RicardoJBarrios/acuario-veril/03_pendientes/disenos-3d/bactoflex-mini/README.md

# Diseños de cestas BactoFlex Mini

Este proyecto conserva **dos versiones distintas** del diseño de cesta y
tapa. Son alternativas documentadas por separado; la nueva versión modular no
elimina ni reemplaza la otra.

- [Diseño modular 50 × 50 × 100 mm](modular-50x50x100/README.md): plan para
  dos cestas independientes, su modelo paramétrico y una vista CAD. Aún no
  impreso ni validado físicamente.
- [Versión 107 × 57 × 105 mm](version-107x57x105/README.md): modelo y archivos
  de fabricación de la otra versión, conservados en su propia carpeta.

La licencia compartida se conserva en [`LICENSE`](LICENSE). Cada carpeta
describe el estado y los límites de su propio modelo y derivados.
