RicardoJBarrios/acuario-veril/01_verilpedia/02_biologia/03_cnidarios-sesiles/README.md

# Cnidarios sésiles

Esta categoría reúne organismos sésiles o principalmente sésiles del filo Cnidaria que pueden formar parte de un acuario de arrecife. Incluye corales, gorgonias, anémonas, coralimorfarios, zoántidos y otros organismos coraliformes.

## Responsabilidad documental

Las fichas describen identidad, función, necesidades generales, crecimiento, agresividad, compatibilidad y límites de interpretación. Las decisiones concretas de selección y colocación se documentan en la [implementación de Veril](../../../02_configuracion/README.md) y en las dimensiones correspondientes.

## Fichas disponibles

- [Corales](01_corales/README.md): corales blandos, LPS, NPS y SPS
- [Análogos coraliformes](02_analogos-coraliformes/README.md): anémonas, coralimorfarios y zoántidos
- [*Aiptasia* y majano](aiptasia-y-majano.md): anémonas oportunistas y límites de identificación
- [Salud de corales](01_corales/06_salud/README.md) y [plagas asociadas](01_corales/05_plagas/README.md)

## Referencias cuantitativas para interpretar las fichas

Las fichas individuales deben incluir una tabla de parámetros medibles según la [plantilla de organismos](../plantilla-ficha-organismo.md). La siguiente tabla distingue referencias generales de acuariofilia y la configuración local; no son límites fisiológicos universales ni sustituyen un dato publicado para la especie.

| Magnitud | Referencia cuantitativa | Alcance |
| --- | --- | --- |
| Temperatura | Veril: preferida **25–26 °C**, objetivo normal **24,5–26,5 °C**; **24–24,5 °C** fresca; **23–24 °C** excursión fría, investigar si persiste; **<23 °C** fuera del objetivo; **<22 °C** revisión prioritaria. Banda cálida vigente: **26,5–27,5 °C** | Criterio local del sistema, no tolerancia declarada de cada especie; los límites publicados de cada especie pueden ser más restrictivos |
| Salinidad | Veril: objetivo **`S_P = 35`** | Consigna del sistema, no intervalo de tolerancia de cada organismo |
| pH | Referencia general de acuario de arrecife **8,0–8,4** | Orientación general; registrar escala y método si se conocen |
| PAR de corales blandos | **50–150 µmol fotones m⁻² s⁻¹** como intervalo inicial de grupo | Referencia de cuidado acuarístico; especies y morfos pueden diferir |
| PAR de LPS | **50–150 µmol fotones m⁻² s⁻¹** como intervalo inicial de grupo | No sustituye un rango de especie. Hay LPS con necesidades distintas |
| PAR de SPS | **200–300 µmol fotones m⁻² s⁻¹** como referencia inicial para géneros exigentes; *Anacropora* se documenta en **100–300** | No extrapolar el extremo alto a toda especie SPS |
| PAR de NPS | No aplica como fuente nutricional | Indicar que la luz no aporta nutrición fotosintética; el fotoperiodo del acuario no equivale a necesidad de PAR |
| Velocidad del flujo | **5–20 cm/s** puede servir como banda experimental de partida para estudiar corales pétreos; no es un objetivo universal de colocación | Estudios distintos obtienen respuestas específicas de especie, morfología y régimen. No convertir caudal de bomba o renovaciones/h en velocidad en la colonia |
| Volumen mínimo | No existe un mínimo universal en litros para un cnidario sésil | Priorizar área disponible, dimensiones adultas, movilidad, distancia de contacto y capacidad de alimentación/exportación |

El PAR se medirá bajo el agua en la posición y altura previstas para el organismo, con el **DanoPlus DP-414** de Veril. Registrar el valor en µmol fotones m⁻² s⁻¹, la posición, orientación del sensor, profundidad, fotoperiodo y perfil de la luminaria. Porcentaje de potencia, vatios, altura del coral y color visual no permiten deducir el PAR local.

Los intervalos de **5–20 cm/s** reúnen velocidades ensayadas en estudios de corales, no una prescripción común a todos los cnidarios. Por ejemplo, *Balanophyllia europaea* capturó más presas a **5 cm/s** en un ensayo, mientras que *Sinularia flexibilis* mostró su mayor crecimiento medio a **11 cm/s** bajo las condiciones de otro ensayo. No se promediarán como si fueran medidas equivalentes ni se trasladarán directamente a otra especie. Se medirán en la ubicación de la colonia con un método de velocidad local; si no se dispone de medidor, la velocidad queda pendiente aunque se registre el comportamiento del tejido como observación auxiliar.

Fuentes cuantitativas:

- [Tidal Gardens: Acropora](https://tidalgardens.com/articles/coral-care-articles/acropora-coral-care.html), alrededor de 300 PAR en sus sistemas de mantenimiento y advertencia de aclimatación
- [Tidal Gardens: Montipora](https://tidalgardens.com/articles/coral-care-articles/montipora-coral-care.html), 125–150 PAR como inicio y 200–300 PAR en sus sistemas
- [Tidal Gardens: Anacropora](https://tidalgardens.com/articles/coral-care-articles/anacropora-coral-care.html), 100–300 PAR
- [Tidal Gardens: Goniopora](https://tidalgardens.com/articles/coral-care-articles/goniopora-coral-care.html), recomendación 75–125 PAR y experiencia entre 50 y más de 200 PAR
- [Schutter et al., 2007: flujo y crecimiento de *Sinularia flexibilis*](https://doi.org/10.1016/j.jembe.2007.06.007), medición experimental; mayor crecimiento medio a 11 cm/s bajo sus condiciones
- [Cocito et al., 2012: flujo y captura de presas de *Balanophyllia europaea*](https://doi.org/10.1017/S002531541100146X), velocidades ensayadas de 2,5, 5, 7,5 y 15 cm/s; mayor captura a 5 cm/s

Cuando una ficha no tenga un intervalo de especie, deberá decirlo explícitamente y usar los valores generales solo como punto de partida de medición, no como garantía de compatibilidad. La ficha también identificará necesidades que no puedan reducirse a un valor único, por ejemplo la turbulencia, dirección del flujo, expansión de tentáculos o alimentación de NPS.
