RicardoJBarrios/acuario-veril/01_verilpedia/04_hardware/urna/espuma.md

# Espuma de apoyo

## Producto

La interfaz entre el tablero y la base de la urna será una pieza continua de goma EVA BIBODU.

- Formato del rollo: **150 × 32 cm**
- Pieza para la urna: **75 × 32 cm**
- Grosor: **5 mm**
- Densidad declarada: **80 kg/m³**
- Dureza declarada: **25 kPa**
- Material declarado: **100 % EVA foam**
- Color: **Negro**

La pieza de 75 × 32 cm cubre una superficie aproximada de **0,24 m²** y deja un sobrante de aproximadamente 75 × 32 cm.

## Función

La EVA forma una interfaz continua entre el tablero y la base de vidrio, reparte el contacto y absorbe pequeñas irregularidades superficiales. La pieza se colocará completa, sin solapes ni juntas, sobre un tablero rígido, plano, limpio y nivelado.

## Colocación

La pieza se extenderá bajo toda la base, sin pliegues, cortes, arrugas ni bordes levantados. Se mantendrá seca y sin adhesivo salvo indicación del fabricante de la urna.

## Datos comerciales

El anuncio del producto declara impermeabilidad y moldeabilidad con calor. No se dispone de una ficha técnica primaria que detalle la absorción de agua, la deformación permanente, la capacidad de carga prolongada o la compatibilidad química con silicona, vidrio, vinilado y agua salada.

La espuma quedará bajo la urna y no estará en contacto directo con el agua del acuario.

## Estado

- Material: **EVA BIBODU de 5 mm**
- Medida de la pieza: **75 × 32 cm**
- Pieza continua: Disponible a partir del rollo documentado
- Aceptación del fabricante de la urna: Pendiente
- Nivelación del tablero: Pendiente de comprobación

## Referencias

- [BIBODU, rollo de goma EVA de 150 × 32 cm, 5 mm y 80 kg/m³](https://oficina.wikicolegios.com/comprar/bibodu-pack-de-2-rollos-de-goma-eva-5mm)
- [Artículo técnico sobre comportamiento mecánico de EVA de célula cerrada de 80 kg/m³](https://pmc.ncbi.nlm.nih.gov/articles/PMC10780418/)
- [EVA marina de célula cerrada: propiedades declaradas por fabricante](https://www.ycdeck.com/faq)
- [Ficha técnica de espuma EVA de célula cerrada con ensayos de absorción y compresión](https://foamatelier.nl/basis/data/mediablocks/TechnischeFicheEVAFoam.pdf)
