RicardoJBarrios/acuario-veril/01_verilpedia/04_hardware/dd-h2ocean-compact-ato/graf-barril-agroalimentario-15l.md

# Barril agroalimentario GRAF de 15 l

## Identificación

- **Fabricante o marca:** GRAF
- **Tipo:** depósito exterior rígido
- **Capacidad nominal:** 15 l
- **Material:** polietileno apto para uso alimentario
- **Color:** blanco translúcido
- **Formato:** redondo, con asa de transporte y grifo incluido
- **Medidas comerciales:** 35 cm de diámetro × 30 cm de altura
- **Fabricación declarada:** Alemania

## Características declaradas

El depósito está destinado a conservar líquidos y permite comprobar visualmente el nivel gracias a su material translúcido. La ficha comercial lo describe como hermético, de paredes gruesas y apto para conservar agua, zumo o vino, entre otros líquidos.

| Parámetro | Valor declarado |
| --- | --- |
| Uso | Contenedor de agua potable o no potable |
| Capacidad | 15 l |
| Material principal | Polietileno |
| Tipo de depósito | Rígido |
| Protección UV | Sí |
| Resistencia a heladas | No; sensible a las heladas |
| Garantía | 3 años |
| Peso neto | 1 kg |
| Enterrable | No |

## Uso en Veril

Este depósito se reservará exclusivamente para agua RO/DI de reposición.

- No se almacenará agua salada
- No se añadirán suplementos, fertilizantes, medicamentos ni productos de mantenimiento
- Se mantendrá cerrado y protegido de contaminación, polvo y salpicaduras
- El grifo no sustituye la protección antisifón del tubo de reposición del ATO
- La bomba del ATO se instalará de forma que no pueda aspirar sedimento del fondo
- La capacidad útil real y la autonomía se registrarán después de la instalación

Las dimensiones del depósito deben comprobarse junto con el espacio de instalación, el recorrido del tubo y el acceso para llenado y limpieza. La capacidad nominal de 15 l no equivale necesariamente al volumen que conviene utilizar en cada ciclo de reposición.

## Estado

**Confirmado:** depósito seleccionado para alimentar el D-D H2Ocean Compact ATO de Veril.

**Pendiente de ejecución:** confirmar la referencia comercial exacta, medir el espacio disponible, fijar el recorrido del tubo, comprobar la estanqueidad del grifo y registrar la autonomía real.

## Fuente

Descripción comercial de Leroy Merlin facilitada para la documentación de Veril. La ficha comercial identifica la marca como **GRAF** y declara las características recogidas en este documento.
