RicardoJBarrios/acuario-veril/01_verilpedia/03_parametros/temperatura.md

# Temperatura

## Qué es y qué mide

La temperatura describe el estado térmico del agua en un momento y una ubicación determinados. Condiciona la velocidad de muchas reacciones químicas, el metabolismo de los organismos, la actividad microbiana y la solubilidad de los gases.

La respuesta biológica no depende únicamente de la temperatura instantánea. También importan la duración de la exposición, la magnitud de la desviación respecto al régimen habitual, la velocidad con la que se alcanza y el historial térmico del organismo o la colonia.

## Qué aporta y por qué importa

La temperatura afecta a prácticamente todos los procesos del acuario:

- Modifica el metabolismo y el consumo de oxígeno
- Influye en la solubilidad de los gases
- Altera la velocidad de crecimiento, respiración y descomposición
- Participa en la química del sistema carbonato
- Modifica, junto con el pH y la salinidad, el equilibrio entre NH₄⁺ y NH₃ y la fracción de amoníaco no ionizado
- Modifica la densidad del agua y condiciona la interpretación de instrumentos dependientes de temperatura, como determinadas mediciones de gravedad específica, conductividad o refracción
- Condiciona el intercambio de calor entre el agua, los equipos y el ambiente

Las velocidades metabólicas y microbianas suelen depender de la temperatura dentro de determinados intervalos, pero la relación no es indefinidamente creciente: cada comunidad presenta rangos, óptimos y límites propios.

## Niveles orientativos

Como referencia operativa doméstica puede utilizarse aproximadamente **24–26 °C** para muchas comunidades tropicales de arrecife. Este intervalo no constituye un rango fisiológico universal ni permite establecer por sí solo un umbral de estrés térmico.

La estabilidad y la velocidad de cambio son importantes, pero no sustituyen la compatibilidad del valor absoluto con los organismos mantenidos. Una temperatura estable fuera de su intervalo tolerable sigue constituyendo una condición inadecuada.

No existe un umbral universal de blanqueamiento expresable como una única temperatura. El estrés depende en gran medida del régimen térmico habitual de procedencia, de la especie, la población, la colonia, los simbiontes y la duración e intensidad de la exposición.

## Exposición y estrés térmico

Una excursión breve y moderada puede producir una respuesta distinta de una exposición sostenida a la misma temperatura. Del mismo modo, los umbrales de estrés térmico no son idénticos entre especies, poblaciones, colonias o asociaciones simbióticas.

La aclimatación fisiológica de un individuo o una colonia no debe confundirse con la adaptación evolutiva de una población. La aclimatación puede modificar la respuesta dentro de ciertos límites, pero no convierte cualquier temperatura en compatible ni elimina el riesgo de estrés acumulado.

## Balance y carga térmica

La temperatura del agua resulta del balance entre ganancias y pérdidas de calor. La temperatura ambiente no determina por sí sola la temperatura del acuario: equipos sumergidos, iluminación, radiación, evaporación, ventilación, conducción y geometría del sistema pueden desplazarla respecto al ambiente.

La **carga térmica** representa el conjunto de aportes de calor que el sistema debe disipar, incluidos equipos sumergidos, iluminación, ambiente y radiación. Su importancia depende también de la capacidad de disipación por conducción, convección, evaporación y ventilación.

La iluminación puede incrementar la temperatura por transferencia de energía desde la luminaria y el entorno; este efecto debe distinguirse de la propia actividad fotosintética.

El enfriamiento evaporativo puede reducir eficazmente la temperatura, pero aumenta la pérdida de agua y hace más dependiente al sistema de una reposición correcta. La evaporación elimina principalmente agua, no una cantidad equivalente de sales, por lo que vincula directamente regulación térmica y estabilidad de salinidad.

## Temperatura y margen de oxígeno

El aumento de temperatura puede reducir simultáneamente la solubilidad del oxígeno y aumentar la demanda metabólica de los organismos y microorganismos. Por ello, el riesgo térmico puede reducir también el margen disponible frente a hipoxia, especialmente durante la oscuridad, ante una elevada carga respiratoria o tras un fallo de circulación.

El efecto térmico sobre el oxígeno debe interpretarse junto con salinidad y presión atmosférica cuando se compara una concentración medida con la saturación esperada. La relación con el oxígeno no permite establecer por sí sola un umbral térmico universal.

## Fuentes y comportamiento

La temperatura puede variar:

- Entre el día y la noche
- Según la estación
- Por la iluminación, las bombas y otros equipos
- Por ventilación, evaporación o temperatura ambiente
- Por el uso de calefacción o refrigeración
- Por cambios en la circulación o en la mezcla del agua

Una variación pequeña y reproducible dentro de condiciones compatibles puede formar parte del régimen normal del sistema. El objetivo no debe ser eliminar toda variación, sino evitar exposiciones incompatibles, oscilaciones excesivas y cambios rápidos no controlados.

### Gradientes térmicos

En un sistema bien mezclado se espera una temperatura relativamente homogénea, pero pueden aparecer diferencias locales junto a calentadores, salidas calientes, superficies iluminadas o cámaras con renovación reducida. Un gradiente persistente debe interpretarse como información sobre la distribución térmica y la hidráulica, no únicamente como un problema del sensor.

## Qué pasa si está bajo

Una temperatura baja puede reducir la velocidad metabólica y ralentizar procesos biológicos. Un descenso rápido puede causar estrés y modificar simultáneamente la solubilidad de los gases, los equilibrios químicos y la interpretación de instrumentos dependientes de temperatura; no modifica por sí solo la cantidad de sales presentes.

Un cambio térmico puede modificar el pH y la especiación del sistema carbonato aunque no exista una adición de ácido, base o CO₂. Por ello, las comparaciones químicas deben conservar la temperatura de medición o aplicar la corrección apropiada.

## Qué pasa si está alto

Una temperatura alta puede acelerar el metabolismo y aumentar el consumo de oxígeno. Si coincide con pH elevado y nitrógeno amoniacal presente, debe vigilarse el equilibrio entre NH₄⁺ y NH₃ y la fracción de amoníaco no ionizado.

El sobrecalentamiento sostenido puede reducir la solubilidad del oxígeno, elevar la demanda respiratoria y producir estrés térmico acumulado. La importancia depende del valor, la duración, la velocidad de cambio y la comunidad afectada.

## Cómo se mide

- Termómetro digital con sonda sumergible
- Sonda electrónica integrada en un controlador, si se calibra y contrasta periódicamente
- Termómetro de vidrio con líquido adecuado, preferentemente sin mercurio, como comprobación independiente
- Termómetro infrarrojo, solo como referencia de superficies; no sustituye una medición del agua en profundidad

Un termómetro infrarrojo mide la radiación emitida por la superficie observada y no la temperatura del agua en profundidad. El vidrio, los reflejos y la emisividad pueden sesgar la lectura.

## Limitaciones de la medición

La lectura depende de la calibración, la resolución, el tiempo de respuesta, la posición del sensor y la mezcla del sistema. Debe evitarse colocar la sonda pegada al calentador, a una salida caliente, en una cámara con renovación insuficiente o en una zona que pueda quedar parcialmente expuesta al aire.

Un sensor puede registrar una zona local y no representar todo el volumen si existen gradientes térmicos o fuentes de calor cercanas. La medición y el control deben distinguirse: un controlador puede actuar correctamente sobre una lectura sesgada por la ubicación del sensor.

## Mecanismos de regulación

La temperatura se regula mediante calefacción, ventilación, enfriamiento o reducción de fuentes de calor. Las correcciones deben realizarse de forma controlada, evitando introducir una segunda perturbación térmica innecesariamente rápida. En una emergencia, la prioridad es recuperar condiciones compatibles mientras se controla la velocidad y la respuesta de los organismos.

Cuando las consecuencias de un fallo sean relevantes, la medición, el control y el corte de seguridad no deberían depender necesariamente de un único punto de fallo. La seguridad térmica debe considerar tanto el sobrecalentamiento como la pérdida de calefacción o un enfriamiento excesivo.

El control térmico suele utilizar una histéresis o banda de actuación para evitar ciclos rápidos de encendido y apagado. Una banda demasiado estrecha puede aumentar la frecuencia de conmutación sin proporcionar una mejora biológica relevante.

La capacidad de regulación depende del volumen, el ambiente, la evaporación, la iluminación, la carga térmica y la circulación. Un fallo de circulación puede alterar simultáneamente la mezcla térmica y el margen de oxígeno.

## Interpretación y respuesta

Medir con un termómetro fiable, comprobarlo periódicamente y registrar máximas y mínimas. Una serie térmica se describe mejor mediante temperatura media, máxima, mínima, amplitud diaria y velocidad de cambio que mediante una única lectura.

```text
ΔT_diaria = T_máxima − T_mínima
tasa de cambio = ΔT / Δt
```

No existe una tasa universalmente segura para todos los organismos, pero debe conservarse al interpretar incidentes, aclimataciones o intervenciones.

Una desviación debe interpretarse junto con máximas, mínimas, amplitud, velocidad del cambio, oxígeno, salinidad, pH y comportamiento de los organismos.

## Cómo evaluar la temperatura en funcionamiento

- **Medición:** Sensor contrastado, ubicación representativa, resolución suficiente y registro continuo o de máximas y mínimas
- **Régimen:** Media, máxima, mínima, amplitud diaria, tasa de cambio y patrón estacional cuando exista
- **Seguridad:** Control de sobretemperatura, detección de fallo de calefacción, respuesta ante pérdida de circulación y margen frente a máximas ambientales previsibles
- **Biología:** Comportamiento, respiración, respuesta de corales y relación con oxígeno y fotoperiodo

## Otros parámetros relacionados

- **pH y amonio:** La temperatura, el pH y la salinidad modifican el equilibrio entre NH₄⁺ y NH₃ y la fracción de amoníaco no ionizado
- **Oxígeno:** El agua caliente suele contener menos oxígeno en saturación y los organismos pueden aumentar su demanda metabólica
- **Salinidad:** La temperatura afecta a la densidad, la conductividad y la lectura de gravedad específica, pero no modifica por sí sola la cantidad de sales presentes
- **Sistema carbonato:** La temperatura modifica las constantes de equilibrio y los productos de solubilidad de las fases minerales, alterando la especiación y el estado de saturación incluso sin que cambien inicialmente TA o DIC
- **Metabolismo:** Una subida térmica puede aumentar consumo, producción de residuos y demanda de oxígeno dentro de los límites fisiológicos de la comunidad
- **Hidráulica:** La circulación distribuye el calor y condiciona la existencia de gradientes térmicos locales
- **Iluminación:** La luminaria puede aportar carga térmica independientemente de la actividad fotosintética

## Qué no es la temperatura

La temperatura:

- No es una cifra independiente del tiempo
- No se define únicamente por una lectura instantánea
- No demuestra una oxigenación adecuada
- No compensa una mala calidad química
- No permite inferir el metabolismo exacto mediante una regla universal
- No convierte una oscilación natural en necesariamente segura para cualquier organismo
- No demuestra ausencia de estrés porque los animales sigan abiertos o activos

## Qué no demuestra una lectura aislada

Una temperatura aparentemente normal no compensa una salinidad incorrecta, falta de oxígeno, pH inestable o acumulación de compuestos nitrogenados. Tampoco demuestra que no exista estrés térmico acumulado, un gradiente local o un margen insuficiente frente a una perturbación previsible.

## Errores comunes

- Perseguir una consigna como 25,0 °C mediante conmutaciones constantes
- Utilizar un único sensor sin contrastarlo
- Colocar la sonda junto al calentador o una salida caliente
- Ignorar máximas y mínimas diurnas y nocturnas
- Enfriar bruscamente una hipertermia sin controlar la respuesta
- Interpretar la temperatura ambiente como temperatura del agua
- Olvidar que los ventiladores aumentan la evaporación y la dependencia de la reposición
- Calibrar todos los sensores contra otro sensor no verificado
- Ignorar que un fallo de bomba puede alterar simultáneamente la mezcla térmica y el oxígeno

## Terminología

| Expresión | Qué representa |
| --- | --- |
| Temperatura del agua | Estado térmico medido en una muestra o ubicación concreta |
| Carga térmica | Aportes de calor que el sistema debe disipar |
| Inercia térmica | Resistencia del sistema a cambiar de temperatura por su masa térmica y su intercambio de calor |
| Amplitud diaria | Diferencia entre la temperatura máxima y mínima de un ciclo diario |
| Tasa de cambio | Variación de temperatura por unidad de tiempo |
| Estrés térmico | Respuesta biológica a una temperatura, desviación, duración o velocidad de cambio incompatibles o exigentes |
| Aclimatación | Ajuste fisiológico dentro de los límites de un organismo o colonia expuestos a nuevas condiciones |
| Adaptación | Cambio heredable a escala poblacional o evolutiva; no equivale a aclimatación individual |
| Histéresis | Banda de diferencia entre los puntos de activación y desactivación de un controlador |
| Infrarrojo | Medición de radiación superficial que no equivale directamente a la temperatura del agua en profundidad |

## Fuentes

- [USGS: Temperature and water](https://www.usgs.gov/water-science-school/science/temperature-and-water), efectos de la temperatura sobre solubilidad, reacciones y organismos acuáticos
- [NOAA: Temperature and oxygen tolerances of marine species](https://coastalscience.noaa.gov/news/temperature-and-oxygen-tolerances-of-marine-species-predict-their-distributions/), relación entre temperatura, oxígeno y tolerancia de organismos marinos
- [Berkelmans y van Oppen: The susceptibility and resilience of corals to thermal stress: adaptation, acclimatization or both?](https://doi.org/10.1111/j.1365-294X.2010.04575.x), susceptibilidad, resiliencia, aclimatación y asociaciones simbióticas
- [Safaie et al.: A global analysis of coral bleaching over the past two decades](https://doi.org/10.1073/pnas.1808831115), relación entre intensidad, frecuencia e historia del estrés térmico y blanqueamiento
- [ReefCalcs: Parámetros ideales de arrecife](https://reefcalcs.com/guides/ideal-reef-parameters/), referencia práctica de rango y estabilidad
- [ReefCalcs: Calculadora de refrigeración](https://reefcalcs.com/calculators/chiller-btu/), relación práctica entre temperatura, carga térmica y ambiente
