RicardoJBarrios/acuario-veril/04_operaciones/2026/09/2026-09-28-vaciado-remanente-barril-y-nivel-c3.md

# 2026-09-28 — Vaciado del remanente del barril y nivel de C3

## Estado

Operación documentada a partir de una observación comunicada por el propietario.
La hora se estima a partir de «hace un minuto» respecto al mensaje recibido a
las 09:13 WEST; no se comunicó una hora de reloj exacta.

## Ejecución comunicada

El propietario vació en el sistema el remanente de agua que quedaba en el barril
tras la operación del 26 de septiembre. Confirma que entraron **1,75 L** en el
sistema y que el barril quedó vacío.

Por el contexto de las operaciones recientes, se interpreta que la cota
comunicada después de la transferencia corresponde al nivel de agua de C3,
medido desde su borde superior. Si se refería a otra cámara o referencia, este
registro debe corregirse.

## Resultado observado

Después de vaciar el remanente, el nivel de C3 quedó a **14 cm (140 mm) del
borde superior**, según la medición comunicada por el propietario. No se indicó
el instrumento ni se confirmó que se usara exactamente el mismo punto del borde
que en la lectura anterior.

Como comparación contextual, el 27 de septiembre se había comunicado una cota
de **16 cm (160 mm)**. La lectura actual está 20 mm más cerca del borde; la
diferencia describe únicamente las dos cotas comunicadas.

## Telemetría asociada de Home Assistant

La documentación consultada no identifica una entidad de Home Assistant que
mida el nivel de C3. No se adjunta una lectura digital como corroboración de la
cota: los **140 mm** son una medición física comunicada por el propietario. En
esta operación no se obtuvo una consulta en vivo de Home Assistant.

## Interpretación y límites

- El propietario confirma un volumen transferido de **1,75 L** y que el barril quedó vacío; la cota final comunicada para C3 es de 140 mm desde el borde superior.
- La diferencia de 20 mm respecto a los 160 mm comunicados el día anterior solo es comparable si se mantuvieron la cámara, el borde y el punto de referencia; esos detalles no se confirmaron expresamente.

## Fuentes internas

- [Reposición manual y lectura de salinidad del 26 de septiembre](2026-09-26-reposicion-manual-y-lectura-de-salinidad.md)
- [Prueba del DanoPlus, PAR ambiental y nivel de C3 del 27 de septiembre](2026-09-27-prueba-danoplus-nivel-c3-y-par.md)
