RicardoJBarrios/acuario-veril/01_verilpedia/05_productos/09_fritzzyme-9/fritzzyme-9.md

# FritzZyme 9 Saltwater

## Identificación

- Producto: **FritzZyme 9 Saltwater Nitrifying Bacteria**
- Fabricante: **Fritz Aquatics**
- Envase adquirido: **946 ml**
- Referencia oficial del formato de 946 ml: **80205**; la referencia **80203** corresponde al formato de 237 ml
- Cobertura indicada en la tabla oficial para el envase de 946 ml: hasta **160 galones estadounidenses / 606 L**; por cálculo, esa cifra es aproximadamente compatible con la pauta de sistema establecido, no con la dosis inicial de sistema nuevo

La capacidad de 40 galones debe interpretarse junto con la pauta aplicable. Fritz publica una dosis distinta para sistemas nuevos y sistemas establecidos.

## Función declarada por el fabricante

FritzZyme 9 contiene cepas vivas de bacterias nitrificantes específicas para agua salobre y salada. El fabricante declara que ayudan a sembrar rápidamente el biofiltro y a transformar amonio y nitrito.

Esta es una afirmación del fabricante. La documentación pública consultada no permite identificar aquí las cepas concretas del envase adquirido ni su viabilidad por lote.

## Uso y condiciones publicadas

- Sistema nuevo: la etiqueta del envase disponible indica **118 ml por 19 L** (4 fl oz por 5 galones estadounidenses); la página oficial redondea la cantidad a **119 ml**
- Sistema establecido: **30 ml por 19 L** (1 oz por 5 galones estadounidenses)
- La etiqueta indica que la dosis puede repetirse diariamente si es necesario y que para una carga elevada de animales puede aumentarse hasta diez veces; esto no forma parte de la receta adoptada para Veril
- La web oficial también contempla un aumento de hasta diez veces para sistemas con carga biológica elevada
- Temperatura ideal: **25–30 °C**
- Salinidad: **15–40 ppt** (densidad específica 1.011–1.030)
- pH: **7,3–8,0**
- Alcalinidad mínima: **4,5 dKH** o 80,5 ppm KH
- Fosfato: Por encima de 0 ppm
- La etiqueta del envase indica detener el uso de esterilizadores UV antes de añadir el producto y hasta cuatro días después de cada aplicación
- La web oficial indica mantener apagados el skimmer y los esterilizadores UV durante al menos cinco días después de cada aplicación; el plan de Veril conserva este plazo más largo
- Mantener flujo o aireación adecuados

Fritz indica que en un sistema nuevo debe existir una fuente de amonio, como Fishless Fuel, para iniciar el ciclado sin peces.

## Conservación y límites

El fabricante indica que el producto no necesita refrigeración para conservarse estable a largo plazo. No debe congelarse ni sobrecalentarse y debe almacenarse en un lugar fresco y oscuro. Debe utilizarse antes de la fecha de caducidad.

Los cambios de color u olor pueden producirse entre envases. Un olor fuerte a azufre no demuestra por sí solo que el producto haya perdido su actividad. La comprobación funcional requiere medir la transformación de amonio y nitrito bajo una carga conocida.

## Aplicación prevista en Veril

FritzZyme 9 se utilizará como inoculante bacteriano principal del ciclado sin peces, junto con AF Bio Sand, Fishless Fuel y el agua de mar filtrada con UV de Elite Reef Kanarias. La dosis de Veril se calcula en el [plan de ciclado](../../../03_pendientes/ciclado/plan.md), usando la base nominal adoptada de **75 L para el sistema completo**.

La etiqueta fotografiada del envase disponible indica **118 ml por 19 L** para un sistema nuevo. Aplicada a los **75 L** nominales de Veril, equivale a **465,8 ml**, que se redondean a **466 ml**. La web oficial usa el valor redondeado de 119 ml por 19 L, que daría 469,7 ml. Para el plan de Veril prevalece la etiqueta del envase concreto. El formato adquirido contiene **946 ml**, suficiente para esta dosis.

El vendedor recomendó utilizar la mitad de la dosis. Esa recomendación no aparece identificada como pauta específica para FritzZyme 9 en la documentación oficial consultada. Para la receta de ciclado de Veril se adopta la dosis completa de sistema nuevo indicada por la etiqueta, aproximadamente **466 ml para 75 L**. La recomendación de media dosis se conserva como antecedente comercial no adoptado, no como decisión pendiente ni como pauta del fabricante. La fotografía disponible no muestra lote ni caducidad; ambos se comprobarán antes de dosificar.

La [fotografía de la etiqueta del envase de Veril](etiqueta-envase-veril-2026-09-24.jpg), tomada el 24 de septiembre de 2026, conserva la pauta y las instrucciones visibles del producto adquirido. El fabricante indica agitarlo y añadirlo directamente al acuario, retirar el cloro previamente y mantener circulación o aireación. La etiqueta menciona apagar UV antes y durante los cuatro días posteriores; la web oficial amplía la precaución a skimmer y UV durante al menos cinco días, criterio que sigue el plan.

## Fuente

- [Fritz Aquatics: FritzZyme 9 Saltwater](https://fritzaquatics.com/product/fritzzyme-9-saltwater/)
