RicardoJBarrios/acuario-veril/04_operaciones/2026/09/2026-09-17-observaciones-flujo-temperatura-y-sustrato.md

# 2026-09-17 — Observaciones de flujo, temperatura y sustrato

## Naturaleza del registro

Este registro reúne observaciones comunicadas por el propietario durante la
preparación de Veril. No incorpora fuentes externas, datos de fabricante,
interpretaciones de vídeos ni conclusiones sobre la sostenibilidad del régimen.
Cuando no se conoce la fecha exacta de una observación, se conserva como tal y
no se infiere.

## Estado físico observado

- El ciclado todavía no había comenzado.
- En el momento de estas observaciones no había arena: sólo estaba colocada la
  roca.
- El nivel de agua de referencia se situaba aproximadamente **37 mm** por
  debajo del borde superior del acuario.
- La aragonita utilizada se observó como un material pesado que se hunde con
  rapidez al incorporarlo.

## Bomba de movimiento

El propietario comunicó la siguiente colocación y configuración actual de la
bomba de olas:

- Aproximadamente **12 cm** desde el borde del acuario; esta medida se debe
  interpretar junto con el nivel de agua de **37 mm** indicado arriba.
- Aproximadamente **53 mm** desde la parte trasera, descontando de esa medida
  el grosor del cristal trasero.
- Orientada hacia el frente.
- `Constant mode`.
- `Flow percent: 40 %`.
- `Cycle: 0,4 s`, indicado como el mínimo disponible.
- `Master` configurado, porque el controlador no permite dejarlo sin ajustar.

También se comunicó que existe un vídeo local en Descargas donde se aprecia el
efecto conjunto de la bomba de salida y la Tourbon sobre la superficie del
agua. Este registro no interpreta ese vídeo ni lo usa como fuente externa.

## Prueba dinámica de circulación

Con la Mantis configurada entonces al 40 %, se realizó una prueba dinámica con
las partículas minúsculas de aragonita que permanecieron en suspensión en la
superficie. El resultado observado fue:

- Las partículas más pequeñas que permanecieron suspendidas en la superficie
  recorrieron circularmente el acuario.
- El recorrido rodeaba la roca.
- El comportamiento observado coincidió con el comportamiento esperado para
  esa prueba.

La prueba acredita un circuito superficial continuo alrededor de la roca bajo
esa configuración y durante esa observación. No acredita por sí sola la
renovación de todos los huecos, el corredor trasero o las zonas inferiores, ni
la ausencia de depósitos en otras condiciones o tras añadir arena.

## Telemetría asociada

No se consultó telemetría de Home Assistant para esta prueba. La evidencia
registrada es la observación directa comunicada por el propietario.

**Resultado:** Operación documentada sin telemetría pertinente o disponible.

## Temperatura del agua

El propietario indicó, tras revisar la evolución registrada por el medidor de
temperatura de Veril, que el agua se había mantenido entre **26 y 30 °C**
durante el tiempo observado hasta ese momento. En esta conversación no se
establecieron aquí el periodo exacto, la entidad del sensor ni la resolución de
la serie, por lo que no se añaden.

También indicó que el despacho dispone de aire acondicionado y que el periodo
coincidía con una ola de calor considerada inusual en Santa Cruz de Tenerife.
Este registro conserva esa comunicación como contexto aportado por el
propietario; no incorpora comprobaciones meteorológicas externas.

## Límites de la observación

Estas observaciones no determinan todavía si el rango térmico es sostenible,
si la bomba renueva todas las zonas del acuario ni si la distribución de
partículas se mantiene al añadir arena. Esas cuestiones quedan abiertas para
pruebas posteriores del sistema real.
