RicardoJBarrios/acuario-veril/01_verilpedia/08_practicas/04_diagnostico-y-bioseguridad/arbol-de-diagnostico.md

# Árbol de diagnóstico

```mermaid
flowchart TD
  A[Observación nueva] --> B{¿Afecta a un animal?}
  B -- No --> C{¿Película, moco o filamentos?}
  B -- Sí --> D{¿Hay pérdida de tejido o respiración alterada?}
  C -- Película parda --> E[Comparar diatomeas, ciano y dinos]
  C -- Moco o burbujas --> E
  C -- Filamentos --> F[Comparar algas y organismos sésiles]
  D -- No --> G[Revisar adaptación, muda, detrito y plagas]
  D -- Sí --> H[Registrar velocidad y separar causa posible]
  E --> I{¿La identificación cambia el tratamiento?}
  I -- Sí --> J[Microscopio o fuente competente]
  I -- No --> K[Retirada física y observación proporcional]
  F --> K
  G --> L[No eliminar organismos beneficiosos por apariencia]
  H --> M[Hospital o aislamiento según riesgo]
```

Ante una película marrón conviene comprobar si se desprende como polvo, si forma una matriz viscosa, si produce burbujas, si se concentra en arena y si disminuye durante la oscuridad. Estos datos solo separan posibilidades: *Ostreopsis*, *Amphidinium*, *Prorocentrum* y otros grupos pueden ser bentónicos y requieren una identificación más precisa si se plantea una intervención específica.

Nunca se debe apagar por completo la circulación, llevar nitrato o fosfato deliberadamente a cero, ni cambiar varias variables a la vez para forzar una lectura visual.
