RicardoJBarrios/acuario-veril/01_verilpedia/05_productos/06_dd-aquarium-solution-aqpr001/dd-aquarium-solution-aqpr001.md

# D-D The Aquarium Solution AQPR001

## Identificación

| Campo | Dato |
| --- | --- |
| Marca | D-D The Aquarium Solution |
| Producto | Refractómetro AQPR001 |
| Estado en Veril | Adquirido |

## Especificaciones declaradas

| Campo | Dato |
| --- | --- |
| Escala principal | Salinidad de agua marina, 0–40 ppt |
| Escala adicional | Gravedad específica de agua marina |
| Compensación | ATC entre 10 y 30 °C de temperatura del instrumento |
| Calibración declarada | 20 °C |
| Cuerpo | Cobre interno para favorecer la estabilización térmica |

## Función documentada

Instrumento óptico destinado a estimar la salinidad o la gravedad específica del agua marina mediante refracción. D-D indica que la escala está preparada para agua de mar real y no para salmuera de cloruro sódico, una diferencia relevante cuando se busca una lectura cercana a 35 ppt.

La compensación automática de temperatura no mide ni corrige directamente la temperatura del agua: compensa la temperatura del instrumento dentro del intervalo indicado. La muestra debe homogeneizarse y la calibración debe hacerse con el instrumento estabilizado a 20 °C.

## Uso en Veril

Se utilizará para comprobar la salinidad del agua de mar recibida y de las preparaciones posteriores. La calibración y el método de medición deben registrarse antes de aceptar una lectura.

## Límites

- Una lectura no demuestra que el instrumento esté correctamente calibrado
- El refractómetro no sustituye la comprobación de la temperatura y de la homogeneidad de la muestra
- La compensación automática de temperatura no elimina la necesidad de calibrar el instrumento a 20 °C
- No se debe convertir automáticamente una lectura de gravedad específica en salinidad sin conocer la escala utilizada
- La suciedad, las gotas retenidas, las burbujas y una muestra no representativa pueden alterar el resultado

## Fuentes

- Manual y escala del instrumento adquirido
- [D-D: True Seawater Refractometer AQPR001](https://www.theaquariumsolution.com/products/true-seawater-refractometer)
- [D-D: compensación de temperatura del refractómetro](https://www.theaquariumsolution.com/refractometer-temperature-compensation)
- [Aplicación química de Veril](../../../02_configuracion/01_dimensiones/05_quimica.md)
