RicardoJBarrios/acuario-veril/01_verilpedia/05_productos/07_eheim-4005843/eheim-4005843.md

# Tubo Eheim 4005843

## Identificación

| Campo | Dato |
| --- | --- |
| Marca | Eheim |
| Referencia | 4005843 |
| Medida disponible | 3 m, 16/22 mm |
| Estado en Veril | Adquirido |

## Especificaciones declaradas

| Campo | Dato |
| --- | --- |
| Color | Antracita |
| Diámetro nominal | 16/22 mm |
| Longitud | 3 m |
| Referencia | 4005843 |
| Uso de catálogo | Manguera Eheim para conexiones de filtración |

## Función documentada

Tubo flexible Eheim para conducción de agua en instalaciones de acuario. El catálogo lo identifica como manguera antracita de 16/22 mm y 3 m. La medida nominal no garantiza por sí sola compatibilidad con cualquier pasamuros, bomba o racor.

Eheim describe sus mangueras como flexibles y resistentes al estrangulamiento, pero la ruta instalada debe respetar radios, conexiones y sujeciones reales.

## Uso en Veril

Se reserva como material auxiliar para llenados, trasvases y conexiones temporales entre recipientes o cámaras. No forma parte del recorrido permanente de la bomba de retorno.

## Límites

- El recorrido debe comprobarse para evitar estrangulamientos, fugas y esfuerzos sobre los equipos
- No se debe sustituir el tubo de retorno sin una decisión específica y una comprobación de compatibilidad
- El tubo debe cortarse recto y las conexiones deben quedar completamente insertadas y aseguradas
- Para facilitar el montaje de un tubo rígido por frío puede templarse con agua caliente, evitando quemaduras y deformaciones

## Fuentes

- [Copia local del catálogo técnico Eheim](eheim-catalogo-tecnico-en-0923.pdf)
- [Ficha del hardware de la Sicce Micra Plus 600](../../04_hardware/sicce-micra-plus-600/sicce-micra-plus-600.md)
- [Eheim: catálogo de mangueras y referencia 4005843](https://eheim.com/media/3e/b6/2a/1737110772/EHEIM_Haendlerkatalog_EN_0923.pdf)
- [Aplicación hidráulica de Veril](../../../02_configuracion/01_dimensiones/03_hidraulica.md)
