RicardoJBarrios/acuario-veril/02_configuracion/README.md

# Veril: configuración integrada

> Esta ficha integra las decisiones concretas de Veril que se documentan por separado en las fichas del directorio. No sustituye las dimensiones, las fichas de hardware, las fichas de organismos ni los planes operativos.

## Alcance

Veril se configura como un acuario marino de arrecife con un display interior de **594 × 308 mm** y una altura exterior de **400 mm**, con una arquitectura AIO lateral de pequeño volumen, una configuración biológica mixta y una arquitectura de procesamiento basada en el método Berlín.

Además de los aproximadamente **7,5 kg de roca instalados**, el propietario comunica un remanente de roca no utilizado de **aproximadamente 2,5 kg**. La fecha concreta de ese pesaje no consta; el dato se registra en la [operación de pesaje del hardscape](../04_operaciones/2026/09/2026-09-23-pesaje-y-desplazamiento-del-hardscape.md).

El estado material inicial comprende la urna y agua de mar filtrada con UV suministrada para el llenado. El volumen realmente introducido no se midió: el 5 de septiembre se utilizaron recipientes con capacidades nominales de 30, 30 y 20 L, pero el propietario indica que seguramente se trasvasó menos que su capacidad conjunta. El 6 de septiembre se estimó una reposición de unos 7 L. No debe sumarse esta estimación a la capacidad de los recipientes para afirmar un volumen acumulado de agua. Se registraron **7,25 kg de roca** en el inventario inicial y se adquirieron piezas adicionales para las islas y la composición; tras el pesaje del conjunto se adopta **unos 7,5 kg** como masa total orientativa de la roca instalada. El desglose y el alcance del redondeo constan en la [operación del 23 de septiembre](../04_operaciones/2026/09/2026-09-23-pesaje-y-desplazamiento-del-hardscape.md). Además, permanecen fuera del sistema dos bidones de 15 L, uno lleno y otro con una pequeña cantidad; no forman parte del volumen operativo. También están disponibles **7,5 kg de [AF Bio Sand](../01_verilpedia/05_productos/01_af-bio-sand/af-bio-sand.md) de granulometría de referencia 1–2 mm**, un [refractómetro D-D AQPR001](../01_verilpedia/05_productos/06_dd-aquarium-solution-aqpr001/dd-aquarium-solution-aqpr001.md), [FritzZyme 9](../01_verilpedia/05_productos/09_fritzzyme-9/fritzzyme-9.md) en envase de **946 ml** con caducidad indicada de **07/06/2027**, dos [cianoacrilatos Cofan en gel de alta viscosidad](../01_verilpedia/05_productos/04_cofan-cianocrilato-gel/cofan-cianocrilato-gel.md) de **50 g** cada uno, [tubo Eheim](../01_verilpedia/05_productos/07_eheim-4005843/eheim-4005843.md) de **3 m y 16/22 mm**, [epoxi D-D Aquascape Construction Epoxy](../01_verilpedia/05_productos/05_dd-aquascape-construction-epoxy/dd-aquascape-construction-epoxy.md) y [AF Stone Fix](../01_verilpedia/05_productos/03_af-stone-fix/af-stone-fix.md) de **1.500 g**.

También están disponibles para la caracterización y el ciclado el [Salifert Ammonia NH3 Profi Test](../01_verilpedia/05_productos/12_salifert-ammonia-nh3/salifert-ammonia-nh3.md), presentación de 50 tests y caducidad **10/2027**, el [Salifert NO2 Profi Test](../01_verilpedia/05_productos/13_salifert-no2/salifert-no2.md), presentación de 50 tests y caducidad **06/2029**, y un [Tetra Test 7 en 1](../01_verilpedia/05_productos/14_tetra-test-7-en-1/tetra-test-7-en-1.md), presentación de 50 tiras, para pH, KH, GH, NO2, NO3, Cl2 y CO2. Los Salifert de amonio y nitrito serán los métodos principales para seguir el ciclado; las tiras Tetra se utilizarán únicamente como referencia inicial y caracterización orientativa.

La Mantis Tourbon 60 está instalada y su colocación y ajuste actuales se documentan en [Hidráulica](01_dimensiones/03_hidraulica.md). La AI Prime 16HD Reef permanece pendiente de disponibilidad. El propietario comunica que el equipo RO6CB ha llegado el 24 de septiembre de 2026; la etiqueta de la caja está fotografiada, pero el contenido aún no se ha inventariado y el equipo no se ha instalado ni aceptado. La recepción e instalación de los componentes DI, la carga de resina y la aceptación del sistema RO/DI completo siguen pendientes. Véase el [registro de recepción](../04_operaciones/2026/09/2026-09-24-recepcion-equipo-ro6cb/README.md).

La configuración integrada combina:

- Una envolvente física AIO con display y compartimento técnico lateral
- Un aquascape organizado mediante masas rocosas, islas, playa, canal y espacio negativo
- Una circulación con retorno integrado y bomba de movimiento independiente
- Una luminaria LED de amplio espectro con zonificación posterior mediante PPFD
- Una comunidad prevista de peces, corales, coraliformes e invertebrados compatibles
- Una química que se comprobará mediante parámetros, relaciones y tendencias
- Un procesamiento basado en superficies colonizadas, exportación orgánica mediante skimmer y retirada física de materia, bajo las condiciones proporcionadas por la circulación

La explicación general de cada línea pertenece al [modelo de dimensiones](../01_verilpedia/01_dimensiones/README.md) y a sus fichas correspondientes. Este documento solo reúne cómo se conectan en la configuración de Veril.

## Matriz de implementación

| Dimensión | Decisión concreta en Veril | Documento propietario | Comprobación principal |
| --- | --- | --- | --- |
| Infraestructura | AIO lateral de pequeño volumen, con display, compartimento técnico, retorno y margen de seguridad | [Infraestructura](01_dimensiones/01_infraestructura.md), [dimensión de infraestructura](../01_verilpedia/01_dimensiones/01_infraestructura.md) y documentación de la urna | Integridad, niveles, parada, reinicio, acceso y mantenimiento |
| Espacial | Masa principal posterior derecha, masa secundaria, islas, playa, canal y espacio negativo funcional | [Espacial](01_dimensiones/02_espacial.md) y [dimensión espacial](../01_verilpedia/01_dimensiones/02_espacial.md) | Estabilidad, accesibilidad, rutas libres y reserva de crecimiento |
| Hidráulica | [Mantis Tourbon 60](../01_verilpedia/04_hardware/mantis-tourbon-60/mantis-tourbon-60.md) instalada como bomba de movimiento, con ajuste actual documentado, y [Sicce Micra Plus 600](../01_verilpedia/04_hardware/sicce-micra-plus-600/sicce-micra-plus-600.md) para retorno, integradas sobre las rutas de renovación del aquascape | [Hidráulica](01_dimensiones/03_hidraulica.md) y [técnica de la urna](../01_verilpedia/04_hardware/urna/tecnica.md) | Renovación, distribución, transporte, reinicio y acumulaciones |
| Iluminación | [AI Prime 16HD Reef](../01_verilpedia/04_hardware/ai-prime-16hd-reef/ai-prime-16hd-reef.md), pendiente de disponibilidad, prevista suspendida y con *shade*, cuyo mapa se medirá con [DanoPlus DP-414](../01_verilpedia/04_hardware/danoplus-dp-414/danoplus-dp-414.md) | [Iluminación](01_dimensiones/04_iluminacion.md) | Cobertura, gradientes, sombras, mapa de PPFD y compatibilidad con las zonas |
| Biológica | Configuración mixta con incorporación progresiva y evaluación de compatibilidad y crecimiento | [Biología](01_dimensiones/06_biologia.md) y fichas específicas de organismos | Respuesta observable, capacidad compartida, contención y mantenimiento |
| Química | Seguimiento de composición y estabilidad mediante parámetros, relaciones y tendencias; 25–26 °C preferida y 24,5–26,5 °C como objetivo operativo normal | [Química](01_dimensiones/05_quimica.md) y [fichas de parámetros](../01_verilpedia/03_parametros/README.md) | Método de medición, tendencias, relaciones, estabilidad y respuesta térmica |
| Procesamiento | Método Berlín como referencia: superficies colonizadas, skimmer y retirada física, bajo las condiciones hidráulicas del sistema | [Procesamiento](01_dimensiones/07_procesamiento.md), [dimensión de procesamiento](../01_verilpedia/01_dimensiones/07_procesamiento.md) y [ficha del skimmer Sicce Shark 300](../01_verilpedia/04_hardware/sicce-shark-skimmer-300/sicce-shark-skimmer-300.md) | Capacidad demostrada, exportación, acumulaciones y continuidad del mantenimiento |

## Dependencias de diseño

Las decisiones no se ejecutan como una secuencia independiente. Cada una establece condiciones para las demás:

1. La infraestructura limita el volumen, el acceso, los niveles y la seguridad
2. La roca y el sustrato distribuyen estructura, espacio negativo, playas, canales y superficies
3. La hidráulica debe comprobar que esas formas permiten renovación y transporte suficientes
4. La iluminación debe medirse sobre la geometría real y no solo sobre la posición de la luminaria
5. La biología se incorporará según las zonas, el espacio, el crecimiento, el flujo, la luz y la capacidad demostrada
6. La química se interpretará junto con las entradas, los consumos, el procesamiento y el mantenimiento
7. El procesamiento debe demostrar que puede transformar y retirar la materia introducida bajo las condiciones resultantes

Este orden sirve para identificar dependencias, no para imponer un procedimiento único. Una modificación en una dimensión puede exigir revisar las demás.

## Criterios de aceptación integrados

La configuración no se considerará cerrada por la mera instalación de los componentes. Deberá comprobarse conjuntamente:

- La estabilidad física de la urna, la roca, el sustrato y los elementos técnicos
- La recepción del volumen de retrosifonado y el reinicio seguro del retorno
- La renovación del agua alrededor, debajo y detrás de la estructura
- La ausencia de acumulaciones persistentes que no puedan localizarse o retirarse
- La cobertura lumínica y el mapa de PPFD de las zonas funcionales
- La compatibilidad entre las primeras incorporaciones y las condiciones reales del sistema
- La estabilidad química durante el ciclado, la maduración y las incorporaciones
- La capacidad de procesamiento y exportación frente a las entradas reales
- El acceso suficiente para observar, medir, limpiar, ajustar y retirar elementos
- La conservación de margen operativo frente a evaporación, crecimiento, suciedad y perturbaciones previsibles

Estos criterios se demostrarán mediante observaciones, mediciones y pruebas en los documentos propietarios. El ciclado y la maduración mantienen sus protocolos separados y utilizarán estos criterios cuando corresponda. Mientras no se hayan realizado, se consideran pendientes.

## Estado de implementación

La configuración reúne decisiones de diseño y pendientes de validación. En particular, deben quedar registrados antes de dar por cerrada la implementación:

- El montaje final y la estabilidad de las masas de roca
- La profundidad y distribución real del sustrato
- La respuesta hidráulica con la composición instalada
- La prueba de parada, retrosifonado y reinicio
- El mapa reproducible de PPFD
- La selección y posición de los primeros organismos
- Las tendencias químicas de referencia
- La respuesta del procesamiento durante el ciclado documentado en `03_pendientes/ciclado/`

Una decisión prevista no debe redactarse como una propiedad demostrada. El estado de cada comprobación se actualizará en su documento propietario o en el plan operativo que corresponda.

## Régimen térmico adoptado

La lógica vigente del controlador del Rowenta y sus guardarraíles se documentan
en [Control térmico de Veril](control-termico.md). Las mediciones y actuaciones
fechadas se conservan en el [registro de puesta en servicio y mediciones del
27 de septiembre](../04_operaciones/2026/09/2026-09-27-puesta-en-servicio-control-termico.md).

El agua de Veril tiene como zona preferida **25–26 °C**, con 25 °C como centro orientativo y no como consigna puntual. El régimen operativo normal/óptimo es **24,5–26,5 °C**. Entre **24,0 y 24,5 °C** se considera una banda fresca todavía razonablemente normal; **23,0–24,0 °C** es una excursión fría que no implica peligro agudo por sí sola, pero cuya persistencia debe investigarse. Por debajo de **23,0 °C** el agua queda fuera del objetivo operativo y por debajo de **22,0 °C** se establece una prioridad local de revisión. Estos son criterios de gestión de Veril, no umbrales fisiológicos universales; **22 °C no es un umbral publicado de daño**. Los intervalos altos conservan la clasificación vigente y se interpretan junto con duración y tendencia.

| Estado | Temperatura del agua | Interpretación operativa |
| --- | --- | --- |
| Prioridad fría | **<22,0 °C** | Escalón local de revisión prioritaria; no es un umbral científico de lesión. Verificar enseguida la lectura y el termómetro independiente, y valorar duración, tendencia y fauna. No hay calefacción automática instalada. |
| Por debajo del objetivo | **22,0–23,0 °C** | Fuera del objetivo operativo. Confirmar telemetría y medición; si persiste, investigar y corregir gradualmente cuando exista una solución de calefacción validada. No equivale por sí solo a daño demostrado. |
| Excursión fría | **23,0–24,0 °C** | Excursión tolerable según la evidencia disponible, pero no se adopta como régimen normal; investigar si persiste. La caída de rendimiento fisiológico de peces observada en experimentos no equivale a lesión aguda en el acuario. |
| Fresca | **24,0–24,5 °C** | Banda baja razonablemente normal, aunque inferior al óptimo; observar estabilidad y tendencia, sin exigir corrección inmediata por una lectura aislada. |
| Óptima baja | **24,5–25,0 °C** | Zona óptima; no requiere refrigeración. |
| Preferida | **25,0–26,0 °C** | Zona que se procura mantener la mayor parte del tiempo. 25 °C es referencia central, no una consigna exacta. |
| Óptima alta | **26,0–26,5 °C** | Dentro del rango óptimo; no refrigerar solo por cruzar 26 °C. |
| Cálida | **26,5–27,0 °C** | Aceptable; interpretar duración y tendencia. |
| Cálida estival | **27,0–27,5 °C** | Aceptable temporalmente; no equivale por sí sola a alarma. |
| Alta / transición | **27,5–28,0 °C** | Fin del rango aceptable; procurar que deje de subir, interpretando duración y tendencia. |
| Protección | **28,0–28,5 °C** | Buscar que la temperatura deje de subir y disminuya. |
| Alerta | **28,5–29,0 °C** | Aviso al propietario y comprobación de lectura, duración, tendencia y refrigeración. |
| Crítica | **29,0–30,0 °C** | Situación no aceptable como operación normal; priorizar recuperar margen térmico. |
| Emergencia | **≥30,0 °C** | Episodio excepcional que requiere respuesta prioritaria. |

La envolvente y sus bandas se adoptan como decisión específica para Veril. No afirman que el límite de una banda sea un umbral universal de lesión o blanqueamiento. La temperatura, duración y tendencia se interpretan por separado. El clima de Santa Cruz de Tenerife contribuye a la carga ambiental, pero no determina por sí solo la temperatura del agua: las normales de AEMET de la estación C449C reflejan máximas medias diarias de 28,7 °C en julio, 29,0 °C en agosto y 28,1 °C en septiembre. [AEMET: valores climatológicos normales de Santa Cruz de Tenerife](https://www.aemet.es/es/serviciosclimaticos/datosclimatologicos/valoresclimatologicos?k=coo&l=C449C)

El plan térmico tiene actualmente automatización de refrigeración, pero no una alarma ni control automático para temperaturas bajas. Los límites de **23 y 22 °C** son escalones operativos locales: el primero marca estar por debajo del objetivo; el segundo, prioridad de revisión. Ninguno afirma un umbral universal de lesión. Ante valores inferiores a 23 °C se comprobará primero la frescura de `off-sns-05` y se contrastará con una medición independiente; a menos de 22 °C la verificación será prioritaria. Antes de adquirir o configurar un calentador se revisarán los mínimos de la fauna elegida y el mínimo estacional real del agua.

Como referencia general —no como requisito de todas las especies—, Tropical Marine Centre indica 23–26 °C para corales y señala que existen diferencias entre especies. La investigación experimental también documenta respuestas de estrés por frío en corales, pero los resultados dependen de especie, aclimatación, magnitud y duración; no permiten trasladar un umbral experimental directamente a Veril ([guía de cuidado de corales de TMC](https://www.tropicalmarinecentre.com/en/downloads/files/care_sheets/Corals/Corals.pdf), [Helgoe et al., 2024](https://doi.org/10.1111/brv.13042)).

Antes de comprar o conectar un calentador se definirán sus requisitos de temperatura con la fauna seleccionada; se contrastará el termostato integrado con un termómetro independiente y se preverá una protección independiente frente a sobrecalentamiento. La lógica deberá coordinar calefacción con el Rowenta mediante una zona muerta que evite órdenes opuestas. Potencia, ubicación, histéresis, alarmas y respuesta ante pérdida de telemetría siguen pendientes y no se implementan mientras no haya calentador.

Las normales ambientales no demuestran por sí mismas la temperatura del acuario. La relación concreta entre ambos sistemas requiere contrastar los históricos de Home Assistant, las órdenes del climatizador y las lecturas del agua.

La telemetría de temperatura del agua procede de `off-sns-05`, con la sonda sumergida en la cámara Skimmer. Es una lectura del agua del sistema, no una comprobación metrológica independiente; la ubicación y las observaciones fechadas constan en los [registros del 20 y 23 de septiembre](../04_operaciones/2026/09/2026-09-20-medicion-manual-salinidad-y-quimica.md) y en la [revisión del 24 de septiembre](../04_operaciones/2026/09/2026-09-24-revision-observacion-control-termico.md).

El objetivo biológico no determina por sí solo los umbrales ni la lógica de Home Assistant. El 27 de septiembre de 2026 se instaló y habilitó como piloto un único controlador térmico con la envolvente adoptada, sensores ambientales, previsión horaria y protección ante pérdida de telemetría. En la consulta de las 17:11 WEST, Home Assistant mostró 28,8 °C en `off-sns-05`, antigüedad de comunicación de 0 min y estado `protection`; el propietario confirmó físicamente el Rowenta encendido en frío, a 24 °C y con ventilador alto. La sesión quedó sincronizada y transferida al control automático. Al salir de `protection`, el piloto baja la consigna a 25 °C si el agua permanece por debajo de 27,5 °C durante 15 min, y apaga al permanecer en 26,5 °C o menos durante 15 min. Estos umbrales son lógica de control, no cambios a la envolvente biológica ni evidencia de eficacia térmica. La configuración y sus límites se describen en el [registro de puesta en servicio del 27 de septiembre](../04_operaciones/2026/09/2026-09-27-puesta-en-servicio-control-termico.md); la [revisión del 24 de septiembre](../04_operaciones/2026/09/2026-09-24-revision-observacion-control-termico.md) conserva el estado histórico de aquella fecha.

Este régimen es vinculante como criterio de compatibilidad para las decisiones posteriores de Veril:

- La población futura se seleccionará para que su mantenimiento habitual sea compatible con la zona preferida 25–26 °C y el objetivo operativo normal 24,5–26,5 °C; una especie con mínimo publicado superior podrá estrechar el extremo frío. Las excursiones 23–24 °C no se consideran régimen normal y por debajo de 23 °C se está fuera del objetivo. No se añadirá fauna mientras el agua esté en alerta.
- Las recetas, la preparación de agua y los cambios de agua deberán evitar saltos térmicos innecesarios y ser compatibles con esta envolvente. No se modifica con ello ninguna receta ni dosis ya adoptada; su validación térmica se hará en su documento operativo antes de ejecutarla.
- La iluminación, bombas, ventilación y refrigeración ambiental se evaluarán por su contribución al balance térmico, no por una lectura aislada.
- Cualquier ficha o plan posterior que proponga un requisito incompatible deberá revisarse expresamente; este régimen no presupone que una especie, una receta o un equipo ya cumplan el criterio sin evidencia propia.

La dimensión química conserva la interpretación de la temperatura como variable de estado y contexto de medición. La infraestructura documenta la capacidad física de calentamiento y disipación, la hidráulica su distribución y homogeneización, y la dimensión biológica su compatibilidad con la comunidad prevista.

## Documentos relacionados

- [Índice de dimensiones](../01_verilpedia/01_dimensiones/README.md)
- [Plan de ciclado](../03_pendientes/ciclado/plan.md)
- [Plan de maduración](../03_pendientes/maduracion/plan.md)
- [Parámetros del agua](../01_verilpedia/03_parametros/README.md)
