RicardoJBarrios/acuario-veril/04_operaciones/README.md

# Operaciones de Veril

Este directorio es el diario verificable del acuario. Cada entrada registra algo que ocurrió, con su fecha, alcance, resultado, incidencias, evidencia disponible y pendientes derivados.

## Diferencia respecto a las actuaciones pendientes

| Documento | Pregunta que responde | Puede acreditar una ejecución |
| --- | --- | --- |
| [Pendientes](../03_pendientes/README.md) | Qué se pretende hacer y bajo qué condiciones | No |
| Operación | Qué se hizo, cuándo y con qué resultado | Sí, dentro de los límites de su evidencia |
| [Configuración](../02_configuracion/README.md) | Cuál es el estado vigente del acuario | Solo mediante el enlace a la operación que la estableció o comprobó |
| [Verilpedia](../01_verilpedia/README.md) | Qué conocimiento general se utiliza | No |

## Cronología

### Septiembre de 2026

- [4 de septiembre: Inventario, plantilla y pruebas de composición del hardscape](2026/09/2026-09-04-inventario-y-pruebas-hardscape.md)
- [5 de septiembre: Montaje, fijación del hardscape y primer llenado](2026/09/2026-09-05-montaje-y-primer-llenado/README.md)
- [6 de septiembre: Ajuste de nivel, restablecimiento del retorno y colocación del sensor](2026/09/2026-09-06-ajuste-nivel-retorno-y-sensor.md)
- [13 de septiembre: Comprobación de salinidad con refractómetro](2026/09/2026-09-13-comprobacion-salinidad-refractometro.md)
- [13 de septiembre: Reposición manual y observación del nivel](2026/09/2026-09-13-reposicion-manual-y-observacion-nivel.md)
- [13 de septiembre: Observación de cambio de color del hardscape](2026/09/2026-09-13-observacion-cambio-color-hardscape/README.md)
- [17 de septiembre: Observaciones de flujo, temperatura y sustrato](2026/09/2026-09-17-observaciones-flujo-temperatura-y-sustrato.md)
- [17 de septiembre: Automatización de la refrigeración preventiva del despacho](2026/09/2026-09-17-automatizacion-refrigeracion-preventiva.md)
- [18 de septiembre: Ajuste de la Mantis Tourbon 60 al 50 %](2026/09/2026-09-18-ajuste-mantis-tourbon-50.md)
- [20 de septiembre: Medición manual de salinidad y química inicial](2026/09/2026-09-20-medicion-manual-salinidad-y-quimica.md)
- [22 de septiembre: Ajuste de la refrigeración preventiva para mantener el agua bajo 27 °C](2026/09/2026-09-22-ajuste-refrigeracion-preventiva-bajo-27.md)
- [23 de septiembre: Ajuste del control térmico del agua](2026/09/2026-09-23-ajuste-control-termico-agua.md)
- [23 de septiembre: Pesaje y medición del desplazamiento del hardscape](2026/09/2026-09-23-pesaje-y-desplazamiento-del-hardscape.md)
- [24 de septiembre: Revisión y preparación del control térmico](2026/09/2026-09-24-revision-observacion-control-termico.md)
- [24 de septiembre: Recepción comunicada del equipo RO6CB](2026/09/2026-09-24-recepcion-equipo-ro6cb/README.md)
- [26 de septiembre: Reposición manual y lectura de salinidad](2026/09/2026-09-26-reposicion-manual-y-lectura-de-salinidad.md)
- [27 de septiembre: Prueba del DanoPlus, PAR ambiental y nivel de C3](2026/09/2026-09-27-prueba-danoplus-nivel-c3-y-par.md)
- [27 de septiembre: Puesta en servicio del control térmico inicial y mediciones disponibles](2026/09/2026-09-27-puesta-en-servicio-control-termico.md)
- [28 de septiembre: Vaciado del remanente del barril y nivel de C3](2026/09/2026-09-28-vaciado-remanente-barril-y-nivel-c3.md)
- [29 de septiembre: Ajuste de la protección del enchufe del retorno](2026/09/2026-09-29-ajuste-proteccion-enchufe-retorno.md)
- [29 de septiembre: Revisión del extremo frío y actualización del panel térmico](2026/09/2026-09-29-revision-frio-y-gauge-termico.md)

> [!NOTE]
> La cronología empieza en las actuaciones para las que el repositorio conserva una fecha y evidencia suficientes. La ausencia de una entrada anterior no demuestra que no hubiera otras actuaciones.
