RicardoJBarrios/acuario-veril/03_pendientes/README.md

# Actuaciones pendientes de Veril

Este directorio contiene decisiones y actuaciones todavía no ejecutadas. Un documento pendiente define objetivos, condiciones de entrada, pasos, criterios de aceptación y respuesta ante desviaciones, pero no demuestra que la actuación haya ocurrido.

## Actuaciones pendientes

- [Ciclado](ciclado/README.md): Fase previa, receta, prueba nitrificante y criterios de cierre
- [Maduración](maduracion/README.md): Evolución biológica posterior al ciclado e incorporaciones graduales
- [Observación biológica de corales](maduracion/plan-indicadores-visuales-corales.md): propuesta pendiente para usar cambios visibles como avisos de medición, no como diagnósticos
- [Operación recurrente](operacion-recurrente/README.md): Procedimientos previstos de mantenimiento, observación y respuesta
- [Plan transversal de medición y tests](operacion-recurrente/medicion-y-tests.md): criterios de medida y alternativas aplicables a todas las fases
- [Diseños 3D](disenos-3d/README.md): modelos y archivos de fabricación cuya validación física sigue pendiente

Las ejecuciones reales, incluidas las que aplican estos documentos, se registran en [Operaciones](../04_operaciones/README.md).
