RicardoJBarrios/acuario-veril/05_multimedia/README.md

# Multimedia de Veril

Este directorio conserva recursos visuales complementarios. Un archivo visual
solo acredita lo que permite observar y no sustituye las mediciones ni los
registros de operación.

## Recursos

- [Composición del acuario, archivo fechado en su nombre como 6 de septiembre de 2026](2026-09-06-composicion-acuario.png)

El origen y el método de creación de esta imagen no están documentados. Debe
tratarse como referencia visual, no como prueba independiente de dimensiones,
estabilidad o estado físico de Veril. Las fotografías del hardscape instalado y
su descripción están en la [operación de montaje](../04_operaciones/2026/09/2026-09-05-montaje-y-primer-llenado/README.md).
