RicardoJBarrios/acuario-veril/06_Logo/README.md

# Identidad gráfica de Veril

## Definición

El logotipo de Veril es la identificación gráfica del proyecto. Está compuesto por un isotipo, el nombre **VERIL** y el descriptor **NANO REEF**.

## Significado del nombre

En el léxico canario, *veril* designa un desnivel rocoso y pronunciado del fondo marino, de la costa o de un risco. En el contexto marino, el término alude especialmente al borde o caída donde cambia de forma marcada la profundidad y la estructura del fondo. Esta acepción está recogida por la [Academia Canaria de la Lengua](https://www.academiacanarialengua.org/diccionario/entrada/veril/).

El nombre se utiliza para evocar un límite de transición entre relieves, profundidades y condiciones ambientales. No pretende afirmar que el acuario reproduzca literalmente un veril natural; funciona como una referencia conceptual a la relación entre estructura, agua, profundidad y vida marina que articula el proyecto.

## Descripción del logotipo

El isotipo reúne tres trazos horizontales paralelos, de longitud y posición escalonadas, que se curvan y descienden antes de prolongarse hacia la derecha. Su forma evoca capas, relieve submarino y circulación de agua sin representar una especie, un coral ni un componente concreto del acuario.

El nombre **VERIL** se presenta en mayúsculas con una composición geométrica y abierta. **NANO REEF** funciona como descriptor del proyecto y sitúa el logotipo en el contexto de un acuario de arrecife de pequeño volumen; no constituye una denominación taxonómica ni define por sí solo la configuración o la arquitectura del sistema.

## Esquema de color

La paleta cromática principal está formada por tres colores que se aplican como una transición progresiva en el isotipo y, cuando corresponde, en el descriptor:

| Color | Valor HEX | Uso principal |
| --- | --- | --- |
| Azul Veril | `#2f82f9` | Inicio de la transición cromática y elementos de referencia acuática |
| Violeta Veril | `#6952d8` | Zona intermedia de la transición y conexión visual entre los extremos |
| Coral Veril | `#e1565b` | Extremo cálido de la transición y acento cromático |

Las versiones monocromas utilizan negro (`#000000`) sobre fondos claros o blanco (`#ffffff`) sobre fondos oscuros. Estos valores describen la paleta de referencia; el resultado visual puede variar según el perfil de color, el soporte y el método de reproducción.

## Recursos vigentes

- [Logotipo principal editable](logotipo.svg)
- [Diseño PNG](diseño.png)
- [Exportaciones PNG](png/): variantes derivadas de las páginas de `logotipo.svg`, a 192 ppp y sin la geometría de construcción.
- [Logotipo utilizado en portada](png/imagotipo-vertical-con-descriptor-negativo-color.png)

### Variantes PNG

Las variantes se nombran por construcción, orientación, polaridad y tratamiento cromático. **Positivo** significa motivo oscuro sobre fondo claro o transparente; **negativo**, motivo claro sobre fondo oscuro. **Monocromo** se limita a negro o blanco y **color** aplica la paleta de Veril.

| Construcción | Variantes disponibles |
| --- | --- |
| Isotipo | [Positivo monocromo](png/isotipo-positivo-monocromo.png), [positivo color](png/isotipo-positivo-color.png), [negativo monocromo](png/isotipo-negativo-monocromo.png) y [negativo color](png/isotipo-negativo-color.png) |
| Logotipo | [Positivo monocromo](png/logotipo-positivo-monocromo.png) y [negativo monocromo](png/logotipo-negativo-monocromo.png) |
| Logotipo con descriptor | [Positivo monocromo](png/logotipo-con-descriptor-positivo-monocromo.png), [positivo color](png/logotipo-con-descriptor-positivo-color.png), [negativo monocromo](png/logotipo-con-descriptor-negativo-monocromo.png) y [negativo color](png/logotipo-con-descriptor-negativo-color.png) |
| Imagotipo vertical | [Positivo monocromo](png/imagotipo-vertical-positivo-monocromo.png), [positivo color](png/imagotipo-vertical-positivo-color.png), [negativo monocromo](png/imagotipo-vertical-negativo-monocromo.png) y [negativo color](png/imagotipo-vertical-negativo-color.png) |
| Imagotipo vertical con descriptor | [Positivo monocromo](png/imagotipo-vertical-con-descriptor-positivo-monocromo.png), [positivo color](png/imagotipo-vertical-con-descriptor-positivo-color.png), [negativo monocromo](png/imagotipo-vertical-con-descriptor-negativo-monocromo.png) y [negativo color](png/imagotipo-vertical-con-descriptor-negativo-color.png) |
| Imagotipo horizontal con descriptor | [Positivo monocromo](png/imagotipo-horizontal-con-descriptor-positivo-monocromo.png), [positivo color](png/imagotipo-horizontal-con-descriptor-positivo-color.png), [negativo monocromo](png/imagotipo-horizontal-con-descriptor-negativo-monocromo.png) y [negativo color](png/imagotipo-horizontal-con-descriptor-negativo-color.png) |

## Alcance

Esta ficha documenta la identidad gráfica de Veril. No define la configuración del acuario, sus dimensiones, su arquitectura técnica ni sus decisiones biológicas.
