RicardoJBarrios/acuario-veril/01_verilpedia/README.md

# Verilpedia

> [!WARNING]
> Verilpedia documenta lo que una persona sin formación experta ha recopilado e interpretado para orientarse en el proyecto. Debe leerse como material de trabajo personal, no como autoridad técnica.

Este directorio es una compilación personal de datos e ideas que he investigado en distintas fuentes porque pueden ser útiles para Veril. No es una enciclopedia formal, una revisión experta, una fuente normativa ni una fuente de verdad. Su contenido puede contener errores, simplificaciones, interpretaciones incompletas o afirmaciones pendientes de contraste.

Las referencias incluidas en las fichas permiten rastrear parte de la investigación, pero no convierten a Verilpedia en la fuente original ni validan por sí solas sus conclusiones. Antes de tomar una decisión se debe volver a la fuente primaria o competente correspondiente, comprobar la evidencia disponible y contrastarla con la configuración y las mediciones reales de Veril.

Verilpedia no registra operaciones ejecutadas ni convierte las decisiones de este acuario en reglas generales.

Las aplicaciones concretas se documentan en la [configuración](../02_configuracion/README.md), las actuaciones pendientes en [Pendientes](../03_pendientes/README.md) y los hechos ejecutados en [Operaciones](../04_operaciones/README.md).

El orden numérico de las categorías propone un recorrido desde el modelo del sistema hasta sus elementos, parámetros y procesos. No implica que todas las fichas deban leerse de forma lineal.

## Índice

- [Dimensiones arquitectónicas](01_dimensiones/README.md): procesamiento, biología, infraestructura, espacio, hidráulica, iluminación y química del sistema
- [Biología](02_biologia/README.md): microorganismos, microfauna, algas, cnidarios, peces e invertebrados
- [Parámetros](03_parametros/README.md): parámetros del agua marina
- [Hardware](04_hardware/README.md): urna, equipos, sensores e integraciones
- [Productos](05_productos/README.md): productos documentados
- [Procesos](06_procesos/README.md): ciclado, maduración y operación
- [Historia](07_historia/README.md): origen y evolución de métodos y conceptos relevantes
- [Prácticas](08_practicas/README.md): mantenimiento, estación auxiliar, cuarentena y supervisión
