RicardoJBarrios/acuario-veril/03_pendientes/disenos-3d/README.md

# Diseños 3D pendientes de validación

Este apartado conserva modelos y archivos de fabricación preparados para
Veril. La disponibilidad de un diseño no significa que esté instalado ni que
su función se haya validado en el acuario.

## Diseños

- [Diseños de cestas BactoFlex Mini](bactoflex-mini/README.md): dos versiones
  paramétricas organizadas en carpetas separadas, con sus planes y derivados
  identificados por versión; la modular aún requiere fabricación y pruebas
  físicas.
