RicardoJBarrios/acuario-veril/01_verilpedia/05_productos/README.md

# Productos documentados

Estas fichas son una recopilación personal de información sobre productos utilizados o considerados en el arranque y el mantenimiento del sistema. No son documentación oficial completa, no constituyen una selección de compra ni sustituyen la etiqueta o las instrucciones vigentes del fabricante.

## Índice

- [01 — Aquaforest AF Bio Sand](01_af-bio-sand/af-bio-sand.md)
- [02 — Aquaforest Reef Salt](02_aquaforest-reef-salt/aquaforest-reef-salt.md)
- [03 — AF Stone Fix](03_af-stone-fix/af-stone-fix.md)
- [04 — Cianoacrilato Cofan en gel de alta viscosidad](04_cofan-cianocrilato-gel/cofan-cianocrilato-gel.md)
- [05 — D-D Aquascape Construction Epoxy Coralline Algae](05_dd-aquascape-construction-epoxy/dd-aquascape-construction-epoxy.md)
- [06 — D-D The Aquarium Solution AQPR001](06_dd-aquarium-solution-aqpr001/dd-aquarium-solution-aqpr001.md)
- [07 — Eheim 4005843](07_eheim-4005843/eheim-4005843.md)
- [08 — Fritz Fishless Fuel](08_fritz-fishless-fuel/fritz-fishless-fuel.md)
- [09 — FritzZyme 9 Saltwater](09_fritzzyme-9/fritzzyme-9.md)
- [10 — FritzZyme TurboStart 900 Saltwater](10_fritzzyme-turbostart-900/fritzzyme-turbostart-900.md)
- [11 — D-D Marco Coralline Rock](11_dd-marco-coralline-rock/dd-marco-coralline-rock.md)
- [12 — Salifert Ammonia NH3 Profi Test](12_salifert-ammonia-nh3/salifert-ammonia-nh3.md)
- [13 — Salifert NO2 Profi Test](13_salifert-no2/salifert-no2.md)
- [14 — Tetra Test 7 en 1](14_tetra-test-7-en-1/tetra-test-7-en-1.md)
- [15 — Salifert Nitrate Profi Test](15_salifert-nitrate/salifert-nitrate.md)
- [16 — Salifert Phosphate Profi Test](16_salifert-phosphate/salifert-phosphate.md)
- [17 — Salifert KH/Alk Profi Test](17_salifert-kh-alk/salifert-kh-alk.md)
- [18 — Salifert pH Profi Test](18_salifert-ph/salifert-ph.md)
- [19 — Salifert Calcium Profi Test](19_salifert-calcium/salifert-calcium.md)
- [20 — Salifert Magnesium Profi Test](20_salifert-magnesium/salifert-magnesium.md)
- [21 — Hanna HI774 Marine Phosphate ULR Checker](21_hanna-hi774/hanna-hi774.md)
- [22 — TRITON ICP-OES](22_triton-icp-oes/triton-icp-oes.md)

## Criterio común

Un producto de arranque no demuestra por sí mismo que un sistema pueda procesar una carga determinada. La capacidad debe verificarse con mediciones y una carga conocida, siguiendo una sola receta coherente.

Las dosis, formatos y condiciones de conservación pueden cambiar. La etiqueta del envase adquirido y la documentación vigente del fabricante prevalecen sobre cualquier resumen.

## Documentación técnica local

Los manuales y fichas técnicas descargados se conservan dentro del directorio de cada producto, junto a su ficha correspondiente.

## Fuentes metodológicas locales

- [Método de Dr. Tim Hovanec](../06_procesos/08_metodo-dr-tim.md)
- [Sistema de arranque de Aquaforest](../06_procesos/07_metodo-aquaforest.md)
- [Método de Fritz Aquatics](../06_procesos/09_metodo-fritz.md)
