RicardoJBarrios/acuario-veril/03_pendientes/maduracion/README.md

# Maduración de Veril

## Propósito

Esta carpeta documenta la fase posterior al ciclado, durante la que se observa el desarrollo de la comunidad biológica, la sucesión, la estabilidad del sistema y la respuesta a incorporaciones graduales.

La explicación general del proceso está en la [ficha de maduración](../../01_verilpedia/06_procesos/03_maduracion.md) y el protocolo específico de Veril está en el [plan de maduración](plan.md).

La maduración no tiene una duración fija ni constituye una segunda prueba de ciclado. Se avanza mediante condiciones observables, ventanas de seguimiento y decisiones registradas.

Los módulos específicos de incorporación y observación se documentan dentro de esta fase: [plan de incorporación de microfauna](plan-microfauna.md) y [plan de observación biológica de corales](plan-indicadores-visuales-corales.md).
