RicardoJBarrios/acuario-veril/01_verilpedia/02_biologia/README.md

# Biología del acuario marino

Estas fichas reúnen, como compilación personal de investigación, organismos y procesos biológicos que pueden ser relevantes para el funcionamiento y la maduración de un acuario marino. No son una fuente formal ni sustituyen la consulta de fuentes competentes. Las decisiones de incorporación específicas se documentan en la [implementación de Veril](../../02_configuracion/README.md) o en el plan operativo correspondiente.

## Índice general

- [Microorganismos y microfauna marina](01_microorganismos/README.md)
- [Algas](02_algas/README.md)
- [Cnidarios sésiles](03_cnidarios-sesiles/README.md)
- [Peces](04_peces/README.md)
- [Invertebrados](05_invertebrados/README.md)
- [Diagnóstico y bioseguridad](../08_practicas/04_diagnostico-y-bioseguridad/README.md): identificación prudente, plagas, síntomas y entradas de corales
- Las fichas de corales, peces, macroalgas e invertebrados se organizan dentro de sus categorías biológicas. Su aplicación concreta a Veril se enlaza desde la [biología del proyecto](../../02_configuracion/03_biologia/README.md), los [criterios de corales](../../02_configuracion/03_biologia/01_criterios/01_corales.md), los [criterios de fauna](../../02_configuracion/03_biologia/01_criterios/02_fauna.md) y los planes correspondientes

Estas categorías organizan las fichas por grupos biológicos y responsabilidad documental. Que una ficha se haya estudiado para Veril no la convierte en una categoría distinta: la identidad, biología, necesidades y riesgos del organismo permanecen aquí; su selección, estado, orden y aceptación pertenecen a los documentos del proyecto y a los planes. No se convierten «equipo de limpieza» u «organismos beneficiosos» en categorías biológicas.

Las fichas individuales de mantenimiento de cnidarios, peces, invertebrados y
algas usan obligatoriamente la matriz común de [parámetros de mantenimiento
medibles](plantilla-ficha-organismo.md). Sus tablas distinguen valores
publicados para la especie, referencias generales de grupo, criterios de
compatibilidad de Veril y datos aún no cuantificados. Una laguna de evidencia
no es un valor objetivo implícito.
