RicardoJBarrios/acuario-veril/01_verilpedia/06_procesos/README.md

# Procesos del acuario marino

Estas fichas son una compilación personal de investigación sobre procesos de establecimiento, evolución y funcionamiento de un acuario marino. No constituyen protocolos validados ni sustituyen a los planes específicos de Veril o a las fuentes competentes.

## Índice

- [Ciclado biológico](01_ciclado.md)
- [Variante de ciclado sin peces](02_ciclado-sin-peces.md)
- [Método de Aquaforest](07_metodo-aquaforest.md)
- [Método oficial de ciclado sin peces de Dr. Tim Hovanec](08_metodo-dr-tim.md)
- [Método de Fritz Aquatics para ciclado marino sin peces](09_metodo-fritz.md)
- [Maduración](03_maduracion.md)
- [Ugly phase](04_ugly-phase.md)
- [Operación y mantenimiento](05_operacion.md)
- [Cambios de agua](06_cambios-agua.md)
- [Análisis ICP de agua marina](10_analisis-icp.md)
