RicardoJBarrios/acuario-veril/01_verilpedia/08_practicas/README.md

# Prácticas de acuario

Esta sección reúne, como compilación personal de investigación, prácticas generales relacionadas con el mantenimiento y la supervisión de un acuario marino. No constituye una guía experta ni una validación de seguridad. Describe objetivos, límites y criterios reutilizables; las decisiones del acuario pertenecen a la [configuración](../../02_configuracion/README.md), los procedimientos pendientes a [Pendientes](../../03_pendientes/README.md) y cada ejecución a [Operaciones](../../04_operaciones/README.md).

## Contenido

- [Estación auxiliar](01_estacion-auxiliar.md): Separación física para preparación de agua, observación, cuarentena y hospital
- [Cuarentena y hospital](02_cuarentena-y-hospital.md): Bioseguridad, observación, tratamiento y criterios de alta
- [Supervisión y automatización](03_supervision-y-automatizacion.md): Monitorización, alarmas, modos y límites de la automatización
- [Diagnóstico y bioseguridad](04_diagnostico-y-bioseguridad/README.md): identificación, plagas, salud de organismos y entradas de corales

El mantenimiento general se desarrolla en la [ficha de operación](../06_procesos/05_operacion.md) y los [cambios de agua](../06_procesos/06_cambios-agua.md).
