RicardoJBarrios/acuario-veril/03_pendientes/ciclado/README.md

# Ciclado de Veril

## Propósito

Este directorio reúne la evidencia metodológica, las decisiones de arranque y el plan específico de ciclado de Veril. La explicación general está en la [ficha de ciclado](../../01_verilpedia/06_procesos/01_ciclado.md) y la fase posterior tiene su propia documentación en [maduración](../maduracion/README.md).

## Estructura

### Fuentes

- [Métodos generales de ciclado en Verilpedia](../../01_verilpedia/06_procesos/README.md)

Estas fuentes describen métodos, resultados y límites de transferencia. No fijan por sí solas la configuración de Veril.

La variante general de ciclado sin peces está documentada en [la ficha de procesos correspondiente](../../01_verilpedia/06_procesos/02_ciclado-sin-peces.md).

### Decisiones

- [Receta combinada Fritz–Aquaforest](decisiones/seleccion-inoculante-y-receta.md)

Este documento fija la receta elegida, sus condiciones, exclusiones y pendientes.

### Plan

- [Plan de ciclado](plan.md): prueba funcional del biofiltro
- [Runbook de ciclado sin peces](runbook.md): ejecución paso a paso, controles y registro
- [Proyección microbiológica del ciclado](proyeccion-microbiologica.md): grupos esperados, incertidumbres y sucesión inicial

La ruta vigente mantiene la roca sin arena durante una fase previa de limpieza y observación. Después se incorpora el AF Bio Sand como sustrato y superficie inicial, se añade FritzZyme 9 y se utiliza Fritz Fishless Fuel como fuente controlada de nitrógeno amoniacal. El ciclado se realizará con agua de mar filtrada con UV de Elite Reef Kanarias. Aquaforest Reef Salt se utilizará después para preparar el agua de los cambios, pero no constituye una inoculación.

## Relación entre las fases

`montaje técnico → ciclado sin peces → maduración → incorporación gradual → operación estable`

El ciclado demuestra una capacidad nitrificante frente a una carga conocida. La maduración posterior observa la estabilidad del sistema, la colonización, la sucesión biológica y la respuesta a incorporaciones pequeñas.

Ninguna lectura aislada, fecha o apariencia visual sustituye la separación entre ambas fases.
