RicardoJBarrios/acuario-veril/01_verilpedia/03_parametros/README.md

# Parámetros del acuario marino

Estas fichas son una compilación personal de investigación sobre los parámetros del agua. Pretenden servir como orientación de trabajo, no como referencia formal o autoridad metrológica. No contienen el protocolo de ciclado ni decisiones específicas de Veril.

## Índice

- [Temperatura](temperatura.md)
- [Salinidad](salinidad.md)
- [pH](ph.md)
- [Sistema carbonato](sistema-carbonato.md)
- [Alcalinidad](alcalinidad.md)
- [Calcio](calcio.md)
- [Magnesio](magnesio.md)
- [Amonio](amonio.md)
- [Nitrito](nitrito.md)
- [Nitrato](nitrato.md)
- [Fosfato](fosfato.md)
- [Oxígeno disuelto](oxigeno.md)

## Estructura común

Cada ficha explica qué es y qué mide el parámetro, qué aporta, qué puede indicar un valor bajo o alto, cómo se mide, qué limitaciones tiene la medición, qué mecanismos pueden modificarlo, qué niveles sirven como referencia, qué variables están relacionadas y qué no demuestra una lectura aislada.

## Cómo leer las fichas

Los niveles normales son rangos orientativos, no objetivos universales. La interpretación debe considerar el tipo de sistema, la fauna, la temperatura, la salinidad, la carga biológica, la alimentación, la exportación y la tendencia temporal.

Una cifra aislada debe confirmarse antes de corregirla. Un cambio brusco puede ser más relevante que una desviación moderada y estable, y dos parámetros pueden parecer correctos por separado mientras su combinación sea problemática.

Las relaciones entre parámetros no son, en general, porcentajes universales. Algunas son químicas y directas, como la fracción NH3 dentro del amonio total o el equilibrio entre calcio, alcalinidad, pH y magnesio. Otras son relaciones ecológicas, como nitrato y fosfato: sirven para interpretar el sistema, pero no justifican perseguir una proporción fija sin conocer sus entradas, consumos y exportación.

La clasificación de estas fichas es funcional y no exclusiva: temperatura, salinidad y oxígeno son condiciones físicas o metrológicas que también condicionan la interpretación química; nitrato participa a la vez en el ciclo del nitrógeno y en la gestión de nutrientes; y el sistema carbonato relaciona pH, alcalinidad, CO₂, calcio, magnesio y estado de saturación.
