RicardoJBarrios/acuario-veril/02_configuracion/02_hardscape/README.md

# Hardscape instalado de Veril

Esta carpeta documenta el hardscape instalado en la urna de Veril, sus vistas de referencia y el inventario fotográfico de las rocas. La ejecución fechada, sus resultados y las comprobaciones pendientes se conservan en [Operaciones](../../04_operaciones/2026/09/2026-09-05-montaje-y-primer-llenado/README.md).

- [Rocas: inventario descriptivo](rocas/README.md)
- [Plantilla de referencia del display y leyenda de marcas](plantilla/README.md)
- [Operación del 5 de septiembre de 2026: montaje, fijación y primer llenado](../../04_operaciones/2026/09/2026-09-05-montaje-y-primer-llenado/README.md)

La carpeta `rocas/` contiene el inventario visual y descriptivo de las diez piezas identificadas.

## Estado operativo actual

La composición fue montada dentro de la urna el **5 de septiembre de 2026**. Durante esa misma operación, las uniones de las rocas se fijaron con **AF Stone Fix**. Por tanto, el hardscape no está únicamente presentado o apilado: se encuentra instalado y fijado, aunque su aceptación mecánica e hidráulica definitiva sigue dependiendo de las comprobaciones indicadas en la operación.

Las fotografías de la operación registran el montaje antes de aplicar el adhesivo y antes de incorporar la cama de arena. Sirven para identificar la geometría y las piezas, pero no deben interpretarse como una prueba de la fijación actual. La cama de arena y la validación completa del conjunto siguen pendientes.

La fijación con AF Stone Fix no sustituye la comprobación de los apoyos, los márgenes respecto a los cristales, el acceso para mantenimiento ni la circulación con el sistema funcionando. El detalle de lo ejecutado y de los resultados observados está en el [registro de la operación](../../04_operaciones/2026/09/2026-09-05-montaje-y-primer-llenado/README.md).

La mejora es óptica y no generativa: no recupera información que no estuviera en la fotografía ni permite determinar por sí sola el volumen interno, la resistencia o la porosidad conectada de la roca. Para esas cuestiones se necesitarán una inspección física, una prueba de estabilidad y, si resulta necesario, una medición de desplazamiento de agua.

### Vistas conceptuales

Vista frontal conceptual del hardscape

Vista superior conceptual del hardscape

## Inventario fotográfico de rocas

Se han identificado **10 piezas**, cada una con cuatro vistas de inventario. Los nombres `roca-01` a `roca-10` son identificadores de inventario y no representan todavía una función en el hardscape. Las fotografías y la descripción completa están en [rocas](rocas/README.md).

Las fotografías del montaje real aportadas durante la operación y este inventario fotográfico se utilizan como referencia visual en la ficha [espacial de Veril](../01_dimensiones/02_espacial.md). Las imágenes no sustituyen las mediciones, la comprobación de apoyos ni la prueba hidráulica.

La [ficha espacial](../01_dimensiones/02_espacial.md) describe la configuración vigente; el diario de Operaciones conserva lo que se ejecutó y sus comprobaciones pendientes.
