RicardoJBarrios/acuario-veril/02_configuracion/03_biologia/README.md

# Biología específica de Veril

Este directorio reúne la aplicación de las fichas biológicas de Veril: criterios de selección, escenarios, compatibilidades, estados de candidatos y decisiones todavía no ejecutadas. La descripción general de cada organismo pertenece a [Verilpedia](../../01_verilpedia/02_biologia/README.md).

## Orden de lectura

La aplicación biológica de Veril se lee en este orden:

1. [Criterios](01_criterios/README.md): condiciones de selección, bienestar, compatibilidad y carga asumible
2. [Candidatos](02_candidatos/README.md): organismos concretos agrupados por tipo y ordenados por estado
3. [Escenarios](03_escenarios/README.md): combinaciones visuales y secuencias posibles de introducción

## Documentos

- [Criterios de selección de corales](01_criterios/01_corales.md)
- [Criterios de selección de fauna](01_criterios/02_fauna.md)
- [Escenario unificado de Veril](03_escenarios/01_escenario-unificado-veril.md)
- [Aplicaciones y estados de candidatos](02_candidatos/README.md)

Estos documentos no acreditan incorporaciones. Las ejecuciones reales se registran en [Operaciones](../../04_operaciones/README.md) y las incorporaciones graduales se planifican en [Maduración](../../03_pendientes/maduracion/README.md).
