RicardoJBarrios/acuario-veril/01_verilpedia/02_biologia/04_peces/README.md

# Peces

Esta categoría reúne las fichas generales y específicas de peces marinos relevantes para acuarios de arrecife.

## Responsabilidad documental

Las fichas describen comportamiento, tamaño adulto, alimentación, territorio, compatibilidad, necesidades de espacio y carga biológica. La población concreta, el orden de incorporación y la aceptación en Veril se documentan fuera de esta categoría.

## Fichas disponibles

- [Gobios y blénidos](01_gobios-blenios/README.md): *Acanthemblemaria*, *Amblyeleotris*, *Coryphopterus*, *Discordipinna*, *Ecsenius*, *Elacatinus*, *Gobiodon*, gobios canarios, *Koumansetta*, *Parablennius*, *Priolepis*, *Stonogobiops*, *Trimma* y *Tripterygion*
- [Peces de columna y cuevas](02_columna-cueva/README.md): *Assessor*, basslets, cardenales, *Nemateleotris*, *Plectranthias*, *Pseudochromis* y *Serranus*
- [Peces especialistas](03_especialistas/README.md): chupasangres canarios, *Rudarius* y *Synchiropus*
- [Lábridos pequeños](04_labridos-pequenos/README.md): *Pseudocheilinops* y *Wetmorella*
- [Payasos y damiselas](05_payasos-damiselas/README.md): *Amphiprion*, *Chromis viridis* y damiselas territoriales
- [Salud de peces](06_salud/README.md): signos, parásitos, enfermedades y problemas de manejo
