RicardoJBarrios/acuario-veril/01_verilpedia/02_biologia/01_microorganismos/README.md

# Microorganismos y microfauna marina

Este bloque reúne fichas generales sobre las comunidades microscópicas y los organismos de pequeño tamaño que participan en la vida de un acuario marino. No describe una comunidad ideal única ni sustituye las decisiones de Veril, los planes de ciclado y maduración o las fichas de parámetros, productos y organismos de mayor tamaño.

## Qué incluye

La categoría se utiliza en sentido documental amplio. Incluye microorganismos estrictos —bacterias, arqueas, microalgas, cianobacterias, protozoos y virus asociados— y también microfauna marina porque ambos niveles forman redes relacionadas de biofilm, consumo, transferencia de materia y alimentación.

La microfauna no es microorganismo en sentido taxonómico estricto. Se incluye aquí por su escala y por su relación funcional con las comunidades microbianas, no para mezclar sus necesidades ni asumir que todos responden de la misma manera.

## Organización

### Bacterias y arqueas

Las fichas de [bacterias y arqueas](01_bacterias/README.md) describen nitrificación, desnitrificación, comammox y transformación heterótrofa. La unidad de análisis es la función microbiana y su demostración, no la identidad comercial de un producto.

### Microfauna

Las fichas de [microfauna](02_microfauna/README.md) describen copépodos y otros microinvertebrados como consumidores, presas, ocupantes de superficies y parte de la red trófica. La incorporación concreta se decide en el plan de maduración del sistema correspondiente.

### Microalgas, cianobacterias y protozoos

- [Microalgas y cianobacterias](03_microalgas-y-cianobacterias/README.md): diatomeas, dinoflagelados y cianobacterias como componentes de biofilms, productores o proliferaciones potencialmente problemáticas
- [Diatomeas](03_microalgas-y-cianobacterias/diatomeas.md), [cianobacterias](03_microalgas-y-cianobacterias/cianobacterias.md) y [dinoflagelados](03_microalgas-y-cianobacterias/dinoflagelados.md): fichas de identificación y control prudente
- [Protozoos y ciliados](04_protozoos-y-ciliados/README.md): consumidores de bacterias y partículas, integrantes de la red microbiana y grupos que requieren identificación prudente
- [Otros microorganismos relacionados](05_otros-microorganismos-marinos/README.md): bacteriófagos, reductores de sulfato y organismos potencialmente patógenos, con sus límites documentales

## Qué pertenece a otros documentos

- El [ciclado](../../06_procesos/01_ciclado.md) comprueba principalmente la capacidad nitrificante; no exige demostrar toda la diversidad microbiana
- La [maduración](../../06_procesos/03_maduracion.md) documenta la sucesión de biofilms, microalgas, microfauna y otros grupos bajo las condiciones reales del sistema
- Los planes de ciclado y maduración de cada sistema documentan inoculantes, cargas, incorporaciones y puertas de decisión concretas
- La dimensión de [procesamiento](../../01_dimensiones/07_procesamiento.md) explica qué transformaciones y retiradas puede realizar el sistema
- La dimensión [química](../../01_dimensiones/05_quimica.md) interpreta las condiciones resultantes sin convertir una lectura en identificación taxonómica

## Cómo interpretar estas fichas

La presencia visible, una lectura de nutrientes, una película o el agua clara no identifican por sí solas una comunidad ni demuestran que una función concreta esté ocurriendo. La interpretación debe combinar identidad o grupo funcional, hábitat, entradas, oxígeno, luz, química, circulación, depredación, mantenimiento y tendencia temporal.

Los productos comerciales pueden introducir o estimular determinados procesos, pero una etiqueta no demuestra qué organismos viables se han establecido ni qué proporción alcanzan en el sistema.
