RicardoJBarrios/acuario-veril/01_verilpedia/02_biologia/02_algas/README.md

# Algas

Esta categoría reúne algas visibles y otros productores macroscópicos relevantes para un acuario marino. Las microalgas y las cianobacterias se documentan en [microorganismos](../01_microorganismos/README.md), porque su escala y su relación con los biofilms requieren otro tratamiento.

## Fichas disponibles

- [Algas coralinas](01_algas-coralinas.md): algas rojas calcificadas, cobertura de superficies y relación con la maduración
- [Macroalgas](02_macroalgas/README.md): *Botryocladia*, *Caulerpa*, *Chaetomorpha*, *Codium*, *Gracilaria*, *Halimeda*, *Halymenia*, *Padina* y *Ulva*, además de algas coralinas incrustantes
- [Algas oportunistas y proliferaciones visibles](algas-oportunistas.md): GHA, *Bryopsis*, *Derbesia*, *Valonia*, crisofíceas y películas pardas

La cobertura actual incluye fichas de algas coralinas y de macroalgas con interés ornamental, ecológico o de exportación. Se podrán añadir nuevas fichas cuando exista una fuente o una necesidad documental concreta.

La inclusión de una especie o grupo en esta categoría no implica que deba incorporarse a Veril. Las decisiones concretas pertenecen a la [implementación de Veril](../../../02_configuracion/README.md), a las fichas de dimensiones y a los planes operativos correspondientes.
