RicardoJBarrios/acuario-veril/01_verilpedia/02_biologia/05_invertebrados/README.md

# Invertebrados marinos

Esta categoría reúne invertebrados marinos que no se documentan en las fichas de cnidarios sésiles ni en las de microorganismos y microfauna.

Puede incluir crustáceos, moluscos, equinodermos, poliquetos, esponjas, tunicados, briozoos y otros invertebrados bentónicos o móviles.

## Responsabilidad documental

Las fichas describen identidad, función, alimentación, tamaño, comportamiento, compatibilidad, crecimiento y riesgos de mantenimiento. «Equipo de limpieza» no es una categoría biológica: cuando sea relevante, se tratará como una función que pueden desempeñar organismos de varios grupos.

## Fichas disponibles

- [Gambas y camarones](01_gambas-camarones/README.md): *Alpheus*, *Brachycarpus*, *Cinetorhynchus*, *Gnathophyllum*, *Lysmata*, *Stenopus* y *Thor*
- [Caracoles pastadores](02_caracoles-pastadores/README.md): *Astraea*, *Bittium*, *Cerithium*, *Columbella*, *Dolabella*, *Nerita*, quitones, *Smaragdia*, *Stomatella*, *Tectus*, *Tricolia*, *Trochus* y *Turbo*
- [Caracoles de arena y restos](03_caracoles-arena-restos/README.md): *Babylonia*, *Engina*, *Euprotomus*, *Nassarius* y *Strombus*
- [Cangrejos ermitaños y cangrejos afines](04_cangrejos-ermitanos/README.md): ermitaños pequeños, patas azules, patas rojas, ermitaño arcoíris, *Calcinus*, cangrejos pomponeros, porcelana, mitrácidos y otras fichas comparativas
- [Equinodermos](05_equinodermos/README.md): ofiuras, estrellas, erizos y pepinos de mar
- [Filtradores](06_filtradores/README.md): ascidias, esponjas y plumeros
- [Riesgos y organismos acompañantes](07_riesgos/README.md): vermétidos, hidroides, polizones y confusiones frecuentes
