RicardoJBarrios/acuario-veril/01_verilpedia/08_practicas/04_diagnostico-y-bioseguridad/README.md

# Diagnóstico y bioseguridad

Este índice reúne fichas transversales para interpretar crecimientos, lesiones, organismos acompañantes y enfermedades posibles en un acuario marino. No convierte una observación visual en un diagnóstico y no sustituye la consulta de fuentes competentes.

## Cómo leer las fichas

Las etiquetas de nivel expresan prioridad de observación, no una medida clínica. «Normal» describe una posibilidad compatible con la sucesión de un sistema; «oportunista» describe un organismo que puede aumentar bajo determinadas condiciones; «plaga» describe un riesgo de expansión o daño; «síndrome» describe un patrón; y «enfermedad» requiere una causa respaldada por evidencia.

Las fichas separan hechos generales, práctica habitual de la afición, inferencias y decisiones de Veril. Cuando una afirmación depende de la especie, la cepa, el método de medición o el ejemplar, se mantiene como condicional.

## Guías

- [Identificación rápida](identificacion-rapida.md)
- [Árbol de diagnóstico](arbol-de-diagnostico.md)
- [Introducción de plagas con corales](introduccion-de-plagas.md)

## Fichas por grupo

- [Diatomeas](../../02_biologia/01_microorganismos/03_microalgas-y-cianobacterias/diatomeas.md)
- [Algas oportunistas](../../02_biologia/02_algas/algas-oportunistas.md): GHA, *Bryopsis*, *Derbesia*, *Valonia* y crisofíceas
- [Cianobacterias](../../02_biologia/01_microorganismos/03_microalgas-y-cianobacterias/cianobacterias.md)
- [Dinoflagelados](../../02_biologia/01_microorganismos/03_microalgas-y-cianobacterias/dinoflagelados.md), con fichas de [*Ostreopsis*](../../02_biologia/01_microorganismos/03_microalgas-y-cianobacterias/ostreopsis.md), [*Amphidinium*](../../02_biologia/01_microorganismos/03_microalgas-y-cianobacterias/amphidinium.md) y [*Prorocentrum*](../../02_biologia/01_microorganismos/03_microalgas-y-cianobacterias/prorocentrum.md)
- [Aiptasia y majano](../../02_biologia/03_cnidarios-sesiles/aiptasia-y-majano.md)
- [Vermétidos e hidroides problemáticos](../../02_biologia/05_invertebrados/07_riesgos/vermetidos-e-hidroides.md)
- [Plagas de corales](../../02_biologia/03_cnidarios-sesiles/01_corales/05_plagas/README.md)
- [Organismos que suelen confundirse con plagas](../../02_biologia/05_invertebrados/07_riesgos/organismos-confundidos-con-plagas.md)
- [Síndromes y enfermedades de corales](../../02_biologia/03_cnidarios-sesiles/01_corales/06_salud/README.md)
- [Enfermedades de peces](../../02_biologia/04_peces/06_salud/README.md)
- [Riesgos sanitarios de invertebrados](../../02_biologia/05_invertebrados/07_riesgos/README.md)

## Alcance

La clasificación «normal», «oportunista», «plaga», «síndrome» o «enfermedad» es una hipótesis de trabajo. Un organismo visible no se considera perjudicial solo por aparecer. La aplicación concreta a Veril se enlaza desde la [configuración biológica](../../../02_configuracion/03_biologia/README.md) y los planes de [maduración](../../../03_pendientes/maduracion/README.md), mientras que las actuaciones ejecutadas pertenecen a [Operaciones](../../../04_operaciones/README.md).
