RicardoJBarrios/acuario-veril/02_configuracion/03_biologia/03_escenarios/README.md

# Escenarios biológicos de Veril

Este directorio reúne combinaciones posibles de organismos, distribución visual, compatibilidades y secuencias de introducción. Un escenario ayuda a evaluar una composición completa, pero no sustituye los criterios, la revisión del candidato real ni una operación ejecutada.

## Documentos

- [Escenario unificado de Veril](01_escenario-unificado-veril.md)

Los escenarios parten de los [criterios](../01_criterios/README.md) y de los [candidatos](../02_candidatos/README.md). Las incorporaciones reales se registran en [Operaciones](../../../04_operaciones/README.md).
