RicardoJBarrios/acuario-veril/03_pendientes/disenos-3d/bactoflex-mini/version-107x57x105/README.md

# Versión 107 × 57 × 105 mm de la cesta BactoFlex Mini

Esta carpeta conserva una versión distinta del diseño modular 50 × 50 × 100
mm. No ha sido eliminada ni reemplazada por la versión modular.

## Archivos

- [`veril-bactoflex.FCStd`](veril-bactoflex.FCStd): fuente paramétrica de esta
  versión.
- [`veril-bactoflex.validado-20260925-151010.FCStd`](veril-bactoflex.validado-20260925-151010.FCStd):
  copia de hito conservada con esta versión.
- [`impresion/`](impresion/README.md): STL, proyectos OrcaSlicer, G-code e
  informe correspondientes al trabajo de fabricación de esta versión.

Las exportaciones y laminados conservan sus límites de validación indicados
en sus propios documentos. No se deben atribuir al modelo modular de la otra
carpeta. La licencia MIT compartida está en
[`../LICENSE`](../LICENSE).
