RicardoJBarrios/acuario-veril/04_operaciones/2026/09/2026-09-24-recepcion-equipo-ro6cb/README.md

# 24 de septiembre de 2026: recepción comunicada del equipo RO6CB

## Hecho comunicado

El propietario comunica que hoy ha llegado el equipo de ósmosis inversa destinado a Veril. La fecha de este registro es el 24 de septiembre de 2026, según la fecha actual de la actuación. No consta todavía el desembalaje ni una inspección física del equipo.

## Etiqueta de la caja

La fotografía de la etiqueta de embalaje, copiada desde Descargas el 24 de septiembre de 2026, muestra los siguientes datos declarados para el producto empaquetado:

| Campo | Texto de la etiqueta |
| --- | --- |
| Tipo | Equipo de ósmosis inversa doméstico |
| Modelo | RO6CB |
| Contenido indicado | Unidad de ósmosis inversa; filtros y membrana; grifo; depósito; manual; accesorios para la instalación |
| Potencia | 36 W |
| Entrada eléctrica | 220 V |
| Frecuencia | 50/60 Hz |
| Clase de protección | IPX1 |
| Presión de entrada de agua | Mín. 0,1 MPa / máx. 0,6 MPa |
| Temperatura de uso | Mín. 5 °C / máx. 35 °C |
| Lote | 2025-AR022 |
| Fecha de fabricación | 19/12/2025 |
| Origen indicado | Made in China |
| Empresa y dirección impresas | ALMACEN OSMOSIS, S. L., Quart de Poblet (Valencia) |

La etiqueta declara una entrada de **220 V**, mientras que la ficha del equipo conserva la indicación de **230 V** del manual de la variante con bomba. Se registran ambas fuentes sin resolver la diferencia: antes de conectar la unidad habrá que comprobar la placa de la bomba y su transformador y seguir sus datos eléctricos específicos.

La lista de contenido de la caja no equivale a un inventario de lo recibido. Esta fotografía acredita lo que declara la etiqueta, no que el contenido esté completo, que el modelo de la unidad coincida con la caja, ni el estado, montaje, estanqueidad, funcionamiento o calidad del agua producida.

## Evidencia fotográfica

- [Etiqueta de caja](evidencias/IMG20260924143053.jpg)

Se conserva una copia sin modificar del JPEG original. Se eligió esta imagen porque muestra la etiqueta completa y ofrece la lectura más clara de sus datos. Los otros dos encuadres redundantes se retiraron de la copia documental; los originales de Descargas no se modificaron.

## Alcance y pendientes

La recepción comunicada del paquete no pone en servicio el RO6CB ni completa el sistema RO/DI de Veril. Siguen pendientes:

- Desembalar e inventariar el equipo y todos sus componentes
- Comparar la unidad, la bomba y el transformador con la etiqueta de la caja y los manuales
- Comprobar daños, referencias, conexiones y accesorios
- Instalar el RO6CB y el sistema DI conforme al diseño documentado
- Verificar presión, fugas, rechazo, purga, caudal y parada del equipo
- Cargar/enjuagar la resina DI y medir la calidad del agua en los puntos previstos antes de usarla para Veril

La ficha del [RO6CB](../../../../01_verilpedia/04_hardware/ro6cb/ro6cb.md), su [aplicación prevista](../../../../01_verilpedia/04_hardware/ro6cb/aplicacion-veril.md) y el [diseño DI](../../../../01_verilpedia/04_hardware/di-ro/sistema-di.md) describen las especificaciones conocidas y los criterios de aceptación. No se consultó telemetría de Home Assistant: no era pertinente para documentar la recepción del paquete.
