RicardoJBarrios/acuario-veril/01_verilpedia/02_biologia/04_peces/05_payasos-damiselas/README.md

# Payasos y damiselas

Fichas generales de *Amphiprion*, damiselas territoriales y damiselas de
columna. La población concreta, el orden de incorporación y la aceptación en
Veril pertenecen al proyecto y a los planes.

## Fichas disponibles

- [*Amphiprion* / peces payaso](amphiprion.md)
- [*Chromis viridis*](chromis-viridis.md)
- [Damiselas territoriales](damiselas-territoriales.md)
