RicardoJBarrios/acuario-veril/01_verilpedia/02_biologia/01_microorganismos/01_bacterias/README.md

# Bacterias y arqueas marinas

Esquema funcional del procesamiento del nitrógeno

**Imagen:** Esquema propio de Verilpedia; no representa una microfotografía ni identifica una especie.

## Qué reúne este bloque

Estas fichas describen grupos funcionales de bacterias y arqueas que participan en la transformación de materia y nitrógeno en un acuario marino. Se mantienen separadas de las fichas de microfauna porque su unidad de análisis es la función microbiana y las condiciones que permiten observar sus resultados, no la incorporación de un organismo visible.

La clasificación es funcional y no pretende representar una comunidad completa. Un mismo proceso puede repartirse entre varios grupos, y un grupo identificado en un estudio no tiene por qué estar presente, dominar o rendir igual en un acuario concreto.

## Responsabilidad documental

Este bloque explica:

- Qué transforma cada grupo y qué productos genera
- Qué condiciones generales necesita
- Cómo se relaciona con otros grupos microbianos
- Qué puede y qué no puede inferirse mediante mediciones domésticas
- Qué límites deben aplicarse al interpretar etiquetas y cultivos comerciales

El [ciclado](../../../06_procesos/01_ciclado.md) define cómo se demuestra la capacidad nitrificante de un sistema. La [maduración](../../../06_procesos/03_maduracion.md) documenta la evolución posterior de biofilms, microfauna y comunidades. Los planes concretos de cada sistema documentan inoculantes, cargas y puertas de decisión. Las fichas de [productos](../../../05_productos/README.md) conservan las afirmaciones y condiciones de cada fabricante.

## Índice

### Nitrificación

- [Bacterias oxidantes de amonio](oxidantes-amonio.md)
- [Arqueas oxidantes de amonio](arqueas-oxidantes-amonio.md)
- [Bacterias oxidantes de nitrito](oxidantes-nitrito.md)
- [Microorganismos comammox](comammox.md)

### Transformación de materia orgánica y nitrato

- [Bacterias heterótrofas y descomponedoras](heterotrofas-descomponedoras.md)
- [Bacterias desnitrificantes](desnitrificantes.md)

## Cómo interpretar estas fichas

Los tests domésticos observan concentraciones y tendencias del agua, no identifican taxones ni asignan una conversión a un grupo concreto. La capacidad del sistema se demuestra mediante una respuesta reproducible ante una carga conocida y bajo condiciones registradas.

La presencia de un grupo no equivale a una función dominante, y la transformación de una sustancia no equivale necesariamente a su exportación. La [dimensión de procesamiento](../../../01_dimensiones/07_procesamiento.md) describe esa diferencia a escala del sistema.
