RicardoJBarrios/acuario-veril/01_verilpedia/02_biologia/01_microorganismos/03_microalgas-y-cianobacterias/README.md

# Microalgas y cianobacterias

Cianobacterias filamentosas al microscopio

**Imagen:** iNaturalist, [Cyanobacteria (Class Cyanophyceae)](https://www.inaturalist.org/taxa/196963-Cyanophyceae), licencia CC BY-NC.

## Descripción

Las microalgas son organismos fotosintéticos microscópicos que pueden formar parte de la columna de agua, los biofilms y las superficies del acuario. Las diatomeas y los dinoflagelados pertenecen a grupos distintos y no deben tratarse como una única categoría funcional.

Para la interpretación de coberturas visibles, consultar las fichas específicas de [diatomeas](diatomeas.md), [cianobacterias](cianobacterias.md) y [dinoflagelados](dinoflagelados.md). Esta ficha conserva el marco general y no sustituye esas distinciones.

## Fichas específicas

- [Diatomeas](diatomeas.md)
- [Cianobacterias](cianobacterias.md)
- [Dinoflagelados](dinoflagelados.md)
- [*Ostreopsis*](ostreopsis.md)
- [*Amphidinium*](amphidinium.md)
- [*Prorocentrum*](prorocentrum.md)

Las cianobacterias son bacterias fotosintéticas. En un acuario pueden formar parte normal de los biofilms, pero algunas proliferaciones producen mantos visibles y viscosos que alteran la estética, la superficie disponible y, en determinados casos, la salud de otros organismos.

## Función en un acuario marino

Según el grupo y la abundancia, pueden:

- Producir materia orgánica mediante fotosíntesis
- Consumir nutrientes inorgánicos y transferirlos a biomasa
- Formar parte del biofilm y ofrecer alimento a consumidores pequeños
- Participar en la sucesión inicial de superficies nuevas
- Interactuar con bacterias, partículas y otros organismos del biofilm

Estas funciones no convierten a una proliferación visible en un mecanismo de exportación. La biomasa solo abandona el sistema si se retira o se consume y la materia no vuelve a incorporarse después.

## Qué ocurre si están presentes

Una presencia moderada puede ser una parte normal de la colonización y de la red trófica. Diatomeas, cianobacterias y dinoflagelados pueden coexistir en biofilms, pero la apariencia de una película no permite identificar el grupo con seguridad.

Una proliferación densa puede sombrear superficies, consumir oxígeno durante la noche, atrapar sedimentos, competir por espacio y alterar la disponibilidad de nutrientes. El riesgo depende del organismo, la densidad, la duración y la respuesta del resto del sistema.

## Qué ocurre si son escasas o no se detectan

La ausencia visible no significa ausencia biológica: pueden existir células o biofilms no observables a simple vista. Tampoco es necesario mantener una cantidad determinada de microalgas o cianobacterias para demostrar el ciclado.

Si desaparecen, pueden cambiar el consumo de nutrientes y la disponibilidad de alimento para algunos consumidores. Ese cambio debe interpretarse junto con las entradas, la microfauna, la iluminación y la química, no como una mejora automática.

## ¿Se necesitan?

No se necesita una especie concreta ni una proliferación visible. Algunas microalgas pueden formar parte de una comunidad funcional y de la alimentación de determinados organismos, pero el sistema debe poder mantenerse sin convertir una plaga en un objetivo biológico.

## ¿Son beneficiosas o perjudiciales?

Su efecto es dependiente del grupo y de la escala:

- **Potencialmente beneficiosas**: Como productores, componentes de biofilm o alimento de consumidores
- **Potencialmente perjudiciales**: Cuando forman mantos persistentes, producen compuestos irritantes o tóxicos, sombrean organismos, consumen oxígeno o dificultan el mantenimiento

No se debe clasificar una película por color o textura únicamente. Diatomeas, cianobacterias y dinoflagelados pueden requerir respuestas distintas.

## Necesidades y hábitat

Necesitan combinaciones variables de luz, nutrientes, superficies, dióxido de carbono, temperatura, salinidad, movimiento de agua y competencia biológica. Las diatomeas pueden aprovechar superficies nuevas y sílice disponible; las cianobacterias pueden formar matrices sobre sustrato y roca; los dinoflagelados pueden ser bentónicos o planctónicos según el grupo.

La circulación, la iluminación y la química condicionan el hábitat, pero ninguna de esas dimensiones identifica por sí sola el organismo presente. La descripción específica de esas condiciones pertenece a las dimensiones correspondientes.

## Presencia espontánea e inoculación

Pueden aparecer espontáneamente con el agua, el polvo, la roca, el sustrato, los organismos, el alimento o las superficies colonizadas. También pueden introducirse mediante cultivos de fitoplancton o material vivo, pero la introducción no garantiza que se establezca el grupo deseado.

No se inocularán como requisito del ciclado. Una inoculación deliberada solo tendrá sentido si existe un organismo consumidor o una finalidad de maduración documentada, con procedencia y composición evaluables.

## Cómo favorecerlas o limitarlas

La luz, los nutrientes, el movimiento, la retirada física, la competencia y el pastoreo pueden modificar su abundancia. No se cambiarán varias de estas variables a la vez para corregir una apariencia sin identificar primero el grupo y la causa probable.

La respuesta a una proliferación persistente debe considerar retirada física, acceso, carga orgánica, nutrientes, oxigenación, iluminación y organismos afectados. Un tratamiento genérico contra “algas” no demuestra que se haya actuado sobre la causa correcta.

## Qué puede demostrarse

El color, las burbujas, el moco y el momento del día permiten formular hipótesis, pero no identifican de forma fiable una especie. La identificación requiere observación microscópica, análisis especializado o una fuente con trazabilidad suficiente.

La disminución de nitrato o fosfato tampoco demuestra por sí sola que una microalga o cianobacteria sea la causa: pueden intervenir cambios de agua, biomasa, adsorción, exportación y otros consumidores.

## Relación con ciclado y maduración

Las diatomeas, cianobacterias y otras microalgas pueden aparecer durante la sucesión de superficies, pero no constituyen una prueba de ciclado completado ni de madurez ecológica. El [ciclado](../../../06_procesos/01_ciclado.md) evalúa principalmente la transformación de nitrógeno amoniacal.

La [maduración](../../../06_procesos/03_maduracion.md) observa su aparición, persistencia, competencia y relación con biofilm, microfauna, iluminación y nutrientes. Cualquier introducción deliberada se documenta en el plan operativo correspondiente.

## Fuentes

- [Development of Antifouling Strategies for Marine Applications](https://pmc.ncbi.nlm.nih.gov/articles/PMC10305701/), sobre biofilms marinos y microfouling por bacterias, cianobacterias y diatomeas
- [Culturing Toxic Benthic Blooms: The Fate of Natural Biofilms in a Microcosm System](https://pmc.ncbi.nlm.nih.gov/articles/PMC5620637/), sobre proliferaciones bentónicas de dinoflagelados y su relación con biofilms
- [Review of Harmful Algal Blooms Causing Marine Fish Kills](https://pmc.ncbi.nlm.nih.gov/articles/PMC10871120/), sobre proliferaciones algales perjudiciales y límites de su interpretación
