RicardoJBarrios/acuario-veril/01_verilpedia/02_biologia/01_microorganismos/04_protozoos-y-ciliados/README.md

# Protozoos y ciliados marinos

Ciliados observados al microscopio

**Imagen:** The Happy Scientist, [Microscope] (imagen representativa).

## Descripción

Los protozoos son organismos eucariotas unicelulares. En los biofilms y la columna de agua pueden incluir ciliados, flagelados y otros grupos con dietas y ciclos de vida diferentes. La expresión “protozoo” es funcional y amplia, no una identificación suficiente de especie.

## Función en un acuario marino

Pueden:

- Consumir bacterias, partículas finas y otros microorganismos
- Transferir biomasa microbiana a copépodos, larvas, corales y otros filtradores
- Participar en la descomposición y en la redistribución de materia
- Contribuir a la dinámica de los biofilms y de la columna de agua

Algunos protozoos son parásitos o patógenos. No debe confundirse la función de los ciliados libres del biofilm con la de un parásito de peces o invertebrados.

## Qué ocurre si están presentes

Su presencia puede reflejar una comunidad microbiana activa y una red trófica desarrollada. Una abundancia elevada también puede coincidir con exceso de materia orgánica o con una proliferación asociada a un hospedador enfermo; la observación debe contextualizarse.

## Qué ocurre si son escasos o no se detectan

La ausencia en una observación visual no demuestra que no existan. Muchos son pequeños, intermitentes o están asociados a superficies no observadas. No se necesita detectar protozoos para validar el ciclado ni para considerar viable un sistema.

## ¿Se necesitan?

No se necesita una especie concreta ni una inoculación rutinaria. Forman parte potencial de la red microbiana y pueden aportar funciones tróficas, pero la estabilidad del acuario no depende de demostrar su presencia mediante una observación aislada.

## ¿Son beneficiosos o perjudiciales?

Los ciliados y flagelados de vida libre pueden ser beneficiosos como consumidores y presas. Otros protozoos pueden ser perjudiciales si parasitan o lesionan a peces, corales o invertebrados. La clasificación depende de la identidad, el hospedador y la dinámica observada.

## Necesidades y hábitat

Los grupos de vida libre necesitan agua, bacterias, partículas, biofilm y condiciones químicas compatibles. Pueden ocupar la columna de agua, el sustrato, la roca, las películas superficiales y las zonas protegidas. Los parásitos dependen además de un hospedador y de su ciclo de transmisión.

La disponibilidad de alimento, la depredación, la filtración mecánica, la circulación y la edad del biofilm modifican su abundancia. Estas variables se documentan en las dimensiones y planes correspondientes.

## Presencia espontánea e inoculación

Pueden aparecer espontáneamente con el agua, los materiales, la roca, el sustrato, los alimentos y los organismos. Los cultivos de rotíferos o fitoplancton pueden transportar organismos acompañantes, pero no deben considerarse una inoculación selectiva de protozoos.

No se introducirán cultivos de origen desconocido para “crear biodiversidad” sin evaluar su composición, trazabilidad y riesgo sanitario.

## Cómo favorecerlos o limitarlos

La disponibilidad de biofilm y partículas, junto con superficies estables, puede favorecer comunidades de vida libre. La retirada de materia orgánica, la filtración, los cambios de agua y el control de entradas pueden reducir una proliferación, pero no deben aplicarse sin identificar el problema que se pretende resolver.

Si existe sospecha de parasitismo o enfermedad, la respuesta pertenece a un protocolo de salud y bioseguridad, no a la gestión general de microfauna.

## Qué puede demostrarse

Una película, turbidez o movimiento puntual no identifica un protozoo. La observación microscópica puede ayudar, pero la identificación y el diagnóstico de parásitos requieren una evaluación especializada y un contexto clínico.

## Relación con ciclado y maduración

Los protozoos pueden formar parte de la sucesión de biofilms y de la red trófica durante la [maduración](../../../06_procesos/03_maduracion.md). No son un criterio de cierre del [ciclado](../../../06_procesos/01_ciclado.md) ni una prueba suficiente de madurez.

## Fuentes

- [Protist-Bacteria Associations in Ciliated Protozoa](https://pmc.ncbi.nlm.nih.gov/articles/PMC4826875/), sobre relaciones entre ciliados y bacterias marinas
- [Microbial Surface Colonization and Biofilm Development in Marine Environments](https://pmc.ncbi.nlm.nih.gov/articles/PMC4711185/), sobre biofilms y comunidades microbianas marinas
