RicardoJBarrios/acuario-veril/01_verilpedia/02_biologia/01_microorganismos/05_otros-microorganismos-marinos/README.md

# Otros microorganismos marinos relacionados

Esquema funcional de una red microbiana marina

**Imagen:** Esquema propio de Verilpedia; se incluye como recurso conceptual, no como identificación de un organismo.

Esta ficha reúne grupos relevantes que no forman todavía una ficha independiente en este repositorio. Su inclusión evita presentar la microbiología del acuario como si se limitara a la nitrificación, pero no pretende convertir cada grupo en un objetivo de cultivo o mantenimiento.

## Bacteriófagos

Los bacteriófagos son virus que infectan bacterias. Pueden influir en la abundancia y el intercambio de materia de las comunidades bacterianas, pero su presencia, diversidad y efecto no pueden inferirse mediante tests domésticos ni controlarse con una rutina general de acuario.

No se inocularán ni se eliminarán de forma selectiva. La gestión se limita a mantener condiciones estables y a interpretar la comunidad bacteriana por sus respuestas observables.

## Bacterias reductoras de sulfato

Algunas bacterias reductoras de sulfato utilizan sulfato como aceptor de electrones y pueden producir sulfuro bajo condiciones muy reductoras. Forman parte de procesos anaerobios naturales, pero una acumulación de sulfuro en una zona cerrada o removida bruscamente puede ser peligrosa.

Su presencia no es un requisito del ciclado. La creación o explotación deliberada de zonas anóxicas pertenece a la [dimensión de procesamiento](../../../01_dimensiones/07_procesamiento.md) y a la [dimensión química](../../../01_dimensiones/05_quimica.md), no a esta ficha general.

## Microorganismos potencialmente patógenos

El agua marina puede contener bacterias oportunistas, como algunas especies de *Vibrio*, y otros organismos capaces de afectar a animales bajo determinadas condiciones. Su presencia ambiental no equivale a enfermedad y no puede deducirse por una lectura de nutrientes.

La prevención y respuesta corresponden a salud, bioseguridad, cuarentena, observación clínica y fichas específicas de organismos cuando existan. No se intentará esterilizar el acuario ni eliminar selectivamente toda bacteria potencialmente patógena.

## Parásitos microscópicos

Los protozoos y otros organismos parásitos pueden afectar a peces o invertebrados, pero su documentación pertenece a salud y diagnóstico, no a la ficha general de microorganismos funcionales. La aparición de una enfermedad no se interpretará como un simple desequilibrio de la maduración.

## Relación con otras áreas

- El [ciclado](../../../06_procesos/01_ciclado.md) no necesita demostrar bacteriófagos, reductores de sulfato, patógenos ni parásitos
- La [maduración](../../../06_procesos/03_maduracion.md) puede cambiar las condiciones que favorecen o limitan estos grupos, pero no tiene como objetivo desarrollarlos
- La [dimensión de procesamiento](../../../01_dimensiones/07_procesamiento.md) describe transformaciones y exportaciones, incluida la necesidad de no confundir reducción con retirada segura
- La [dimensión química](../../../01_dimensiones/05_quimica.md) permite interpretar oxígeno, sulfuro, pH, alcalinidad y nutrientes cuando exista una observación o hipótesis concreta

## Límites

La categoría “otros microorganismos” no debe utilizarse como explicación residual para cualquier cambio del acuario. Cuando exista un problema, se documentará la observación, se formularán hipótesis diferenciadas y se elegirá el documento propietario: salud, química, procesamiento, operación, ciclado o maduración.
