RicardoJBarrios/acuario-veril/01_verilpedia/02_biologia/04_peces/06_salud/README.md

# Salud de peces

## Fichas

- [Enfermedades y problemas de peces marinos](enfermedades-y-problemas.md)

## Criterio

Los signos externos se solapan. Puntos blancos, respiración rápida, erosiones o apatía requieren observar tendencia, apetito, oxigenación y exposición previa antes de asignar un agente.
