RicardoJBarrios/acuario-veril/04_operaciones/2026/09/2026-09-13-observacion-cambio-color-hardscape/README.md

# 2026-09-13 — Observación de cambio de color del hardscape

## Estado

Observación visual documentada; causa y significado biológico pendientes

## Contexto

El sistema contiene agua marina y la composición rocosa fue fijada con AF Stone
Fix durante el montaje. No se había añadido un inoculante de ciclado, según la
información disponible en esta revisión.

## Observación

En dos fotografías tomadas el 13 de septiembre de 2026 aproximadamente a las
01:55 se aprecia una coloración irregular verdosa, parda y violácea sobre varias
superficies de la roca y en zonas de unión. Las imágenes no permiten distinguir
con seguridad si el color pertenece al material de fijación, a la roca, a un
recubrimiento superficial o a una combinación de ellos.

## ¿Puede haber empezado el ciclado?

Sí, es posible que el agua marina haya aportado microorganismos y que algunas
superficies hayan empezado a colonizarse aunque no se inoculara el acuario de
forma deliberada. Sin embargo, **el cambio de color no demuestra que haya
empezado ni que esté avanzado el ciclado**.

Para llamar a esto ciclado haría falta observar una transformación medible de
una fuente de nitrógeno mediante una serie comparable de amonio/amoníaco,
nitrito y nitrato, con fechas, método y condiciones registradas. Sin una fuente
de amonio añadida o una carga orgánica identificada, también es posible que la
actividad sea escasa, localizada o distinta de la nitrificación.

La coloración observada puede ser compatible con biofilm, microalgas,
diatomeas, cianobacterias, precipitación o cambios/recubrimientos del AF Stone
Fix. La fotografía por sí sola no permite elegir entre esas explicaciones ni
identificar un organismo.

## Evidencia

- [Fotografía 01](evidencias/IMG20260913015540.jpg), SHA-256
  `274d444b91d8d44f73fffc95df0c0df964b02d2dc55a9cf60ef9cbaf45eab20650`
- [Fotografía 02](evidencias/IMG20260913015546.jpg), SHA-256
  `2245542047d7114b00e50681ba43e57a11665bd6c15a3f728fb46c0a6b88381d`

## Pendientes derivados

- [ ] No raspar ni aplicar productos a la coloración antes de fotografiarla y
  describir su textura, olor, desprendimiento y localización
- [ ] Registrar si la coloración aumenta, disminuye o cambia de aspecto en
  observaciones posteriores
- [ ] Confirmar con el fabricante o la documentación del AF Stone Fix su
  aspecto esperado durante curado y contacto prolongado con agua marina
- [ ] Medir amonio/amoníaco, nitrito y nitrato con métodos adecuados y registrar
  fecha, temperatura, escala y resultado
- [ ] Repetir las mediciones en serie antes de afirmar que el ciclado ha
  comenzado o está completado
- [ ] Mantener la reposición de evaporación con agua RO/DI sin sales añadidas

## Fuentes internas

- [Comprobación de salinidad del 13 de septiembre](../2026-09-13-comprobacion-salinidad-refractometro.md)
- [Montaje y primer llenado](../2026-09-05-montaje-y-primer-llenado/README.md)
- [Parámetro: salinidad](../../../../01_verilpedia/03_parametros/salinidad.md)
- [Plan de ciclado](../../../../03_pendientes/ciclado/plan.md)
