RicardoJBarrios/acuario-veril/01_verilpedia/02_biologia/02_algas/02_macroalgas/README.md

# Macroalgas

Fichas generales de algas macroscópicas. La función ornamental, la exportación de nutrientes y la compatibilidad con herbívoros se describen sin convertirlas en una pauta de incorporación para Veril.

## Fichas disponibles

- [Algas coralinas](algas-coralinas.md)
- *Botryocladia botryoides*
- *Caulerpa prolifera*
- *Chaetomorpha*
- *Codium taylorii*
- *Gracilaria*
- *Halimeda discoidea*
- *Halymenia*
- *Padina pavonica*
- *Ulva*
