RicardoJBarrios/acuario-veril/01_verilpedia/02_biologia/03_cnidarios-sesiles/01_corales/README.md

# Corales

Índice de las fichas generales de corales sésiles, agrupadas por necesidades de mantenimiento y estrategia alimentaria. La clasificación orienta la lectura y no sustituye la identificación taxonómica.

## Subgrupos

- [Corales blandos y gorgonias](01_blandos/README.md)
- [Corales LPS](02_lps/README.md)
- [Corales NPS](03_nps/README.md)
- [Corales SPS](04_sps/README.md)
