RicardoJBarrios/acuario-veril/01_verilpedia/02_biologia/03_cnidarios-sesiles/02_analogos-coraliformes/README.md

# Análogos coraliformes

Fichas de anémonas, coralimorfarios y zoántidos que pueden ocupar un papel visual o funcional parecido al de un coral, sin convertirlos taxonómicamente en corales.
