RicardoJBarrios/acuario-veril/01_verilpedia/02_biologia/04_peces/01_gobios-blenios/README.md

# Gobios y blénidos

Fichas generales de peces de roca, percha, agujero, grieta o madriguera. La selección concreta para Veril se documenta en [candidatos de peces](../../../../02_configuracion/03_biologia/02_candidatos/peces.md).
