RicardoJBarrios/acuario-veril/01_verilpedia/02_biologia/04_peces/02_columna-cueva/README.md

# Peces de columna y cuevas

Fichas generales de peces que utilizan la columna baja, repisas, cuevas o refugios abiertos. La selección concreta para Veril se documenta en [candidatos de peces](../../../../02_configuracion/03_biologia/02_candidatos/peces.md).
