RicardoJBarrios/acuario-veril/01_verilpedia/02_biologia/04_peces/03_especialistas/README.md

# Peces especialistas

Fichas generales de peces con dietas, relaciones o funciones ecológicas especializadas. Una función natural no convierte al pez en herramienta de mantenimiento ni implica incorporación a Veril.
