RicardoJBarrios/acuario-veril/01_verilpedia/02_biologia/04_peces/04_labridos-pequenos/README.md

# Lábridos pequeños

Fichas generales de lábridos de pequeño tamaño y conducta activa o críptica. La selección concreta para Veril se documenta en [candidatos de peces](../../../../02_configuracion/03_biologia/02_candidatos/peces.md).
