RicardoJBarrios/acuario-veril/01_verilpedia/02_biologia/05_invertebrados/01_gambas-camarones/README.md

# Gambas y camarones

Fichas generales de gambas y camarones marinos. La compatibilidad, la alimentación y el comportamiento deben valorarse para cada especie y no por la función informal de «equipo de limpieza».
