RicardoJBarrios/acuario-veril/01_verilpedia/02_biologia/05_invertebrados/02_caracoles-pastadores/README.md

# Caracoles pastadores

Fichas generales de caracoles que pueden consumir algas, biofilm o detritos superficiales. El pastoreo observado no garantiza que controlen una proliferación ni que sean compatibles con cualquier sistema.
