RicardoJBarrios/acuario-veril/01_verilpedia/02_biologia/05_invertebrados/03_caracoles-arena-restos/README.md

# Caracoles de arena y restos

Fichas generales de caracoles asociados a arena, materia orgánica o restos de alimentación. Sus funciones y límites se describen por especie, sin convertirlas en una receta de mantenimiento.
