RicardoJBarrios/acuario-veril/01_verilpedia/02_biologia/05_invertebrados/04_cangrejos-ermitanos/README.md

# Cangrejos ermitaños y afines

Fichas generales de cangrejos ermitaños y otros crustáceos bentónicos comparables. Se mantienen diferenciados el comportamiento, la dieta y el riesgo de depredación de cualquier función de limpieza.
