RicardoJBarrios/acuario-veril/01_verilpedia/02_biologia/05_invertebrados/05_equinodermos/README.md

# Equinodermos

Esta categoría reúne fichas generales de ofiuras, estrellas, erizos y pepinos de mar. La función de pastoreo, remoción o biodiversidad no implica que el organismo deba incorporarse a Veril.
