RicardoJBarrios/acuario-veril/01_verilpedia/02_biologia/05_invertebrados/06_filtradores/README.md

# Invertebrados filtradores

Esta categoría reúne fichas generales de ascidias, esponjas y otros organismos filtradores. La disponibilidad de partículas, el flujo y la alimentación son requisitos biológicos que deben distinguirse de cualquier decisión concreta del proyecto.
