RicardoJBarrios/acuario-veril/01_verilpedia/02_biologia/01_microorganismos/02_microfauna/README.md

# Microfauna marina

Estas fichas reúnen organismos pequeños asociados a roca, sustrato, biofilms, cristales, refugios y zonas técnicas. Se documentan por función y por grupos reconocibles, sin tratar la microfauna como una comunidad uniforme ni como un equipo de limpieza.

## Índice

- [Copépodos marinos](copepodos-marinos.md)
- [Microinvertebrados marinos](microinvertebrados-marinos.md)

La incorporación concreta pertenece al plan operativo de maduración del sistema correspondiente.
