RicardoJBarrios/acuario-veril/01_verilpedia/02_biologia/03_cnidarios-sesiles/01_corales/05_plagas/README.md

# Plagas asociadas a corales

Estas fichas describen riesgos de entrada con frags y corales. La ausencia de una plaga durante una inspección no equivale a ausencia garantizada de huevos u organismos ocultos.

## Fichas

- [Plagas de SPS y LPS](plagas-de-sps-y-lps.md): AEFW, nudibranquios de *Montipora*, red bugs y planarias
- [Plagas de Zoanthus](plagas-de-zoanthus.md): nudibranquios, arañas y caracoles *Heliacus*

Las plagas de *Acropora* siguen siendo relevantes como riesgo de futuras incorporaciones aunque el coral no forme parte de la población actual. Los baños, la inspección y la observación se explican en [Introducción de plagas con corales](../../../../08_practicas/04_diagnostico-y-bioseguridad/introduccion-de-plagas.md).
