RicardoJBarrios/acuario-veril/01_verilpedia/02_biologia/03_cnidarios-sesiles/01_corales/06_salud/README.md

# Salud de corales

Estas fichas separan síntomas visibles, síndromes descriptivos y enfermedades cuya causa requiere evidencia adicional. No se diagnostica una enfermedad por color, cierre o pérdida de tejido aislados.

## Ficha

- [Síndromes, enfermedades y síntomas](sindromes-y-enfermedades.md)

La selección, observación y aceptación de corales en Veril pertenecen a los [criterios del proyecto](../../../../../02_configuracion/03_biologia/01_criterios/01_corales.md). La cuarentena e inspección de entradas se mantienen en las [prácticas de bioseguridad](../../../../08_practicas/04_diagnostico-y-bioseguridad/introduccion-de-plagas.md).
