RicardoJBarrios/acuario-veril/01_verilpedia/02_biologia/03_cnidarios-sesiles/01_corales/01_blandos/README.md

# Corales blandos y gorgonias

Fichas generales de corales blandos, gorgonias y organismos de crecimiento flexible. La selección, ubicación y aceptación en Veril pertenecen al proyecto y a los planes correspondientes.
