RicardoJBarrios/acuario-veril/01_verilpedia/02_biologia/03_cnidarios-sesiles/01_corales/03_nps/README.md

# Corales NPS

Fichas generales de corales y organismos sésiles no fotosintéticos o de alimentación predominantemente dirigida. La presencia de esta categoría no implica que sean adecuados para el sistema de Veril.
