RicardoJBarrios/acuario-veril/01_verilpedia/04_hardware/ro6cb/ro6cb.md

# Equipo de ósmosis inversa RO6CB

## Identificación

| Campo | Valor documentado |
| --- | --- |
| Marca o título comercial | Nature Water Professionals |
| Fabricante indicado en el anuncio | ALMACEN OSMOSIS, S. L. |
| Código del fabricante | A1002 |
| Modelo anunciado | RO6CB |
| Tipo | Equipo doméstico de ósmosis inversa de seis etapas con bomba de refuerzo |
| Membrana anunciada | Vontron de 50 GPD |
| Caudal anunciado | 180 L/día |
| Alimentación | Eléctrica; el manual de la variante con bomba indica 230 V |
| Dimensiones anunciadas | 42 × 14 × 47 cm |
| Peso anunciado | 12,5 kg |
| ASIN | B01D4P4M7O |

El título comercial de Amazon identifica el producto como **Nature Water Professionals**, mientras que la tabla de información del anuncio identifica como fabricante a **ALMACEN OSMOSIS, S. L.**. El anuncio también muestra el código `A1002` y el modelo `RO6CB`. La identificación definitiva de la unidad será la etiqueta del equipo, el embalaje y la documentación recibida.

La etiqueta exterior de la caja recibida el 24 de septiembre de 2026 declara modelo RO6CB, potencia de 36 W, entrada de 220 V, frecuencia de 50/60 Hz, protección IPX1, presión de entrada de 0,1–0,6 MPa, temperatura de uso de 5–35 °C, lote 2025-AR022 y fabricación el 19/12/2025. La transcripción y sus fotografías están en el [registro de recepción](../../../04_operaciones/2026/09/2026-09-24-recepcion-equipo-ro6cb/README.md). Es información de la caja, no verificación de la unidad. La tensión declarada difiere de los 230 V que indica el manual de la variante con bomba, por lo que se comprobarán la placa de la bomba y el transformador antes de conectar.

La aplicación prevista en Veril se describe en [Aplicación del equipo RO6CB en Veril](aplicacion-veril.md).

## Etapas y elementos declarados

El anuncio describe seis etapas funcionales:

1. Filtro de sedimentos de 5 micras
2. Filtro de carbón granulado
3. Filtro de carbón en bloque
4. Membrana de ósmosis inversa Vontron de 50 GPD
5. Postfiltro de carbón
6. Postfiltro remineralizador

El anuncio enumera cinco filtros más la membrana, mientras que los manuales muestran la disposición de los vasos, la membrana y los postfiltros según distintas variantes de la familia RO6. La presencia, el orden, la referencia y la conexión efectiva de cada elemento deben comprobarse en la unidad recibida.

## Componentes anunciados

El anuncio declara que el kit incluye:

- Equipo de ósmosis inversa
- Bomba de refuerzo
- Membrana Vontron de 50 GPD
- Filtro de sedimentos
- Filtro de carbón granulado
- Filtro de carbón en bloque
- Postfiltro de carbón
- Postfiltro remineralizador
- Depósito de agua
- Grifo de servicio
- Herramientas de montaje
- Manuales de montaje
- Tuberías, conexiones y accesorios
- Repuestos necesarios para la instalación anunciada

La lista del anuncio no sustituye al inventario físico del paquete. La identificación de la bomba, el transformador, los presostatos, el solenoide, el restrictor de flujo, la capacidad real del depósito y las referencias de los cartuchos queda pendiente de recepción y desembalaje.

## Datos de presión y funcionamiento

| Parámetro | Valor documentado | Límite |
| --- | --- | --- |
| Presión mínima anunciada | 1,5 bar | Procede del anuncio de venta |
| Presión máxima anunciada | 6 bar | Procede del anuncio y coincide con los manuales |
| Presión mínima en el manual RO6/RO6CB con bomba | 1 bar | No debe tomarse como confirmación de la instalación doméstica concreta |
| Presión de entrada para equipos sin bomba | 4–6 bar | No aplica como condición principal si la unidad recibida incorpora bomba |
| Agua de entrada | Agua potable fría de red | No utilizar agua caliente ni agua de origen desconocido |
| Temperatura máxima | 35 °C en el manual RO6 Gold; otra edición indica 45 °C | Se adoptará provisionalmente el límite más conservador de 35 °C |
| Alimentación de la bomba | 230 V según el manual | Requiere instalación eléctrica segura y protegida |

La diferencia entre 1 bar, 1,5 bar y 4 bar depende de la variante y del modo de funcionamiento descrito. La presión real de la toma donde se instale el equipo debe medirse antes de ponerlo en servicio. Si supera 6 bar, los manuales indican instalar una válvula reductora.

El valor de 50 GPD y el caudal de 180 L/día son datos de catálogo que no constituyen un caudal garantizado. La presión, la temperatura, la salinidad o composición del agua de entrada, el estado de los filtros, la membrana, el restrictor y la contrapresión determinan el rendimiento real.

La documentación de Vontron para la membrana residencial ULP1812-50 utiliza condiciones de ensayo de 60 psi, 25 °C, 250 ppm de NaCl, pH 6,5–8,5 y una recuperación de elemento del 15 %. En esas condiciones declara 50 GPD y una tasa de rechazo estable del 99 %, con una tolerancia individual del caudal. No se puede afirmar que la membrana instalada sea exactamente ULP1812-50 ni que la instalación de Veril reproduzca esas condiciones hasta comprobar la referencia física.

## Funcionamiento previsto por el fabricante

La membrana separa una corriente de agua osmotizada de una corriente de rechazo que debe conducirse al desagüe. La bomba de refuerzo, el presostato de baja, el presostato de alta y el solenoide controlan el funcionamiento de la unidad con depósito según la variante instalada.

El equipo está documentado por el fabricante para producir agua destinada al consumo doméstico. Esa finalidad no demuestra que el agua sea adecuada para un acuario marino ni que el equipo produzca agua desionizada. La remineralización final es incompatible con tratar la salida posterior como agua DI.

## Manuales conservados

- [Manual RO6 Gold en español](manual-ro6-gold-es.pdf): 34 páginas; edición de mayo de 2025, según sus metadatos
- [Manual RO6/RO6CB y ECO](manual-ro6-ro6cb-eco.pdf): 24 páginas; documentación de la familia RO6/RO6CB

Las imágenes de los manuales pueden corresponder a variantes cercanas y no necesariamente a todos los elementos de la unidad recibida. La etiqueta del equipo y el contenido del paquete prevalecen para la identificación física.

## Instalación y mantenimiento descritos

Los manuales indican, entre otras condiciones:

- Instalar el equipo únicamente en la entrada de agua fría potable
- Desconectar la alimentación eléctrica antes de manipular filtros, membrana o conexiones
- Revisar juntas, conectores rápidos, roscas y tuberías para evitar fugas
- Mantener la presión de entrada dentro del límite de la variante instalada
- Conducir el agua de rechazo al desagüe mediante el restrictor de flujo y el collarín correspondiente
- Comprobar la presión de aire del depósito vacío, indicada entre 5 y 7 PSI en el manual RO6 Gold
- Realizar los vaciados completos indicados por el manual después de instalar o sustituir filtros
- Comprobar la calidad de salida con TDS y seguir la frecuencia de sustitución indicada por el fabricante

El manual menciona como referencia una sustitución anual de filtros y una comprobación de TDS cada seis meses, pero la frecuencia efectiva dependerá del agua de entrada, el uso y la evolución de las mediciones. No se trasladan esas frecuencias como calendario cerrado de Veril.

## Límites de interpretación

- La declaración de eliminación de impurezas o de hasta el 99 % atribuida a la membrana no es una medición independiente de esta unidad
- El caudal de catálogo no equivale al caudal real de agua osmotizada en la instalación
- La bomba no elimina la necesidad de controlar presión, fugas, rechazo y estado de los filtros
- El depósito y el postfiltro remineralizador forman parte del uso doméstico anunciado, pero no deben confundirse con la producción de agua RO/DI para el acuario
- La presencia de un manual de la familia RO6/RO6CB no confirma por sí sola que todos sus componentes correspondan a la unidad vendida

## Fuentes

- [Anuncio del equipo RO6CB en Amazon](https://www.amazon.es/dp/B01D4P4M7O)
- [Catálogo oficial de membranas residenciales Vontron](https://en.vontron.com/Product/60.html)
- [Manual RO6 Gold en español](manual-ro6-gold-es.pdf)
- [Manual RO6/RO6CB y ECO](manual-ro6-ro6cb-eco.pdf)
