RicardoJBarrios/acuario-veril/01_verilpedia/04_hardware/di-ro/resina-xepta-rodi.md

# Resina XEPTA RODI RESIN

## Estado de selección para Veril

La opción seleccionada para el sistema DI previsto es **XEPTA RODI RESIN de 1000 ml**.

Se adopta como resina de lecho mixto para cargar las dos carcasas T33 en serie, siempre que su capacidad útil real lo permita. El volumen de 1000 ml ofrece margen frente a una presentación de 300 ml, pero no se afirma que deba utilizarse todo el envase ni que una carga concreta produzca una cantidad determinada de agua.

La [investigación sobre XEPTA y Resinex MX-2](fuentes/2026-09-21-investigacion-xepta-resinex-mx-2.md) sustenta, como hipótesis de diseño, una equivalencia funcional muy probable con Resinex MX-2 de Jacobi; no confirma que XEPTA la reenvase.

## Datos documentados

| Campo | Valor documentado |
| --- | --- |
| Producto | XEPTA RODI RESIN 1000 ML |
| Marca | XEPTA |
| Tipo publicado por XEPTA | Resina de lecho mixto lista para usar |
| Presentación | 1000 ml |
| Uso anunciado por XEPTA | Retener sustancias que la membrana de ósmosis no haya eliminado y producir agua desmineralizada |

XEPTA declara una capacidad mínima de retención de **0,68 eq/L** para catión y **0,48 eq/L** para anión. No publica composición, grado de pureza, relación catión/anión ni instrucciones de enjuague.

## Valores de referencia para el diseño

| Parámetro | Valor de referencia Resinex MX-2 | Estado para XEPTA RODI RESIN |
| --- | --- | --- |
| Componente catiónico | Resinex K-8 H, aproximadamente 40 % en volumen | No publicado por XEPTA |
| Componente aniónico | Resinex A-4 OH, aproximadamente 60 % en volumen | No publicado por XEPTA |
| Relación catión/anión | 1:1,5 en volumen | No publicada por XEPTA |
| Forma iónica | H⁺/OH⁻ | No publicada por XEPTA |
| Tipo de resina aniónica | Base fuerte, Type I | No publicado por XEPTA |
| Capacidad catiónica mínima | 0,68 eq/L | Declarada por XEPTA |
| Capacidad aniónica mínima | 0,48 eq/L | Declarada por XEPTA |
| Tamaño de perla | 0,42–1,25 mm | No publicado por XEPTA |
| Densidad aparente | 740 kg/m³ | Referencia orientativa, no criterio de aceptación |
| Caudal de servicio | 8–40 BV/h | Referencia de MX-2, no validación de las T33 |

La tabla conserva los valores necesarios para diseñar y contrastar la resina. Su comparación, las premisas y los límites de la hipótesis permanecen desarrollados únicamente en la investigación enlazada arriba.

## Comparación con las alternativas observadas

| Producto | Presentación catalogada | Evaluación para Veril |
| --- | --- | --- |
| XEPTA RODI RESIN | 1000 ml | Opción seleccionada por formato, uso específico RO/DI y evidencia técnica disponible |
| ARKA myAqua | 300 ml con cartucho | Alternativa si se prioriza una formulación con indicador, asumiendo un formato menos adecuado para rellenar dos T33 |
| AF DI RESIN | 1000 ml | Alternativa de formato comparable; composición pendiente de contraste |
| TRITON DI | 1000 ml | Alternativa de formato comparable; composición pendiente de contraste |

La selección no constituye una prueba de superioridad química frente a las alternativas. Se basa en el tipo de producto anunciado, el formato, la evidencia técnica disponible y la necesidad de alimentar dos carcasas rellenables.

## Criterios de uso y aceptación

- Confirmar que el envase recibido identifica XEPTA RODI RESIN y conserva la resina húmeda y sin contaminación visible
- Confirmar la capacidad útil de cada carcasa T33 antes de repartir el contenido
- Cargar la resina sin mezclarla con carbón, bolas mineralizadoras ni otros medios
- Instalar las dos carcasas en serie después del permeado del RO y antes de cualquier remineralizador
- Enjuagar y desechar el agua inicial según las instrucciones del envase o del fabricante
- Medir el TDS o la conductividad antes del DI, entre las carcasas y a la salida
- Utilizar la lectura entre carcasas para identificar cuándo la primera carga empieza a agotarse
- Sustituir o reorganizar la resina según las mediciones, no según un calendario fijo
- No aceptar el agua para ATO o preparación de agua salada hasta comprobar una salida estable y coherente
- Registrar el volumen de resina realmente cargado, el TDS indicado en los tres puntos y el volumen de agua producido entre cambios de resina
- Tratar la densidad aparente de 740 kg/m³ solo como posible indicio físico de compatibilidad, nunca como identificación de OEM o aceptación de calidad

## Fuente y límites

- [Página oficial de XEPTA RODI Resin](https://shop.xepta-reef.com/es/resinas/86-xepta-po4-out-resin.html)
- [Descripción comercial adicional de XEPTA RODI Resin](https://todozoas.es/products/xepta-rodi-resin)

La URL oficial conserva el slug y una imagen con el nombre `po4-out-resin`, pero el título, los metadatos estructurados y la descripción del contenido identifican el producto como XEPTA RODI Resin. Las fichas consultadas no sustituyen a la etiqueta, la ficha técnica ni las instrucciones del envase que llegue a Veril. La resina queda seleccionada para el diseño, no confirmada como comprada, recibida, cargada ni validada en funcionamiento.
