RicardoJBarrios/acuario-veril/01_verilpedia/04_hardware/seachem-algae-scraper-31cm/seachem-algae-scraper-31cm.md

# Seachem Algae Scraper 31 cm

## Identificación declarada

| Campo | Dato |
| --- | --- |
| Marca | Seachem |
| Producto | Algae Scraper |
| Variante | 12 pulgadas / 31 cm |
| Tipo | Rascador manual para cristales de acuario |

## Características declaradas

Seachem describe un rascador 3 en 1 con cuchilla metálica, cuchilla plástica y
almohadilla suave retráctiles. La marca lo declara apto para acuarios de cristal
y acrílico, flotante y utilizable en agua dulce o salada. La cuchilla metálica
solo se utilizará sobre cristal; el propio fabricante advierte que raya el
acrílico.

Estas son especificaciones del fabricante, no una prueba de uso en Veril. La
limpieza deberá evitar arena o partículas atrapadas y no interferirá con la
silicona ni el hardscape.

## Estado y pendientes

La ficha identifica el modelo expuesto en el catálogo; la presencia física, el
estado de las cuchillas y su uso en Veril siguen pendientes de una operación.

## Fuentes

- [Seachem: Algae Scraper](https://www.seachem.com/algae-scraper.php)
