RicardoJBarrios/acuario-veril/01_verilpedia/04_hardware/xgb-830/xgb-830.md

# XGB-830

## Identificación declarada

| Campo | Dato |
| --- | --- |
| Modelo observado | XGB-830 |
| Alimentación indicada | 220 V / 50 Hz |
| Potencia indicada | 30 W |
| Caudal máximo indicado | 2.000 L/h |
| Altura máxima indicada | 1,5 m |

Los datos proceden de la etiqueta y las instrucciones fotografiadas de la
unidad. Fabricante, curva de caudal, conexiones, compatibilidad con agua salada
y protecciones frente a funcionamiento en seco no han quedado identificados.

## Aplicación delimitada en Veril

Se reserva para limpieza y trasvases puntuales. No se considera bomba de
retorno permanente ni bomba de movimiento del display. El caudal y la altura
son valores declarados y no equivalen a rendimiento medido en una instalación.

## Documentación conservada

Las fotografías originales del etiquetado e instrucciones se conservan en
`manual-original/`. Cualquier transcripción o traducción futura será auxiliar;
prevalecen la etiqueta y las instrucciones originales de la unidad.

## Pendientes

- Confirmar fabricante, conectores y límites de inmersión.
- Comprobar el estado de cable, carcasa y accesorios antes de cada uso.
- Registrar cada uso de trasvase como una operación fechada.
