RicardoJBarrios/acuario-veril/01_verilpedia/04_hardware/di-ro/carcasas-t33.md

# Carcasas T33 Frefgikty

## Identificación declarada

| Campo | Valor documentado |
| --- | --- |
| Marca | Frefgikty |
| Tipo | Carcasa transparente para filtro de agua T33 |
| Cantidad anunciada | Dos piezas según el título del producto |
| Conexiones | Conexión rápida de 1/4 pulgadas |
| Material declarado | ABS |
| Longitud aproximada | 25,4 cm |
| País de origen declarado | China |
| ASIN | B0CJYFRFN3 |

El anuncio también menciona un contenido de paquete descrito como “1 prefiltración doméstica”, por lo que la cantidad y los accesorios deben comprobarse al recibir el pedido. Las imágenes comerciales muestran dos carcasas, pero no sustituyen al inventario físico.

Como referencia de la familia comercial T33, una ficha técnica distribuida por Fresh Water Systems describe formatos de 10 pulgadas, conexiones rápidas de 1/4 pulgadas, temperatura de funcionamiento de 4,4 a 40 °C, presión máxima de 8,6 bar y caudal nominal de 4 l/min. Estos datos corresponden a esa familia de filtros y no se atribuyen automáticamente a las carcasas Frefgikty, que deberán verificarse en su etiqueta o documentación.

## Aplicación prevista

Se prevé utilizar las dos carcasas en serie como etapa DI posterior al permeado del RO6CB. El anuncio permite rellenarlas con distintos medios, entre ellos resina, pero no identifica la resina que se instalará en Veril.

No se documenta todavía la capacidad, el volumen útil, la presión máxima, el tipo de cartucho interno ni la compatibilidad química del material con la resina concreta. Esos datos deberán verificarse en la pieza y en su documentación.

## Fuente

- [Anuncio de las carcasas T33 en Amazon](https://www.amazon.es/dp/B0CJYFRFN3)
- [Ficha técnica de referencia para filtros T33/K33](https://assets.freshwatersystems.com/image/upload/s--ESFcwQ0c--/14400906b07f8646d67e1082e3fdd817e8d36ab9.pdf)
