RicardoJBarrios/acuario-veril/01_verilpedia/04_hardware/di-ro/monitor-tds-hm-digital-trm-1.md

# Monitor TDS HM Digital TRM-1

## Identificación declarada

| Campo | Valor documentado |
| --- | --- |
| Marca | HM Digital |
| Modelo | TRM-1 |
| Función | Monitor TDS de tres puntos |
| Conexión hidráulica anunciada | Ajustes en T de 1/4 pulgadas |
| Alimentación declarada | Baterías |
| ASIN | B00GKLD5QY |

La ficha técnica oficial de HM Digital concreta el rango en 0–9990 ppm, la precisión declarada en ±2 %, la resolución en 1 ppm hasta 999 ppm y 10 ppm desde 1000 ppm, tres sondas con conectores en T de 1/4 pulgadas, apagado automático tras diez minutos sin uso y dos pilas de botón de 1,5 V tipo LR44 o equivalente. También indica calibración de fábrica con una disolución de NaCl de 342 ppm y una autonomía aproximada de 1000 horas de uso continuo.

El anuncio describe el TRM-1 como un monitor con tres puntos de contacto para observar el agua en sistemas RO/DI o en varios puntos de un sistema de filtración. La tabla comercial contiene campos incoherentes sobre conectividad y dispositivos compatibles; no se consideran especificaciones funcionales del monitor.

## Aplicación prevista

Se prevé medir el agua de entrada al DI, el punto intermedio entre las dos carcasas T33 y la salida final. La correspondencia de cada línea, la instalación de las sondas y la lectura real deberán comprobarse al recibirlo.

El TDS indicado por este equipo no identifica por sí solo todos los contaminantes ni prueba la calidad microbiológica del agua. Servirá como indicador operativo junto con el estado de la resina y, cuando corresponda, mediciones de conductividad.

La conversión del equipo está referida a NaCl con factor medio 0,5. Por ello, las lecturas se registrarán como TDS indicado por el TRM-1 y no como una concentración universal de sólidos disueltos. La calibración, la temperatura y la correspondencia de cada sonda deberán mantenerse constantes al comparar los tres puntos.

## Fuente

- [Monitor HM Digital TRM-1 en Amazon](https://www.amazon.es/dp/B00GKLD5QY)
- [Ficha técnica oficial del HM Digital TRM-1](https://hmdigital.com/trm-1/)
