RicardoJBarrios/acuario-veril/01_verilpedia/04_hardware/di-ro/tubo-conexiones-huaziz.md

# Kit de tubo y conexiones HUAZIZ

## Identificación declarada

| Campo | Valor documentado |
| --- | --- |
| Marca | HUAZIZ |
| Conjunto | Juego de conexión universal |
| Tubo | Diez metros, blanco, 1/4 pulgadas |
| Material declarado | Material apto para uso alimentario |
| Espesor nominal de pared | 0,0635 pulgadas según el anuncio |
| Peso declarado | 310 g |
| Accesorios declarados | Conectores rectos, codos, T, Y, válvulas de cierre y cortatubos |

El usuario identifica este pedido como el primer kit, con diez metros de tubo blanco y los conectores. El anuncio presenta cantidades y denominaciones que deben cotejarse con el paquete; no se registra como inventario confirmado.

## Aplicación prevista

El tubo se utilizará para interconectar el RO6CB, las carcasas T33, el monitor TDS, el manómetro, el desagüe y los depósitos cuando se defina el montaje. La compatibilidad de cada conexión, el corte limpio y la retención del tubo se comprobarán antes de presurizar.

La longitud disponible no implica que todo el tubo deba instalarse. Se reservará la longitud necesaria para inspección, mantenimiento y aislamiento de cada componente.

## Fuente

- Información del producto HUAZIZ facilitada por el usuario; no se ha facilitado un ASIN o URL inequívoco
