RicardoJBarrios/acuario-veril/01_verilpedia/04_hardware/di-ro/fuentes/2026-09-21-investigacion-xepta-resinex-mx-2.md

# Investigación: XEPTA RODI Resin y Resinex MX-2

## Alcance y conclusión

Esta investigación compara las especificaciones publicadas de XEPTA RODI Resin con Resinex MX-2 de Jacobi. La hipótesis resultante es que XEPTA es **muy probablemente** Resinex MX-2 reenvasada o una resina de composición y comportamiento funcionalmente equivalentes.

La identidad OEM no está confirmada. No se ha localizado una declaración de XEPTA o Jacobi, una SDS/TDS de XEPTA, un EAN confirmado ni trazabilidad de lote que vincule ambas marcas. Por ello Veril adopta MX-2 como **equivalencia funcional de diseño**, no como identidad química demostrada del producto XEPTA.

## Evidencia y comparación

| Parámetro | XEPTA RODI Resin | Resinex MX-2 | Lectura para Veril |
| --- | --- | --- | --- |
| Tipo | Lecho mixto listo para usar, según distribuidores | Lecho mixto listo para usar | Coincidencia de categoría y aplicación |
| Uso | Agua desmineralizada después de RO | Agua completamente desmineralizada, incluido pulido post-RO | Compatible con el DI previsto |
| Capacidad catiónica mínima | 0,68 eq/L, declarada por XEPTA | 0,68 eq/L | Coincidencia exacta |
| Capacidad aniónica mínima | 0,48 eq/L, declarada por XEPTA | 0,48 eq/L | Coincidencia exacta |
| Componentes | No publicados por XEPTA | Resinex K-8 H + Resinex A-4 OH | No confirmado para XEPTA |
| Relación volumétrica | No publicada por XEPTA | 1:1,5, aproximadamente 40 % catiónica y 60 % aniónica | Referencia funcional de diseño |
| Forma iónica | No publicada por XEPTA | H⁺/OH⁻ | No confirmado para XEPTA |
| Grupo aniónico | No publicado por XEPTA | Base fuerte Type I | Si la equivalencia es correcta, sustenta la eliminación de sílice |
| Tamaño de perla | No publicado por XEPTA | 0,42–1,25 mm | No confirmado para XEPTA |
| Densidad aparente | No publicada por XEPTA | 740 kg/m³ | Comprobación física solo orientativa |
| Caudal de servicio | No publicado por XEPTA | 8–40 BV/h | Referencia de MX-2, no validación de las T33 |
| Aplicaciones | RO/DI, según distribuidores | Cartuchos de lecho mixto, laboratorio y pulido tras desmineralización | Compatible con el propósito previsto |

La coincidencia simultánea de las dos capacidades, el tipo de resina y la finalidad comercial hacen poco probable una casualidad. Aun así, esa coincidencia no permite prometer el contenido del envase recibido ni asumir que sus tolerancias, granulometría, capacidad útil o rendimiento sean idénticos a los de MX-2.

## Consecuencias de diseño para Veril

T33 designa normalmente un formato exterior de aproximadamente 10 × 2 pulgadas, no una capacidad de medio estandarizada. Hay cartuchos rellenables de ese formato documentados entre 0,2 L y 0,3 L. Ninguno confirma el volumen útil de las carcasas Frefgikty. Se adopta por tanto **0,3 L por carcasa solo como supuesto preliminar de diseño**, pendiente de medición física.

La membrana del RO6CB se anuncia con 50 GPD y aproximadamente 180 L/día, equivalentes a unos 7,5 L/h nominales. Con 0,3 L efectivos, cada T33 trabajaría a aproximadamente **25 BV/h**, dentro del intervalo 8–40 BV/h publicado para MX-2. Al estar en serie, ambas carcasas reciben el mismo caudal: no debe calcularse el sistema como un lecho único de 0,6 L para rebajar artificialmente los BV/h. La comparación sigue siendo orientativa porque el caudal real de la ósmosis, el volumen cargado y el comportamiento hidráulico del conjunto no se han medido.

La hipótesis también explica por qué se prefiere medir el sistema antes que depender de un indicador de color. Se usarán las lecturas TDS antes de DI, entre DI1 y DI2 y a la salida final. La ausencia práctica de aporte de silicato, el agotamiento de DI1 y la aceptación del agua para ATO o preparación de agua salada se determinarán por esas mediciones y no por la equivalencia documental.

## Límites y próxima evidencia

- Confirmar en el envase recibido la referencia, estado físico, lote, instrucciones y masa neta si se declara. Una masa cercana a 740 g por litro de resina húmeda sería solo un indicio adicional, no una identificación OEM.
- Medir el volumen realmente cargado en cada T33 antes de mantener o descartar el supuesto preliminar de 0,3 L, además del TDS indicado en los tres puntos y el volumen producido entre sustituciones de resina.
- Comprobar estanqueidad, orientación, ausencia de canalización y calidad final del agua antes de usarla en Veril.
- Conservar cualquier SDS, TDS, etiqueta, EAN o comunicación de Xepta que nombre a Jacobi, Resinex, K-8 H o A-4 OH; esa evidencia podría confirmar o refutar la hipótesis.

## Fuentes

- [Página oficial de XEPTA RODI Resin](https://shop.xepta-reef.com/es/resinas/86-xepta-po4-out-resin.html): declara resina de lecho mixto lista para usar, destinada a producir agua desmineralizada, con capacidad mínima de 0,68 eq/L para catión y 0,48 eq/L para anión. La URL y la imagen conservan el texto `po4-out-resin`, mientras que título, metadatos estructurados y descripción identifican el producto como XEPTA RODI Resin.
- [Descripción comercial adicional de XEPTA RODI Resin](https://todozoas.es/products/xepta-rodi-resin).
- [Ficha técnica de Resinex MX-2, identificada como Jacobi `JACOBI-TDS-RESINEX-MX2-A4-ENG-C0923`](https://depuracionagua.com/web/content/14675?download=true): capacidades, composición, propiedades y condiciones de diseño de MX-2.
- [Jacobi Resins: K-8 H con A-4 OH para desmineralización y pulido](https://resins.jacobi.net/industrial-water-treatment/): corroboración del par de resinas en la documentación del fabricante.
- [T33 Inline Filter Cartridge](https://twdcindustrial.com/product_d.php?id=428&lang=en&tb=1): formato exterior declarado de 2 pulgadas de diámetro por 10 pulgadas de longitud.
- [Ejemplo comercial de cartucho T33 rellenable de 10 × 2 pulgadas](https://de.made-in-china.com/co_hellopurewater/product_Empty-10-Refillable-Inline-Filter-Cartridge-DIY-Filter-Housing-for-Di-Resin-Reverse-Osmosis-Systems-Units_ysui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): capacidad declarada de 0,2 L. No corresponde a las carcasas Frefgikty de Veril.
- Revisión de productos realizada por el usuario el 21 de septiembre de 2026: existen numerosas variantes T33 anunciadas con 0,3 L. No se aportaron enlaces ni se verifica aquí que correspondan al modelo Frefgikty.
