RicardoJBarrios/acuario-veril/aquascape/biologia.md

# Aquascape de Veril: biología

> La [dimensión de comunidad](../fichas/dimensiones/dimension-comunidad.md) define la configuración mixta, la compatibilidad y la capacidad compartida. La [dimensión espacial](../fichas/dimensiones/dimension-espacial.md) define cómo el aquascape distribuye superficies, refugios, territorios y espacio de crecimiento. Esta ficha registra la aplicación biológica prevista para Veril.

## Alcance de esta ficha

La fauna y los organismos descritos aquí son opcionales mientras no exista una ficha específica que confirme su incorporación. La configuración física no implica que deban incorporarse peces, organismos sésiles, invertebrados, microfauna ni un equipo de limpieza.

La elección concreta de especies, cantidades, fechas y parámetros pertenece a sus fichas de biología y a la documentación operativa correspondiente. Esta ficha conserva las decisiones que afectan directamente a la ocupación y evolución del aquascape.

## Relación entre comunidad y aquascape

El aquascape disponible condiciona la biología que puede plantearse: volumen, geometría de la roca, superficie de sustrato, flujo, luz, refugios y acceso. La selección biológica partirá de esas condiciones reales, de acuerdo con la [dimensión de comunidad](../fichas/dimensiones/dimension-comunidad.md).

La biología modificará el aquascape con el tiempo. La colonización y el crecimiento ocuparán superficies, cambiarán la rugosidad y las sombras, alterarán las rutas de flujo y aumentarán la carga biológica y las necesidades de mantenimiento.

Si una población deja de conservar las funciones físicas del diseño, el aspecto afectado se revisará en su documento propietario:

- La [roca](roca.md) para la geometría, los refugios y los pasos
- El [sustrato](sustrato.md) para la playa, el canal y el sustrato libre
- La [hidrodinámica](hidrodinamica.md) para las rutas de renovación
- La [iluminación](iluminacion.md) para la cobertura y las sombras

## Capacidad biológica y medios complementarios

Si el montaje o una modificación del hardscape conlleva una pérdida sustancial de superficie colonizable o de capacidad biológica, el compartimento técnico podrá compensarla mediante roca viva, BactoFlex, canutillos cerámicos u otro medio biológico equivalente.

Estos medios no forman parte de la configuración base. Su posible incorporación constituirá una decisión independiente y deberá documentarse en relación con la [dimensión de procesamiento](../fichas/dimensiones/dimension-procesamiento.md), sin atribuir automáticamente su función al aquascape.

## Pared viva

La posible incorporación de una pared viva se estudiará como un elemento secundario del aquascape. No se considera una función necesaria ni se establece una superficie concreta que deba colonizarse.

Su viabilidad se comprobará durante la maduración, observando si la colonización vertical aporta valor sin reducir el acceso, la limpieza, la observación o la seguridad de los elementos funcionales. El cristal trasero, el cristal visible del compartimento técnico y las microislas podrán permanecer libres si la colonización no resulta compatible con esas condiciones.

No se fija una lista previa de organismos ni se presupone que deba promoverse una cobertura uniforme. Cualquier organismo incrustante o colonial se valorará según su compatibilidad biológica y la capacidad de contener su crecimiento.

La pared deberá conservar el canal, el espacio negativo y los elementos funcionales. Las colonias expansivas no deberán:

- Alcanzar la roca principal y crear puentes no previstos
- Cerrar el canal o los espacios negativos
- Interferir con juntas, rebosaderos, ranuras, sensores y accesos
- Impedir la limpieza o la inspección del compartimento técnico

## Población y hábitats

La elección de cada organismo se realizará relacionando sus necesidades con las condiciones documentadas en:

- [Roca](roca.md)
- [Sustrato](sustrato.md)
- [Hidrodinámica](hidrodinamica.md)
- [Iluminación](iluminacion.md)

Se considerarán como mínimo:

- Tamaño adulto y comportamiento
- Alimentación y carga biológica
- Necesidad de luz, flujo, refugio o sustrato
- Espacio disponible y posibilidad de observación
- Trayectoria de crecimiento y capacidad de ocupar superficies vecinas
- Capacidad de contención y mantenimiento

La población no deberá cerrar pasos, cubrir el canal, bloquear elementos técnicos ni consumir todo el espacio negativo. La decisión de incorporar cada organismo deberá quedar en su ficha propietaria o en el plan operativo correspondiente.

## Compatibilidad entre corales fotosintéticos

Los corales fotosintéticos con necesidades de PPFD diferentes no se colocarán juntos en la misma zona funcional del aquascape. La convivencia dentro del mismo display no implica que deban compartir una misma superficie, terraza o agrupación.

La colocación se decidirá después de disponer del [mapa de PPFD](iluminacion.md) y de consultar las necesidades documentadas de cada organismo. Cuando los requisitos sean incompatibles, se utilizarán zonas separadas o se descartará la combinación si no existe una distribución espacial viable.

Esta regla aplica a la disposición concreta de Veril. No constituye una clasificación universal de especies ni sustituye la ficha individual de cada coral.

## Potencial de interacción agresiva

Además de las necesidades de PPFD, cada coral se evaluará por su potencial de interacción agresiva con los organismos próximos. En esta documentación, el criterio incluye:

- Guerra química o liberación de compuestos que puedan afectar a otros organismos
- Tentáculos de barrido, tentáculos urticantes o estructuras equivalentes
- Filamentos mesentéricos u otros mecanismos de contacto agresivo
- Crecimiento invasivo, expansión rápida o capacidad de ocupar superficies vecinas
- Contacto físico, sombreado o bloqueo de espacio producido durante el crecimiento

Los corales con mecanismos de agresión incompatibles no se colocarán juntos ni se considerarán compatibles solo porque sus necesidades de PPFD sean similares. La separación deberá considerar la trayectoria previsible de crecimiento y no únicamente la distancia inicial entre colonias.

La ficha individual de cada coral deberá documentar, cuando exista información suficiente, su potencial de interacción, la distancia de seguridad necesaria y las medidas de contención previstas. Si no puede garantizarse una separación funcional dentro del aquascape, la incorporación se descartará o se revisará la composición espacial.

## Disposición según crecimiento y restricciones

Los corales se dispondrán teniendo en cuenta su crecimiento previsible, sus preferencias de ubicación y las restricciones que puedan imponer sobre las superficies, los espacios negativos, la luz, el flujo y los organismos próximos.

Los corales con crecimiento muy expansivo o con capacidad elevada de ocupar superficies vecinas se intentarán:

- Situar en islas separadas de la estructura principal
- Rodear de espacio negativo suficiente
- Separar mediante barreras físicas cuando la geometría lo permita
- Mantener alejados de juntas, rebosaderos, ranuras, sensores y accesos
- Colocar en superficies cuya expansión pueda observarse y controlarse

Las islas y barreras no garantizan por sí solas la contención. Su eficacia deberá revisarse durante el crecimiento, porque un coral puede superar el espacio previsto, extenderse por contacto o modificar las condiciones de los organismos próximos.

## Ubicación según flujo y alimentación

Por las exigencias de alimentación y el nivel de maduración necesario, se prevé que las primeras incorporaciones sean principalmente corales y organismos coraliformes fotosintéticos. Esta secuencia no limita el criterio de diseño: cualquier coral, gorgonia, anémona u otro organismo sésil que se estudie incorporar deberá evaluarse según sus necesidades de luz, flujo, alimentación, espacio, crecimiento e interacción.

La colocación tendrá en cuenta el flujo disponible en cada zona y su relación con el intercambio, la alimentación ocasional, la eliminación de residuos y la integridad de los tejidos.

Las zonas destinadas a corales y coraliformes deberán permitir:

- Renovación de agua suficiente alrededor de los tejidos
- Movimiento compatible con la extensión y la integridad de los pólipos
- Llegada de partículas o alimento cuando la alimentación directa proceda
- Captura del alimento sin dispersarlo o retirarlo antes de que pueda aprovecharse
- Observación y ajuste de la respuesta del organismo
- Retirada de restos sin provocar una acumulación incontrolable

Los organismos que dependan en mayor medida de la alimentación directa, si finalmente se incorporan, requerirán además una evaluación específica de llegada, captura y distribución del alimento.

La [hidrodinámica](hidrodinamica.md) documenta las rutas y gradientes de flujo. La alimentación concreta, la frecuencia y la carga resultante deberán definirse en la ficha del organismo y en el plan de mantenimiento correspondiente.

## Evolución y criterios de aceptación

La comunidad madura tendrá una distribución distinta del montaje inicial. La colonización vertical aportará textura al fondo y los organismos que se incorporen ocuparán progresivamente las superficies compatibles.

La evolución será aceptable mientras conserve:

- Colonización eventual contenible y compatible con el mantenimiento
- Población compatible con el volumen y el mantenimiento disponible
- Espacio libre para circulación, observación y acceso
- Elementos técnicos despejados
- Organismos asociados a condiciones adecuadas de luz, flujo y sustrato
- Capacidad de evolución sin perder la estructura funcional

Si el crecimiento altera de forma relevante el espacio disponible, la carga biológica o las condiciones físicas, la decisión se documentará en la ficha propietaria del aspecto afectado.

## Fuentes biológicas

- [Ficha de algas coralinas](../fichas/biologia/algas-coralinas.md)
- [Sección de microfauna marina](../fichas/biologia/README.md#microfauna-marina)
