RicardoJBarrios/acuario-veril/aquascape/iluminacion.md

# Aquascape de Veril: iluminación

> La [dimensión de iluminación](../fichas/dimensiones/dimension-iluminacion.md) define el régimen de espectro, intensidad y tiempo. La [dimensión espacial](../fichas/dimensiones/dimension-espacial.md) define la relación entre relieve, superficies, gradientes y sombras. La [dimensión de comunidad](../fichas/dimensiones/dimension-comunidad.md) establece que la iluminación debe ser compatible con los organismos previstos. Esta ficha registra la implementación concreta de Veril.

## Luminaria y soporte

La luminaria prevista es la [AI Prime 16HD Reef](../fichas/hardware/ai-prime-16hd-reef/ai-prime-16hd-reef.md), suspendida mediante su kit para colgar.

Se situará ligeramente desplazada hacia la derecha para ofrecer la mejor cobertura posible del hardscape, sin tomar como referencia obligatoria el centro geométrico del display de aproximadamente **60 cm**.

La referencia actual es de **250 mm** entre la cara inferior de la luminaria y el agua. La altura real se comprobará una vez instalado el conjunto.

La luminaria contará con un *shade* frontal realizado mediante impresión 3D para reducir el reflejo sobre el cristal delantero y evitar el deslumbramiento. Los laterales y la parte trasera quedarán libres para conservar la ventilación y la dispersión lateral de la luz.

## Cobertura prevista

La cobertura deberá alcanzar:

- La masa principal
- La masa secundaria
- Las islas
- Las superficies de sustrato que formen parte de la composición visual

La zona técnica lateral no forma parte de la superficie principal de iluminación.

La geometría de las masas iluminadas se documenta en [roca](roca.md). La distribución del sustrato se documenta en [sustrato](sustrato.md).

## Gradiente y sombras

El conjunto conservará una distribución no uniforme:

- Mayor intensidad en las superficies altas y expuestas
- Intensidad intermedia en terrazas, caras abiertas e islas
- Luz baja o filtrada en caras laterales y superficies inferiores
- Sombras estables en refugios, grietas, huecos y espacios bajo voladizos

La distribución final dependerá de la luminaria, la altura, el agua, la orientación y la geometría de la estructura. La [dimensión espacial](../fichas/dimensiones/dimension-espacial.md) establece el criterio general de utilizar gradientes accesibles y funcionales, no una distribución uniforme obligatoria.

## Medición y clasificación de zonas por PPFD

Se realizará un mapa de PPFD en el acuario una vez instalada la luminaria y definida la geometría operativa del aquascape. La medición servirá para clasificar las diferentes zonas de luz disponibles en el display y no se sustituirá por estimaciones basadas únicamente en la posición o la altura de la luminaria.

El registro deberá conservar, como mínimo:

- Condiciones de la medición
- Puntos o zonas muestreadas
- Valor de PPFD observado en cada punto
- Altura o posición de la superficie medida
- Relación entre cada zona medida y la roca, el sustrato o los espacios previstos
- Fecha y equipo utilizado

El resultado se utilizará como mapa de referencia para asignar los organismos fotosintéticos a zonas compatibles. Los límites de PPFD no se fijan en esta ficha antes de disponer de la medición y de las necesidades documentadas de cada organismo.

## Criterios de aceptación

La configuración deberá conservar:

- Cobertura suficiente de todas las masas del hardscape
- Gradientes y sombras utilizables
- Lectura visual del relieve sin un foco estrecho dominante
- Acceso para mantenimiento y retirada de la luminaria
- Ausencia de luz directa innecesaria sobre la zona técnica
- Compatibilidad entre el *shade*, la ventilación y la distribución de luz
- Relación observable entre la cobertura y las superficies que se decidan ocupar
- Mapa de PPFD disponible para clasificar las zonas antes de colocar corales fotosintéticos

La intensidad y el tiempo de encendido no se fijan en esta ficha. Su incorporación progresiva pertenece al [plan de maduración](../ciclado/planes/plan-maduracion.md).

## Relaciones con otras decisiones de Veril

- La [roca](roca.md) define la altura, la orientación y las superficies que deben recibir luz
- El [sustrato](sustrato.md) define las superficies inferiores y la playa que forman parte de la composición
- La [hidrodinámica](hidrodinamica.md) define el movimiento del agua que modifica la distribución efectiva de luz
- La [biología](biologia.md) documenta los organismos que ocuparán las zonas iluminadas

## Fuente de diseño

- [Ficha de la AI Prime 16HD Reef](../fichas/hardware/ai-prime-16hd-reef/ai-prime-16hd-reef.md)
