RicardoJBarrios/acuario-veril/aquascape/roca.md

# Aquascape de Veril: roca

> La [dimensión espacial](../fichas/dimensiones/dimension-espacial.md) define los criterios generales de estructura, espacio negativo, refugios y accesibilidad. Esta ficha registra su aplicación concreta en Veril.

## Decisión de composición

La formación rocosa tendrá su mayor altura y complejidad en la zona posterior derecha, junto al compartimento técnico, y descenderá y se fragmentará hacia el centro y la izquierda.

La composición se organizará mediante:

- Una masa principal posterior derecha
- Una masa secundaria separada desde la zona abierta
- Islas independientes de menor volumen en la zona frontal o lateral
- Una playa y un canal visualmente reconocibles
- Espacios abiertos entre las masas

La forma final podrá variar según las piezas disponibles, siempre que conserve la relación de volúmenes y la dirección general de la composición.

Representación conceptual frontal de las masas de roca

Representación conceptual superior de las masas de roca

Las imágenes son diagramas de la idea general y no deben calcarse. La capa de color ayuda a leer la estructura:

- **Rojo:** Masa principal, con la mayor altura y volumen
- **Amarillo:** Masa secundaria separada, que equilibra el volumen principal desde la zona abierta
- **Verde:** Islas separadas, de menor volumen y distribuidas en el espacio frontal o lateral

Los colores no representan especies, materiales, piezas concretas ni límites exactos. Esta ficha no fija medidas ni porcentajes.

## Material y selección de piezas

La roca será suministrada por el proveedor y se considera inerte. Su marca y composición mineral concreta no están identificadas; presenta una coloración violeta que simula visualmente una superficie con coralina.

La selección de las piezas dependerá de:

- Estabilidad y seguridad del apoyo
- Porosidad y volumen real
- Posibilidad de formar la composición prevista
- Ausencia de puntos de presión peligrosos sobre el vidrio
- Posibilidad de inspección, fijación y retirada

La relación entre superficie inicialmente inerte, colonización y maduración pertenece a la [dimensión de procesamiento](../fichas/dimensiones/dimension-procesamiento.md) y a la documentación de [biología](biologia.md).

## Geometría prevista

### Masa principal

La masa principal ocupará la zona posterior derecha, concentrará la mayor altura y descenderá hacia el centro mediante terrazas, volúmenes escalonados o una transición equivalente.

No formará una pared maciza contra el cristal. Deberá conservar profundidad visual, superficies diferenciadas y una relación clara con la zona abierta.

### Masa secundaria e islas

La masa secundaria quedará separada de la principal y equilibrará el volumen desde la zona abierta. Las islas serán fragmentos independientes, de menor presencia y distribuidos principalmente en la zona frontal o lateral.

La composición no deberá convertirse en una montaña compacta ni en un conjunto de piezas dispersas sin relación visual.

### Geometría funcional

La estructura incorporará, según las piezas disponibles:

- Un refugio profundo
- Un paso atravesable
- Grietas comunicadas
- Voladizos y espacios inferiores
- Superficies horizontales e inclinadas
- Zonas expuestas y protegidas

La geometría deberá conservar la playa, el canal y los espacios negativos previstos. La relación con el sustrato se documenta en [sustrato](sustrato.md).

## Estabilidad y acceso

Los apoyos principales repartirán la carga y no dependerán de que el sustrato permanezca bajo ellos. Las piezas estructurales se fijarán entre sí cuando sea necesario y no crearán puntos de presión peligrosos sobre el vidrio.

La composición deberá ser estable y accesible desde las vistas principales, no solo desde el frente. También deberá permitir retirar o modificar piezas sin desmontar toda la estructura cuando la unión y la estabilidad lo permitan.

Antes de llenar el sistema se comprobará:

- Estabilidad de cada masa y de sus uniones
- Ausencia de desplazamientos durante la manipulación prevista
- Separación suficiente respecto a los cristales para su limpieza
- Conservación de entradas, retornos, sensores y accesos
- Ausencia de apoyos puntuales o contacto peligroso con el vidrio

La [dimensión física](../fichas/dimensiones/dimension-fisica.md) establece los límites de la urna y del compartimento técnico. La [dimensión espacial](../fichas/dimensiones/dimension-espacial.md) establece los criterios generales de estabilidad, acceso y evolución.

## Relaciones con otras decisiones de Veril

- El [sustrato](sustrato.md) define la superficie alrededor de la estructura, la playa y el canal
- La [hidrodinámica](hidrodinamica.md) comprueba las rutas de flujo alrededor y debajo de las masas
- La [iluminación](iluminacion.md) comprueba la cobertura y los gradientes sobre las superficies
- La [biología](biologia.md) documenta la colonización posterior y el crecimiento

## Fuentes de diseño

- [Display de la urna](../fichas/hardware/urna/display.md)
- [Técnica de la urna](../fichas/hardware/urna/tecnica.md)
