RicardoJBarrios/acuario-veril/aquascape/sustrato.md

# Aquascape de Veril: sustrato

> La [dimensión espacial](../fichas/dimensiones/dimension-espacial.md) define la función del sustrato, el espacio negativo y la relación entre playa, canal y estructura. Esta ficha registra la selección y distribución previstas para Veril.

## Producto previsto

El sustrato previsto es **Aquaforest AF Bio Sand**. La información de composición, activación, preparación, límites y riesgos está documentada en la [ficha de AF Bio Sand](../fichas/productos/af-bio-sand.md).

La selección del producto no implica que toda su superficie deba mantenerse con una profundidad uniforme ni que pueda utilizarse como apoyo estructural de la roca.

## Profundidad

La intención es mantener una profundidad general de **2–3 cm**. El formato de **7,5 kg** debería ser suficiente para la capa general y para una zona localizada algo más profunda.

La profundidad final podrá adaptarse a la superficie real que quede libre después de disponer la roca. Puede contemplarse una zona localizada de **4–5 cm** si la configuración del sustrato lo permite. La necesidad concreta de una profundidad distinta se valorará en [biología](biologia.md).

## Granulometría y comportamiento previsto

La granulometría de referencia es **AF Bio Sand de 1–2 mm**.

El sustrato deberá:

- Conservar la forma de la playa y del canal
- Evitar nubes persistentes durante el movimiento normal del agua
- Evitar acumulaciones problemáticas
- No invadir las zonas técnicas
- Mantenerse compatible con los organismos que finalmente se decidan

La relación entre granulometría, movimiento del agua y desplazamiento se comprueba en [hidrodinámica](hidrodinamica.md). La explicación general de la función espacial del sustrato pertenece a la [dimensión espacial](../fichas/dimensiones/dimension-espacial.md).

## Playa y canal

La zona frontal conservará una playa amplia. El canal diagonal partirá del frontal centro-izquierdo y se dirigirá visualmente hacia la zona posterior.

- La playa conservará una superficie predominantemente libre
- El canal no se definirá mediante una hilera continua de piedras
- Las islas mantendrán sustrato libre a su alrededor
- No se llenará la playa con material innecesario

La relación visual buscada será:

```text
sustrato → canal → hueco → fondo
```

La geometría rocosa que limita la playa y el canal se documenta en [roca](roca.md).

## Criterios de aceptación

El sustrato deberá conservar:

- Profundidad visualmente coherente
- Playa y canal reconocibles
- Superficie accesible para observación y mantenimiento
- Ausencia de acumulaciones que alteren su función
- Compatibilidad con la roca y los organismos previstos
- Separación suficiente respecto a entradas, retornos y zona técnica

La compatibilidad biológica se desarrolla en [biología](biologia.md), y la selección del producto en la [ficha de AF Bio Sand](../fichas/productos/af-bio-sand.md).

## Fuente de la selección

- [Aquaforest: guía de productos y sustrato regular](https://aquaforest.eu/wp-content/uploads/2024/09/AF_Products-Guide_EN_WEB_241120.pdf)
