RicardoJBarrios/acuario-veril/02_configuracion/01_dimensiones/05_quimica.md

# Veril: química

> La [dimensión química](../../01_verilpedia/01_dimensiones/05_quimica.md) define cómo interpretar composición, relaciones, tendencias y estabilidad. Esta ficha registra la aplicación prevista en Veril sin repetir las fichas generales de parámetros.

## Aplicación adoptada

La química de Veril se seguirá mediante las [fichas de parámetros](../../01_verilpedia/03_parametros/README.md), con atención a la relación entre salinidad, temperatura, pH, alcalinidad, compuestos nitrogenados, nitrato, fosfato y oxígeno cuando corresponda a la fase del sistema.

La configuración integrada adopta como zona preferida del agua **25–26 °C** y como objetivo operativo normal **24,5–26,5 °C**. Entre 24,0 y 24,5 °C se considera fresca pero razonablemente normal; 23,0–24,0 °C es una excursión fría a investigar si persiste; por debajo de 23,0 °C está fuera del objetivo y por debajo de 22,0 °C requiere revisión prioritaria. Son categorías locales, no umbrales fisiológicos universales; la interpretación completa está en [Régimen térmico adoptado](../README.md#régimen-térmico-adoptado). Esta ficha conserva la interpretación de la temperatura como variable química y contexto de medición.

El agua de reposición por evaporación será agua RO/DI mediante el [ATO seleccionado](../../01_verilpedia/04_hardware/dd-h2ocean-compact-ato/dd-h2ocean-compact-ato.md), sin añadir sal: la evaporación retira agua, no sal. El llenado inicial del ciclado utilizará agua de mar filtrada con UV de Elite Reef Kanarias. El agua nueva para los cambios posteriores se preparará con RO/DI y [Aquaforest Reef Salt](../../01_verilpedia/05_productos/02_aquaforest-reef-salt/aquaforest-reef-salt.md), según el [procedimiento operativo de cambios de agua](../../03_pendientes/operacion-recurrente/cambios-agua.md), hasta alcanzar una salinidad objetivo de `S_P = 35`.

Para los cálculos de cambios de agua de Veril se toma como base nominal **75 L para el sistema completo** y **60 L para el display**. Se adopta un cambio nominal de **10 L**, aproximadamente el 13,3 % del sistema. Para prepararlo a `S_P = 35`, se parte de **unos 415 g de Reef Salt** como referencia empírica de usuarios. No es una cantidad oficial garantizada para todos los lotes; se ajustará midiendo la salinidad del agua preparada. El [procedimiento de cambios de agua](../../03_pendientes/operacion-recurrente/cambios-agua.md) atribuye las referencias y conserva sus límites.

Para la salinidad se dispone de un [refractómetro D-D The Aquarium Solution AQPR001](../../01_verilpedia/05_productos/06_dd-aquarium-solution-aqpr001/dd-aquarium-solution-aqpr001.md). Su calibración y el método de medición se registrarán antes de aceptar el agua de mar.

No se fija en esta ficha una tabla independiente de valores objetivo. Los rangos, métodos, unidades, frecuencia y límites de interpretación pertenecen a las fichas de parámetros y a los planes operativos que los utilicen.

## Agua del arranque biológico

El llenado inicial utilizó agua de mar filtrada con UV suministrada por Elite Reef Kanarias, pero el volumen efectivamente introducido no quedó medido. El registro del 5 de septiembre confundió inicialmente las capacidades nominales de dos recipientes de 30 L y uno de 20 L con el volumen trasvasado; el propietario indica que seguramente se introdujo menos. El 6 de septiembre se estimaron aproximadamente 7 L adicionales, pero no puede calcularse el total acumulado sin conocer el volumen inicial real. Estas cantidades no deben confundirse con el volumen operativo estimado de unos 75 L. Los dos bidones de 15 L —uno lleno y otro con una pequeña cantidad— permanecían fuera del sistema y no forman parte del volumen operativo. Antes de iniciar el ciclado se comprobarán la salinidad, la temperatura, el pH y la alcalinidad, y el agua se aceptará únicamente si resulta compatible con el objetivo `S_P = 35`. El propietario comunica que el equipo RO6CB llegó el 24 de septiembre de 2026; la etiqueta de la caja está documentada, pero el contenido no se ha inventariado y la unidad no se ha instalado ni aceptado. La recepción e instalación de los componentes DI, la carga de resina y la aceptación del sistema RO/DI completo siguen pendientes. El conjunto se necesitará para la reposición por evaporación y los cambios posteriores. Véase el [registro de recepción](../../04_operaciones/2026/09/2026-09-24-recepcion-equipo-ro6cb/README.md).

Antes de añadir FritzZyme 9 y Fishless Fuel, se procurará partir del objetivo operativo normal de **24,5–26,5 °C**, preferentemente 25–26 °C. Si el agua está en excursión fría (23–24 °C) o por debajo del objetivo (<23 °C), se registrarán duración y tendencia y se comprobará estabilidad antes de iniciar. El detalle de activación del AF Bio Sand, las dosis de los productos y la secuencia temporal pertenecen al [plan de ciclado](../../03_pendientes/ciclado/plan.md) y al [runbook de ciclado](../../03_pendientes/ciclado/runbook.md).

El agua de mar suministrada prepara la matriz salina, pero no inocula bacterias ni sustituye a FritzZyme 9. El agua RO/DI de reposición del ATO tampoco contiene sal y no se utilizará para preparar las cargas de Fishless Fuel.

## Justificación de la salinidad objetivo

Veril adopta una salinidad práctica objetivo de **`S_P = 35`**. Esta decisión no presenta 35 como una salinidad universalmente obligatoria, sino como el punto de consigna elegido para esta configuración.

La decisión se fundamenta en varios criterios convergentes, documentados en la [ficha general de salinidad](../../01_verilpedia/03_parametros/salinidad.md) y en la [ficha de Aquaforest Reef Salt](../../01_verilpedia/05_productos/02_aquaforest-reef-salt/aquaforest-reef-salt.md):

- `S_P = 35` se aproxima a la referencia habitual de salinidad del océano abierto y ofrece un punto de comparación claro con la química marina
- La configuración prevista es un arrecife mixto, no un sistema fish-only ni un sistema deliberadamente hiposalino
- Aquaforest considera aproximadamente 33–35 ppt un intervalo adecuado para acuarios marinos y recomienda alrededor de 35 ppt para acuarios de arrecife
- Aquaforest publica expresamente la composición esperable de Reef Salt a 35 ppt, por lo que el objetivo está contemplado por el fabricante y no requiere extrapolar la formulación fuera de sus referencias publicadas
- Trabajar con una consigna única facilita interpretar conjuntamente salinidad, calcio, magnesio, alcalinidad y otras mediciones relacionadas

Los valores de 33 o 34 ppt también serían biológicamente plausibles y operativamente utilizables. No se adopta 35 porque sea un valor mágico, sino porque no existe en Veril una razón específica para trabajar deliberadamente por debajo de esa referencia y sí existe una ventaja documental y metrológica en utilizarla.

La estabilidad tiene prioridad sobre la persecución de una cifra aislada. Una desviación moderada y estable no se corregirá de forma brusca, y cualquier cambio de consigna deberá tratarse como una decisión operativa explícita.

La masa de sal no define por sí sola el resultado. Aquaforest publica aproximadamente 390 g por 10 L como referencia de preparación a 33 ppt, pero también caracteriza Reef Salt a 35 ppt. En Veril, la cantidad inicial se utilizará únicamente como punto de partida y la aceptación se realizará mediante medición de la salinidad preparada, no mediante una equivalencia fija entre gramos y `S_P`.

## Estado de la decisión

**Adoptado:** La reposición por evaporación utilizará agua RO/DI mediante el ATO. El llenado inicial del ciclado utilizará agua de mar filtrada con UV suministrada por Elite Reef Kanarias y se comprobará hasta `S_P = 35`. Una vez finalizado el ciclado, el agua nueva para cambios posteriores se preparará con agua de ósmosis RO/DI y Aquaforest Reef Salt, salvo decisión documentada distinta.

**Previsto:** La química se interpretará mediante parámetros individuales, relaciones entre variables y tendencias temporales, teniendo en cuenta la fase del sistema y la carga existente.

**Pendiente:** Todavía deben quedar fijados en los documentos propietarios los métodos concretos, la frecuencia de medición, los límites de aceptación por fase y cualquier estrategia de dosificación que llegue a adoptarse. Esta ficha no anticipa esas decisiones.

## Relaciones específicas de Veril

La interpretación química deberá relacionarse con:

- La evaporación y el funcionamiento del ATO
- La carga biológica y la alimentación previstas
- La colonización y la maduración de las superficies
- La actividad del skimmer y la retirada de materia
- El consumo de organismos calcificadores si se incorporan
- Los cambios de agua y cualquier dosificación que se autorice
- La temperatura y la salinidad durante la toma de muestras

Una lectura puntual no cerrará por sí sola una decisión. Se registrarán el método, la fecha, la hora, la intervención previa y la tendencia necesaria para interpretar la respuesta del sistema.

La preparación, ejecución y trazabilidad de los cambios de agua pertenecen al [procedimiento operativo correspondiente](../../03_pendientes/operacion-recurrente/cambios-agua.md).

## Aplicación durante las fases operativas

El [ciclado](../../03_pendientes/ciclado/plan.md) y la [maduración](../../03_pendientes/maduracion/plan.md) mantienen sus propios protocolos. Esta ficha solo define qué relación debe conservarse entre la química medida y la configuración de Veril.

Antes de nuevas incorporaciones se comprobará que las tendencias químicas sean interpretables para la carga prevista. Una corrección química no se aplicará únicamente para perseguir una cifra aislada ni sustituirá la identificación de entradas, consumos, procesamiento o mantenimiento.

## Criterios de aceptación

- Las muestras se toman con un método y unas unidades registradas
- Salinidad y temperatura se interpretan conjuntamente con el momento de la medición
- Las tendencias de los parámetros relevantes son conocidas para la fase del sistema
- Las variaciones se relacionan con alimentación, evaporación, cambios de agua, consumo y mantenimiento
- No se utilizan proxies aislados como demostración de estabilidad o madurez
- Los cambios químicos que afecten a la población o al procesamiento quedan registrados

Las fichas de parámetros y los planes de ciclado y maduración conservan el detalle ejecutable y el estado de cada medición.
