RicardoJBarrios/acuario-veril/03_pendientes/maduracion/plan-indicadores-visuales-corales.md

# Plan de observación biológica de corales

## Estado y alcance

Este es un plan pendiente, no una decisión de incorporar fauna ni un protocolo
ya probado en Veril. Su objetivo es evaluar el uso de cambios persistentes en
organismos incorporados como avisos para medir y revisar el sistema.
Un coral puede señalar que algo ha cambiado, pero no mide por sí mismo un
parámetro ni identifica de forma fiable una deficiencia.

La aplicación empieza cuando Veril tenga corales introducidos y aclimatados.
Esta primera versión prioriza los organismos ya contemplados en el diseño, sin
cerrar la posibilidad de evaluar otros candidatos mediante el proceso normal
de selección y compatibilidad. Este documento no autoriza incorporaciones. La
selección y el estado de cada organismo siguen perteneciendo a
[candidatos de corales y análogos](../../02_configuracion/03_biologia/02_candidatos/corales-y-analogos.md).

## Criterio de interpretación

Se distinguirán tres niveles:

- **Aviso visual general**: cambio persistente respecto al patrón habitual de
  una colonia; justifica observar y medir, pero no señala una causa concreta.
- **Sospecha para priorizar una medición**: una observación puede hacer
  razonable comprobar primero ciertos parámetros, sin descartar otros.
- **Diagnóstico**: requiere resultados de medición y contexto compatibles. La
  apariencia del coral por sí sola no basta.

El cierre, la retracción, la pérdida de color, el crecimiento lento y la
recesión de tejido son signos compartidos por múltiples factores: temperatura,
salinidad, luz, flujo, nutrientes, química, manipulación, plagas o enfermedad.
No se cambiarán varias variables a la vez ni se dosificarán elementos traza
por el color de un coral.

## Organismos que pueden observarse en Veril

El plan parte de los organismos ya contemplados en el diseño biológico. Su
presencia aquí no cambia su estado de candidato ni autoriza su incorporación.

| Organismo | Observación que se puede registrar | Qué justifica hacer | Especificidad y encaje |
| --- | --- | --- | --- |
| *Zoanthus* | Proporción de pólipos abiertos durante el fotoperiodo, aspecto/color y continuidad de la colonia | Si el cambio es sostenido frente a su propio patrón, revisar primero temperatura, salinidad, PAR y flujo, y medir la química general | Aviso visual general, no indicador de KH, Ca, Mg o nutrientes por separado. Es compatible con el plan de isla separable de zoántidos |
| GSP | Proporción o superficie de pólipos extendidos, estado de la base y avance del tapiz | Si permanece cerrado o cambia de forma persistente, comprobar condiciones generales, detrito, flujo y posibles irritantes o plagas | Aviso visual general de baja especificidad. No consume esqueleto calcáreo y no sirve para inferir consumo de KH, Ca o Mg |
| *Acropora* y *Montipora*, si se reconsideran en el futuro | Evolución fotográfica del borde de crecimiento, puntas, base, color y extensión de pólipos | Una pérdida de crecimiento o tejido justifica medir KH y Ca y revisar sus tendencias; comprobar además Mg si hay precipitación o dificultad anómala para mantener Ca/KH, y revisar nutrientes, PAR, flujo, temperatura, salinidad y plagas | Pueden aportar observación del crecimiento calcáreo, pero no se proponen como centinelas iniciales. Ambas continúan como opciones no iniciales |
| *Xenia*, solo si se incorporase más adelante por una decisión independiente | Frecuencia de pulsación de pólipos comparables, observada en condiciones repetibles | Una caída sostenida justificaría comprobar el sistema y el estado de la colonia | Hay evidencia experimental de respuesta de *Xenia umbellata* a cambios de pH y otros tratamientos, pero la señal depende de especie y condiciones. No identifica una causa ni justifica añadir Xenia a Veril |
| Algas coralinas costrosas, si aparecen durante la maduración | Presencia, extensión y cambio fotográfico sobre superficies fijas | Registrar como evolución ecológica del sustrato; no deducir estroncio, calcio, pH ni estabilidad química a partir de su aparición o ausencia | Algunas especies inducen asentamiento larvario de corales en ensayos experimentales, pero la respuesta depende del par de especies. Eso no convierte su crecimiento visible en un test químico del acuario ni en criterio de incorporación |

Las fichas de [*Zoanthus*](../../01_verilpedia/02_biologia/03_cnidarios-sesiles/02_analogos-coraliformes/zoanthus.md), [GSP](../../01_verilpedia/02_biologia/03_cnidarios-sesiles/01_corales/01_blandos/gsp.md), [SPS](../../01_verilpedia/02_biologia/03_cnidarios-sesiles/01_corales/04_sps/README.md), [*Acropora*](../../01_verilpedia/02_biologia/03_cnidarios-sesiles/01_corales/04_sps/acropora.md), [*Montipora*](../../01_verilpedia/02_biologia/03_cnidarios-sesiles/01_corales/04_sps/montipora.md) y [*Xenia* / *Anthelia*](../../01_verilpedia/02_biologia/03_cnidarios-sesiles/01_corales/01_blandos/xenia-anthelia.md) describen los límites particulares de estas observaciones.

## Revisión de las asociaciones propuestas

La siguiente tabla conserva las asociaciones sugeridas en la propuesta
compartida por el usuario, pero ajusta su confianza para que funcionen como
prioridades de comprobación y no como diagnósticos visuales.

| Señal propuesta | Valoración original aportada | Primera comprobación razonable | Resolución para Veril |
| --- | --- | --- | --- |
| SPS con poco o ningún crecimiento apical | «Bastante útil» para KH/Ca | Revisar registros de KH y Ca, y verificar crecimiento mediante imágenes comparables | Asociación condicional. El crecimiento también depende de luz, flujo, nutrientes, temperatura y estado de la colonia; el coral no permite separar esas causas |
| Puntas SPS blancas o descritas como «quemadas» después de un cambio químico | «Bastante característica» de swing de KH | Revisar qué cambió, cuándo y cuánto; medir KH y comprobar nutrientes, luz y flujo | Hipótesis de relación con un cambio de KH, no señal específica. No subir ni bajar KH basándose solo en la apariencia |
| STN o recesión de tejido en SPS | Confianza media para KH/inestabilidad | Registrar extensión y velocidad, revisar base, contacto, plagas, detrito y parámetros | Síndrome/descripción de deterioro, no diagnóstico de inestabilidad de KH. La evolución rápida requiere atención prioritaria |
| Dificultad para mantener Ca y KH, o precipitación visible | «Muy útil» como pista de Mg bajo | Confirmar mediciones y métodos; medir Mg y revisar dosificación, mezcla y superficies | Motivo razonable para medir Mg, pero no prueba que sea la causa. No atribuirlo a un coral testigo |
| Descenso general de crecimiento calcáreo | Confianza media para KH/Ca/Mg | Revisar serie de KH y Ca y distinguir consumo medido de impresión visual | Aviso lento y multicausal. La estimación de consumo debe basarse en mediciones repetidas, no solo en aspecto |
| Corales duros pálidos y con crecimiento pobre | Confianza media para NO3/PO4 bajos, KH o luz | Revisar NO3/PO4, KH, temperatura, salinidad, PAR, aclimatación y estado del tejido | Señal inespecífica. Nutrientes demasiado bajos son una posibilidad, no la conclusión automática |
| Deterioro de tonos rojos o rosas | La propuesta agrupa ambos tonos y sugiere I/K y trazas con baja confianza | Comparar fotografías con luz y exposición constantes; revisar primero condiciones generales | La guía comercial consultada separa rosa (I/Br) y rojo (K), pero esa asociación de pigmentos no demuestra una deficiencia ni permite diagnosticarla visualmente |
| Deterioro de tonos verdes o amarillos | Hipótesis de baja confianza para Fe y trazas | Comparar fotografías con luz y exposición constantes; revisar primero condiciones generales | La atribución a Fe u otros trazas es hipótesis de baja confianza. No dosificar por color |
| Deterioro de tonos azules o púrpuras | Hipótesis de baja confianza para K/trazas | Comparar fotografías con luz y exposición constantes; revisar primero condiciones generales | La atribución a K u otros trazas es hipótesis de baja confianza. No dosificar por color |
| LPS que dejan de inflarse | Reconocido como poco específico | Revisar ciclo diario, flujo, detrito, contacto, temperatura, salinidad y estado del tejido | Aviso general, no señal fiable de KH, salinidad o nutrientes concretos |
| GSP cerrado o menos extendido | Propuesto como alarma visual general, con mala capacidad diagnóstica | Comparar con su patrón durante el fotoperiodo; revisar flujo, detrito, luz y condiciones generales | Puede ser un aviso visual práctico si la colonia ya forma parte del sistema, pero no diagnostica una deficiencia |

La idea de que una alteración rápida de KH puede coincidir con daño en SPS
merece conservarse como hipótesis operativa de comprobación. No se adopta la
clasificación «bastante característica» para puntas quemadas ni se asigna una
confianza alta a la relación entre una apariencia y un elemento. La
calcificación coralina está regulada biológicamente y depende también de
condiciones ambientales; una correlación visual aislada no establece causa.

La propuesta menciona como ejemplo el programa comercial Trace-Colors de Red
Sea, que asocia elementos o grupos de elementos con pigmentos —rosa con
I/Br, rojo con K, verde/amarillo con Fe y azul/púrpura con un grupo de trazas—
y describe vías de dosificación basadas en consumo medido de calcio o en tests
de elementos.
Esto documenta la posición del fabricante, no demuestra que un cambio de color
diagnostique una carencia en Veril. El manual indica además que sus suplementos
de trazas se dosifican sin relacionarlos con los colores concretos de los
corales. Plantea medición de calcio o tests específicos para dosificar, no una
decisión basada únicamente en color.

## Aportaciones del vídeo de BorjaReef sobre bioindicadores

El vídeo [ICP en Acuario Marino: Diferencias clave entre MS y OES + Bioindicadores](https://www.youtube.com/watch?v=FD5pViduqkw), publicado el 2 de agosto de 2026, añade observaciones que conviene conservar, pero no eleva por sí solo su especificidad diagnóstica. Es una conversación divulgativa con resultados ICP y experiencias relatadas por los participantes, no un ensayo controlado de bioindicadores.

| Señal mencionada en el vídeo | Resolución para el plan |
| --- | --- |
| *Acropora* o *Montipora* que parecen blandas al cortar con pinzas, atribuido a estroncio bajo | Hipótesis anecdótica. No se cortará ni dañará una colonia para comprobar dureza. Si la fragilidad se observa durante una fragmentación necesaria por otro motivo, anotar especie, ubicación, condiciones y motivo; contrastar con Sr por ICP y con KH, Ca, crecimiento y contexto. No usarlo como diagnóstico visual |
| Más crecimiento de coralina asociado por algunos participantes a Sr/Ca adecuados o estabilidad, con desacuerdo dentro del mismo vídeo | No específico y discutido. Registrar la evolución de coralina como dato ecológico de maduración, no como señal de Sr, Ca o estabilidad. Medir cada parámetro directamente |
| Coralina costrosa como indicio de sustrato favorable y fuente de señales de asentamiento | La investigación primaria apoya que ciertas especies de coralina costrosa pueden inducir asentamiento larvario de determinados corales. La respuesta depende de las especies y condiciones experimentales; no demuestra que la cantidad de coralina visible en Veril diagnostique la calidad química del agua |
| Tonos rosados/púrpura más vivos con potasio alto, *Montipora* más oscura con K bajo y puntas rojas/rosadas de *Acropora* más pálidas o pardas | Testimonios sin unidades para las cifras 400, 440 y 450 que aparecen en la conversación, ni control de iluminación, nutrientes, especie u otras variables. Registrar color con fotografías comparables y medir K si cambia de forma persistente; no perseguir esos valores ni dosificar por color |
| pH crónicamente bajo pese a alcalinidad y ventilación adecuados como posible pista de boro bajo | Hipótesis de los participantes, reconocida como intuición sin ICP. No es un signo coralino y no basta para decidir una dosificación. Investigar el pH y confirmar boro por un método apropiado |
| Sin síntoma aparente de *Acropora* pese a un yodo que un participante describe como alto | Relato individual sin concentración, método ni evaluación subclínica. La apariencia normal no confirma que el valor sea seguro ni descarta alteraciones |
| Selenio muy bajo como posible reducción de tolerancia lumínica de *Acropora* | Afirmación oral sin estudio, concentración ni signo visual identificable. No se incorpora como indicador accionable; ante un resultado analítico real habría que verificarlo y contrastar PAR y estado del coral por separado |

El contraste bibliográfico encontró evidencia experimental de claves químicas
de algunas algas coralinas costrosas en el asentamiento larvario, incluida una
respuesta variable entre especies de coral y alga. No encontró respaldo
equivalente para usar dureza táctil del esqueleto como medida de Sr, color SPS
como test de K ni aspecto de *Acropora* como detector de Se o yodo. Esas
asociaciones permanecen como ideas de los participantes, no como conocimiento
confirmado ni decisiones de Veril. Las ideas originales y la transcripción
completa se conservan en el corpus documental local; este plan resume solo la
resolución necesaria para su aplicación en Veril.

## Registro y respuesta prevista

Cuando se incorporen colonias por razones independientes a este plan:

1. Registrar la fecha de llegada, identificación disponible, ubicación,
   aclimatación, fotoperiodo y PAR medido en la posición real cuando se
   disponga de la medición.
2. Tras la aclimatación y la apertura habitual de la colonia, obtener una
   referencia fotográfica con encuadre, hora del fotoperiodo, iluminación y
   distancia comparables. Para *Zoanthus* y GSP se puede anotar la fracción
   visible de pólipos abiertos. No se fija ahora un porcentaje de alarma.
3. Registrar cada cambio relevante del equipo, mantenimiento, alimentación,
   dosificación o agua junto a la observación. Separar observación visual de
   lectura de test y de interpretación.
4. Si hay una desviación sostenida, repetir la observación y medir primero los
   parámetros pertinentes. En un SPS, incluir KH y Ca; medir Mg si hay una
   razón independiente para sospecharlo. Comprobar nutrientes, luz, flujo,
   temperatura, salinidad y signos de plaga o enfermedad según el caso.
5. Ante pérdida activa de tejido, mortalidad o deterioro rápido, no esperar a
   completar una serie fotográfica: registrar el episodio y revisar de
   inmediato las posibles causas, sin aplicar una corrección múltiple a ciegas.
6. No iniciar suplementos de I, K, Fe ni otros trazas sin una medición o una
   base técnica independiente que justifique la intervención.

Los umbrales de persistencia y frecuencia de observación quedan pendientes de
definirse con el patrón real de Veril. No se importarán umbrales publicados para
otra especie, colonia, luminaria o sistema.

## Criterios para revisar el plan

Antes de tratar estas señales como parte de la rutina:

- Debe existir una colonia incorporada por decisión biológica independiente y
  suficientemente aclimatada para establecer su patrón local
- Debe poder distinguirse su ciclo normal de apertura y cierre de una desviación
- Las fotografías o anotaciones deben permitir comparar observaciones
- Las mediciones asociadas deben registrar método, unidad y fecha
- Las decisiones posteriores deben basarse en las mediciones y el diagnóstico
  diferencial, no en el nombre de «coral testigo»

La revisión futura puede ajustar qué señales resultan prácticas en Veril. No
convertirá un síntoma inespecífico en un test químico ni autorizará incorporar
corales de mayor exigencia.

## Fuentes y alcance

- Matriz de asociaciones entre síntomas coralinos y parámetros aportada para
  evaluación el 2026-09-26. No incluía enlaces a las publicaciones o vídeos
  originales; se conserva como conjunto de hipótesis atribuidas, no como fuente
  científica identificada.
- BorjaReef (2026-08-02), [ICP en Acuario Marino: Diferencias clave entre MS y OES + Bioindicadores](https://www.youtube.com/watch?v=FD5pViduqkw), conversación y experiencias de participantes. Las afirmaciones relevantes para este plan se conservan por marcas de tiempo en las ideas del corpus y se resuelven por separado; no se tratan como ensayo controlado.
- Tebben et al. (2015), [Chemical mediation of coral larval settlement by crustose coralline algae](https://pmc.ncbi.nlm.nih.gov/articles/PMC4650656/), ensayos de asentamiento larvario. Apoya señales químicas de CCA en condiciones experimentales, no el uso del crecimiento de coralina como indicador de estroncio o estabilidad en un acuario.
- Whitman et al. (2020), [Settlement of larvae from four families of corals in response to a crustose coralline alga and its biochemical morphogens](https://pmc.ncbi.nlm.nih.gov/articles/PMC7532448/), ensayo con *Porolithon onkodes* y larvas de 15 especies de coral bajo condiciones controladas.
- Abdul Wahab et al. (2023), [Hierarchical settlement behaviours of coral larvae to common coralline algae](https://pmc.ncbi.nlm.nih.gov/articles/PMC10083175/), ensayo con 15 especies de coral y 15 de coralina costrosa; las respuestas dependieron de las combinaciones de especies y del hábitat lumínico.
- Ross, Falter y McCulloch (2017), [Active modulation of the calcifying fluid carbonate chemistry and seasonally invariant coral calcification at sub-tropical limits](https://pmc.ncbi.nlm.nih.gov/articles/PMC5653831/), análisis geoquímico de *Acropora yongei* y *Pocillopora damicornis* en ambiente natural. No valida la dureza percibida al cortar como medida de Sr disuelto.
- Tilstra et al. (2023), [Short-term ocean acidification decreases pulsation and growth of the widespread soft coral *Xenia umbellata*](https://pmc.ncbi.nlm.nih.gov/articles/PMC10651030/), ensayo de acuario de 21 días con tratamientos de pH controlados; apoya una respuesta de esa especie bajo esas condiciones, no un diagnóstico doméstico universal.
- Thobor et al. (2022), [The pulsating soft coral *Xenia umbellata* shows high resistance to warming when nitrate concentrations are low](https://pmc.ncbi.nlm.nih.gov/articles/PMC9537297/), experimento sobre calentamiento y tratamientos de nitrato; muestra que la respuesta depende del contexto experimental.
- Klinke et al. (2022), [Phosphate enrichment increases the resilience of the pulsating soft coral *Xenia umbellata* to warming](https://www.frontiersin.org/journals/marine-science/articles/10.3389/fmars.2022.1026321/), experimento sobre fosfato y calentamiento; el fosfato por sí solo no produjo un cambio significativo de pulsación en sus condiciones.
- Tambutté et al. (2011), [Coral biomineralization: From the gene to the environment](https://doi.org/10.1016/j.jembe.2011.07.026), revisión de la regulación biológica y ambiental de la calcificación.
- Red Sea (2019), [manual Trace-Colors](https://redseafish.com/wp-content/uploads/2020/11/24692-NEW-Manual-Colors-Complete-GB-_2019A.pdf), fuente del fabricante para las asociaciones de pigmentos y la dosificación por consumo de calcio o tests específicos; el manual dice que la dosificación no se relaciona con los colores de corales concretos. No es validación científica independiente del diagnóstico visual.
- van Woesik et al. (2022), [Coral-bleaching responses to climate change across biological scales](https://pmc.ncbi.nlm.nih.gov/articles/PMC9545801/), revisión sobre factores que pueden intervenir en blanqueamiento y estrés.
- [Coral Pathology: Identification and Management in Aquarium](https://www.oceano.org/wp-content/uploads/2026/02/Coral-Pathology-Identification-and-Management-in-Aquarium_institut_oceanographique_monaco.pdf), manual institucional de patología coralina en acuario; fuente de orientación diagnóstica general, no validación de una señal centinela concreta.

La evidencia de experimentos controlados con *Xenia* es directa pero
condicional a especie y tratamiento. Las asociaciones entre signos visuales de
SPS/LPS y una deficiencia elemental concreta no quedan verificadas por las
fuentes anteriores y se mantienen como hipótesis para orientar mediciones.
