RicardoJBarrios/acuario-veril/03_pendientes/maduracion/plan.md

# Plan de maduración de Veril

## Objetivo y alcance

La maduración comienza después de cerrar el [plan de ciclado](../ciclado/plan.md). Desarrolla la estabilidad ecológica posterior a la prueba del biofiltro y no constituye una segunda prueba de amonio ni una autorización automática para introducir toda la población.

Busca observar la colonización, la sucesión biológica, la estabilidad química y la respuesta del sistema a incorporaciones graduales. También debe permitir comprobar si la carga y el mantenimiento requeridos siguen siendo sostenibles después de cada incorporación.

La maduración no tiene una duración fija. Se avanza según condiciones observables y no por una fecha.

La observación de corales, cuando se incorporen por decisión independiente, se
desarrolla en el [plan de observación biológica](plan-indicadores-visuales-corales.md).

## Condiciones de partida

Antes de iniciar esta fase:

- La segunda carga del ciclado se ha procesado dentro del plazo fijado
- NH3/NH4 y NO2 permanecen en el límite de aceptación definido para los tests utilizados
- pH, alcalinidad, salinidad y temperatura son estables
- Retorno, circulación, oxigenación, skimmer y ATO funcionan de forma fiable
- El sistema se recupera correctamente tras un corte eléctrico
- No hay animales ni materia orgánica en descomposición

El agua nueva o de reposición se preparará con agua osmotizada de RO/DI y **Aquaforest Reef Salt**, según la ficha del producto.

## Principios de maduración

- Cada incorporación es opcional y debe tener una finalidad definida
- Al principio se modifica una variable cada vez
- La estabilidad precede al aumento de carga
- Una película, turbidez o alga no constituye por sí sola una emergencia
- No se perseguirá agua cristalina mediante cambios, carbón o resinas sin una causa identificada
- La alimentación se ajustará a la biomasa y al alimento disponibles
- Inocular un organismo no equivale a demostrar madurez ecológica
- Los cambios de agua forman parte del mantenimiento y no se usarán solo para borrar señales visuales

## Protocolo de mantenimiento

La rutina de maduración conservará las condiciones estables y permitirá detectar cambios antes de añadir una nueva carga. La [documentación de operación](../operacion-recurrente/README.md) y las fichas de cada equipo definen los procedimientos generales y el funcionamiento de los componentes; este plan añade únicamente las condiciones de aplicación y registro propias de la maduración:

- Revisar el nivel del display y de la cámara de retorno, el ATO, el retorno, la circulación, la superficie y el skimmer
- Reponer la evaporación únicamente con agua osmotizada de RO/DI, mediante el ATO o manualmente si fuera necesario
- Comprobar salinidad y temperatura y corregir solo con una actuación registrada
- Retirar manualmente los detritos visibles cuando se acumulen o puedan afectar al flujo, al rebosadero o a los organismos
- Limpiar el cristal cuando dificulte observar el sistema, conservando las superficies destinadas a la colonización
- Vaciar y limpiar la copa del skimmer según la acumulación real, sin cambiar a la vez otros elementos relevantes
- Limpiar entradas, rejillas, rotores y equipos cuando la suciedad reduzca su funcionamiento
- Realizar cambios de agua como parte de la rutina definida o cuando la química o la biología lo justifiquen
- No añadir productos, medios, alimento ni organismos para corregir una apariencia aislada

Después de cada incorporación se mantendrá una ventana de observación sin nuevas cargas. Se registrarán la intervención, los parámetros medidos, el estado del agua, la respuesta de los organismos, la carga de mantenimiento requerida y la decisión siguiente.

## Fases

### Fase A — estabilización posterior al ciclado

Se mantiene el sistema sin nuevas incorporaciones hasta observar una tendencia estable. Se registra:

- NH3/NH4 y NO2 como control de seguridad
- NO3 y PO4 como nutrientes
- pH y alcalinidad
- Salinidad y temperatura
- Retorno, circulación, skimmer, ATO y oxigenación
- Biofilm, turbidez, sedimentos, película, algas y olor

La luz permanece apagada o en iluminación ambiental hasta que exista una finalidad biológica concreta. La configuración y la introducción de la luz se rigen por [iluminación](../../02_configuracion/01_dimensiones/04_iluminacion.md).

### Fase B — luz y sucesión observable

La luz se introduce progresivamente cuando exista una finalidad biológica y las condiciones sean estables. Se registra la intensidad, el fotoperiodo, la fecha, el motivo y la respuesta observada.

No se cambian simultáneamente luz, nutrientes y población sin registrar la relación entre los cambios. Un apagado total solo se utilizará ante un problema concreto y documentado.

### Criterio preventivo: fosfato indetectable

Un fosfato indetectable no se tratará como un objetivo de limpieza ni como un
diagnóstico aislado. Se considerará una señal que requiere contexto, sobre
todo si se repite junto con nitrato bajo, cambios de alimentación, medios
adsorbentes, consumo biológico intenso, deterioro de corales o aparición de
organismos oportunistas.

El error preventivo que se quiere evitar es mantener o aumentar una estrategia
de reducción de nutrientes cuando el PO₄ ya no es detectable, o intentar
corregirlo con un producto cuya formulación incluya una fuente de carbono o
fósforo particulado sin conocer su efecto real. Una lectura cero no demuestra
por sí sola limitación, pero tampoco debe celebrarse automáticamente como un
estado deseable.

Si Veril tuviera corales y apareciera ese patrón, la posible respuesta sería:

1. Repetir la medición con el mismo método, registrando unidad, límite de
   detección, hora y relación con alimentación y cambios de agua.
2. Revisar entradas, exportación, adsorbentes, detritos, roca, sustrato,
   biomasa y evolución conjunta de NO₃ y PO₄.
3. No añadir más productos reductores ni carbono por rutina mientras la causa
   siga sin aclararse.
4. Si la lectura baja persiste y la respuesta biológica es compatible con una
   limitación, decidir una intervención gradual y específica, documentando
   producto, dosis, volumen operativo y respuesta.
5. Mantener una ventana de observación después de una sola modificación.

En el caso atribuido a [Michael Reef Tenerife](https://www.youtube.com/watch?v=TeoZRt9Elws&t=775s), el autor comunica que la comida sola y un producto combinado
con fuente de carbono no le resolvieron el fosfato indetectable; también
describe algas asociadas a un producto particulado. Comunica mejoría tras usar
pequeñas aportaciones repetidas de fosfato líquido y mantener una lectura
detectable. Esto sirve como advertencia y como hipótesis de intervención, no
como pauta transferible ni como prueba de que esos síntomas tengan siempre la
misma causa.

### Fase C — incorporaciones graduales

Las entradas biológicas posteriores son módulos independientes, no etapas obligatorias ni una secuencia fija. Pueden incluir colonización de superficies, microfauna, organismos consumidores, organismos sésiles o fauna móvil, siempre que exista una decisión específica de compatibilidad. La incorporación de microfauna se desarrolla en el [plan específico de microfauna](plan-microfauna.md).

Cada incorporación se valorará por:

- Procedencia y estado sanitario
- Tamaño adulto y comportamiento
- Alimentación y carga añadida
- Necesidades de luz, flujo, sustrato y refugio
- Capacidad de observación, mantenimiento y contención

No se introducirán varias cargas biológicas nuevas en la misma ventana de observación.

## Bioseguridad

Toda roca, sustrato, soporte, organismo o agua procedente de otro sistema puede introducir organismos no deseados. Antes de incorporarlo se registrará la procedencia y se inspeccionarán plagas, lesiones, detritos y organismos acompañantes.

No se contempla una pecera independiente de cuarentena y aclimatación en la configuración actual. Cada entrada de fauna requerirá una decisión sanitaria y de aclimatación específica.

La bioseguridad reduce el riesgo, pero no garantiza la ausencia de organismos indeseados.

## Puertas de decisión

### Roja — detener incorporaciones

Se detiene la progresión si aparece amonio o nitrito por encima del límite, deterioro sostenido de pH o alcalinidad, mala oxigenación, descomposición, obstrucción del rebosadero, pérdida de retorno, circulación insuficiente, mortalidad o estrés persistente.

No se añade fauna, alimento ni productos correctores por rutina. Se identifica la causa y se aplica solo la intervención necesaria.

### Amarilla — mantener y observar

Se mantiene la fase si la tendencia es irregular, los nutrientes son indetectables o una película no compromete el oxígeno ni el funcionamiento.

Se conserva la carga y el equipo, se registra la evolución y no se introduce una nueva variable.

### Verde — avanzar un módulo

Se puede avanzar cuando los parámetros principales son estables, existe una finalidad clara para la incorporación y la rutina de mantenimiento funciona sin correcciones múltiples.

Se incorpora un solo módulo y se observa su respuesta antes de continuar.

## Criterios de maduración inicial

La fase inicial estará preparada para una primera incorporación cuando se cumplan conjuntamente:

- Capacidad nitrificante demostrada en el ciclado
- NH3/NH4 y NO2 sostenidos en el límite de aceptación
- pH, alcalinidad, salinidad y temperatura estables
- NO3 y PO4 conocidos y con una tendencia interpretable
- Biofilm y sucesión observables sin deterioro persistente
- Circulación, retorno, oxigenación y skimmer fiables
- Rutina de alimentación, observación y mantenimiento preparada para la incorporación elegida

Antes de pasar a una primera carga calcificadora o a una pauta de dosificación,
se tomará la muestra **ICP-02** definida en el [plan transversal de medición y
tests](../operacion-recurrente/medicion-y-tests.md#análisis-icp-de-laboratorio).
Será un contraste de composición elemental y agua de aporte; no sustituye los
criterios anteriores ni autoriza por sí sola la incorporación.

«Maduro» no significa estable para cualquier población. Cada aumento de carga requiere una nueva observación.

## Registro mínimo

Para cada fase o incorporación se anotarán:

- Fecha y hora
- Cambio realizado y motivo
- Producto, organismo, proveedor, lote o cantidad cuando aplique
- Volumen de agua cambiado, si lo hubo
- Luz, skimmer, retorno y circulación
- NH3/NH4, NO2, NO3, PO4, pH, alcalinidad, salinidad y temperatura
- Aspecto del agua, biofilm, algas, sedimentos, olor y comportamiento
- Decisión siguiente y condición que la activa
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
