RicardoJBarrios/acuario-veril/01_verilpedia/05_productos/08_fritz-fishless-fuel/etiqueta-envase-veril-2026-09-24.jpg

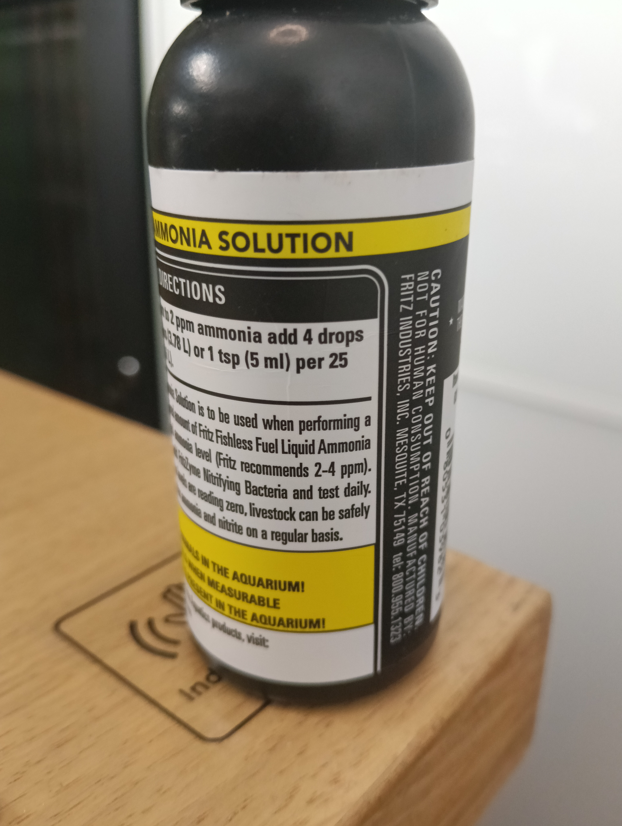
01_verilpedia/05_productos/08_fritz-fishless-fuel/etiqueta-envase-veril-2026-09-24.jpg
