RicardoJBarrios/acuario-veril/01_verilpedia/05_productos/09_fritzzyme-9/etiqueta-envase-veril-2026-09-24.jpg

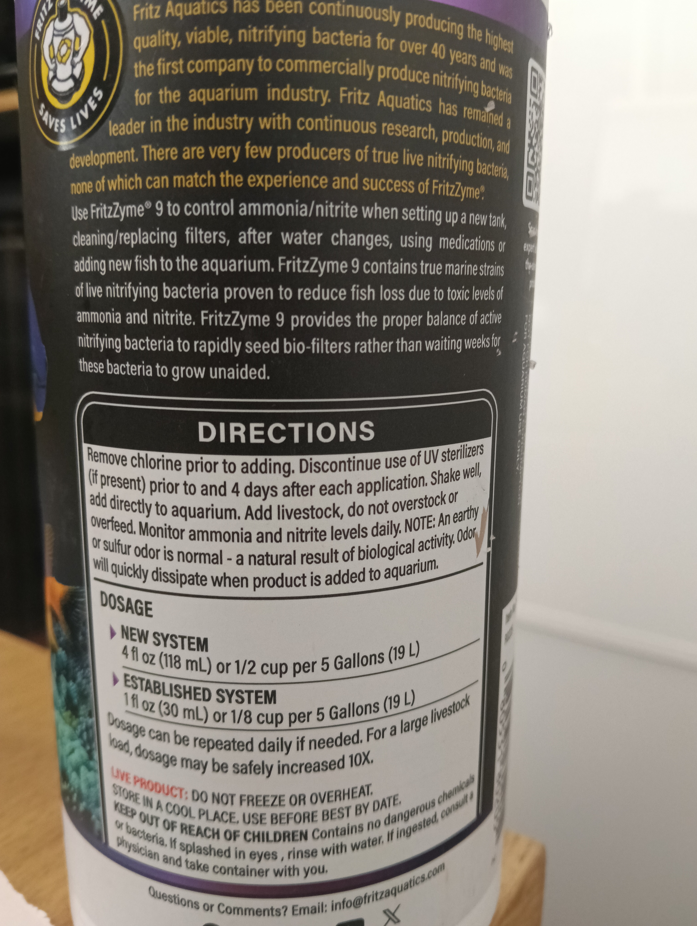
01_verilpedia/05_productos/09_fritzzyme-9/etiqueta-envase-veril-2026-09-24.jpg
