RicardoJBarrios/acuario-veril/02_configuracion/02_hardscape/rocas/roca-01-vista-lateral-b.jpg

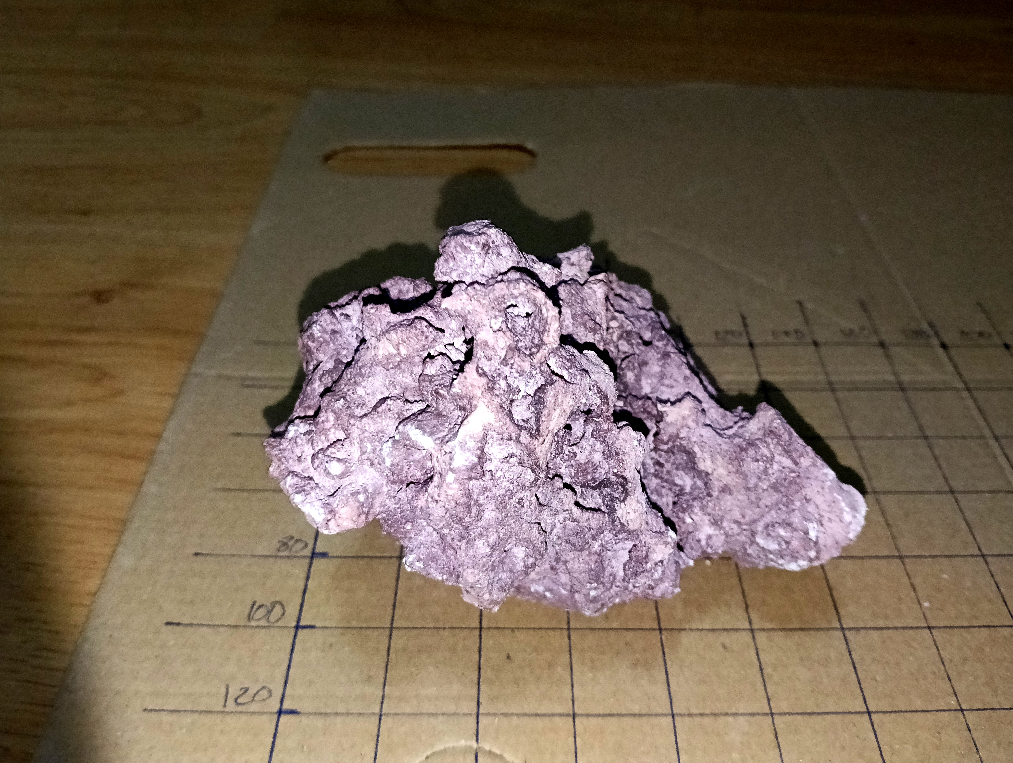
02_configuracion/02_hardscape/rocas/roca-01-vista-lateral-b.jpg
