RicardoJBarrios/acuario-veril/02_configuracion/02_hardscape/rocas/roca-03-vista-inferior.jpg

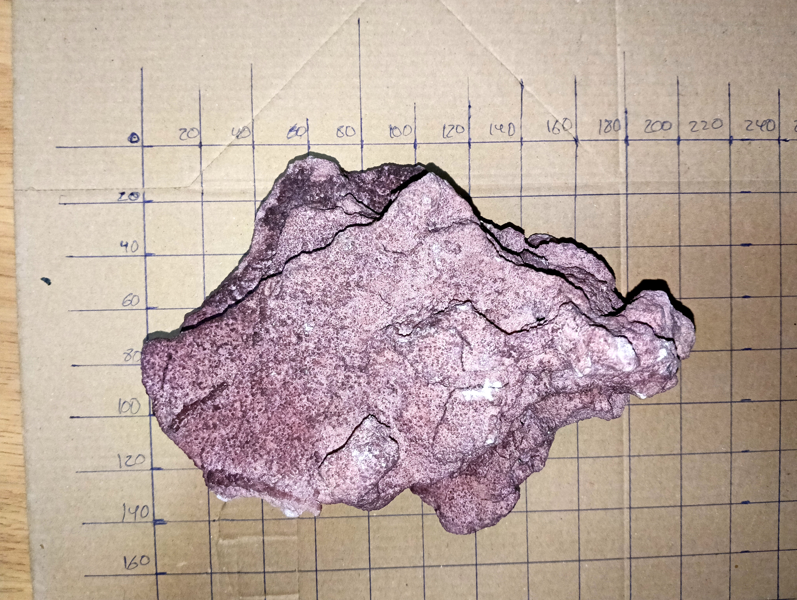
02_configuracion/02_hardscape/rocas/roca-03-vista-inferior.jpg
