RicardoJBarrios/acuario-veril/02_configuracion/02_hardscape/rocas/roca-05-vista-inferior.jpg

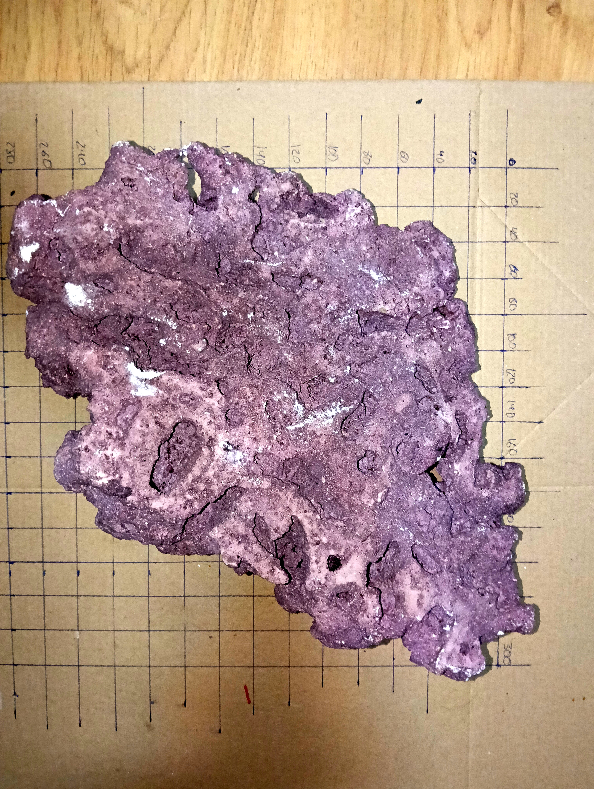
02_configuracion/02_hardscape/rocas/roca-05-vista-inferior.jpg
