RicardoJBarrios/acuario-veril/02_configuracion/02_hardscape/rocas/roca-07-vista-lateral-a.jpg

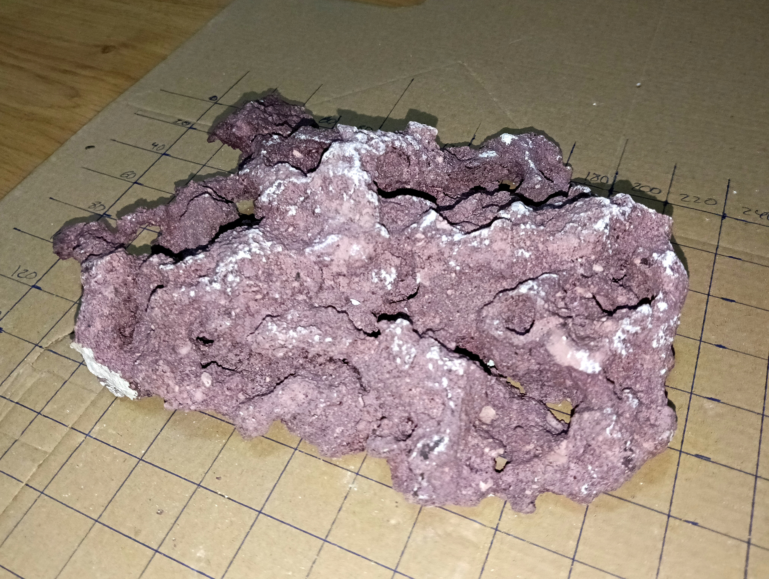
02_configuracion/02_hardscape/rocas/roca-07-vista-lateral-a.jpg
