RicardoJBarrios/acuario-veril/02_configuracion/02_hardscape/rocas/roca-10-vista-lateral-a.jpg

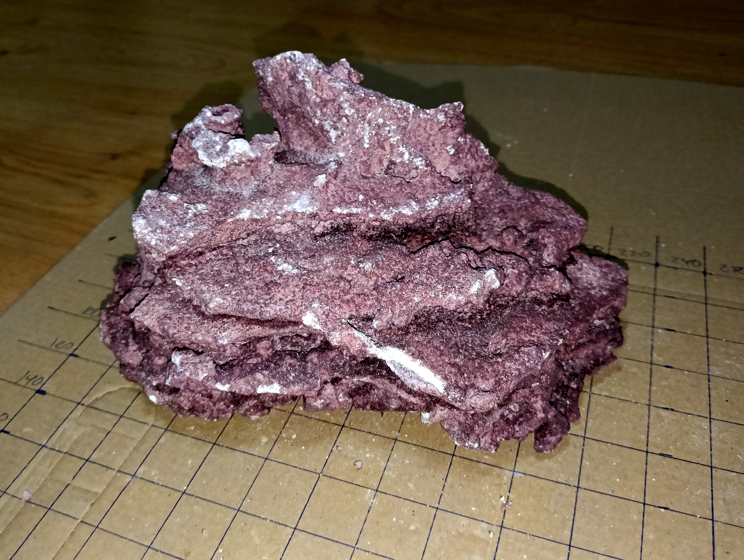
02_configuracion/02_hardscape/rocas/roca-10-vista-lateral-a.jpg
