RicardoJBarrios/acuario-veril/04_operaciones/2026/09/2026-09-13-observacion-cambio-color-hardscape/evidencias/IMG20260913015540.jpg

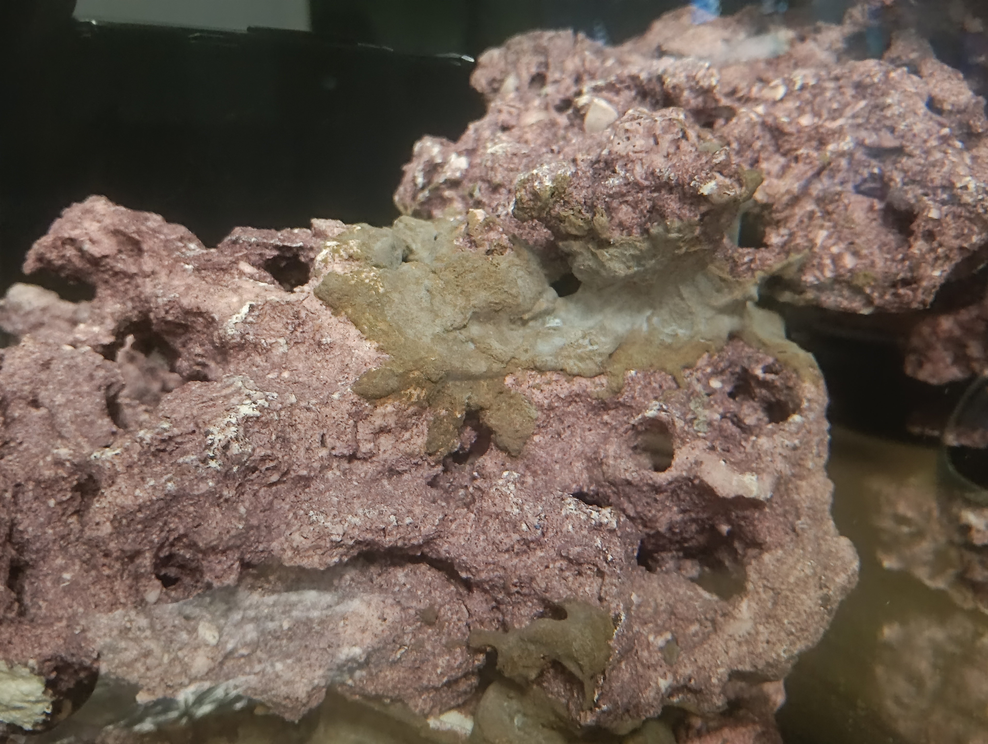
04_operaciones/2026/09/2026-09-13-observacion-cambio-color-hardscape/evidencias/IMG20260913015540.jpg
