RicardoJBarrios/acuario-veril/04_operaciones/2026/09/2026-09-24-recepcion-equipo-ro6cb/evidencias/IMG20260924143053.jpg

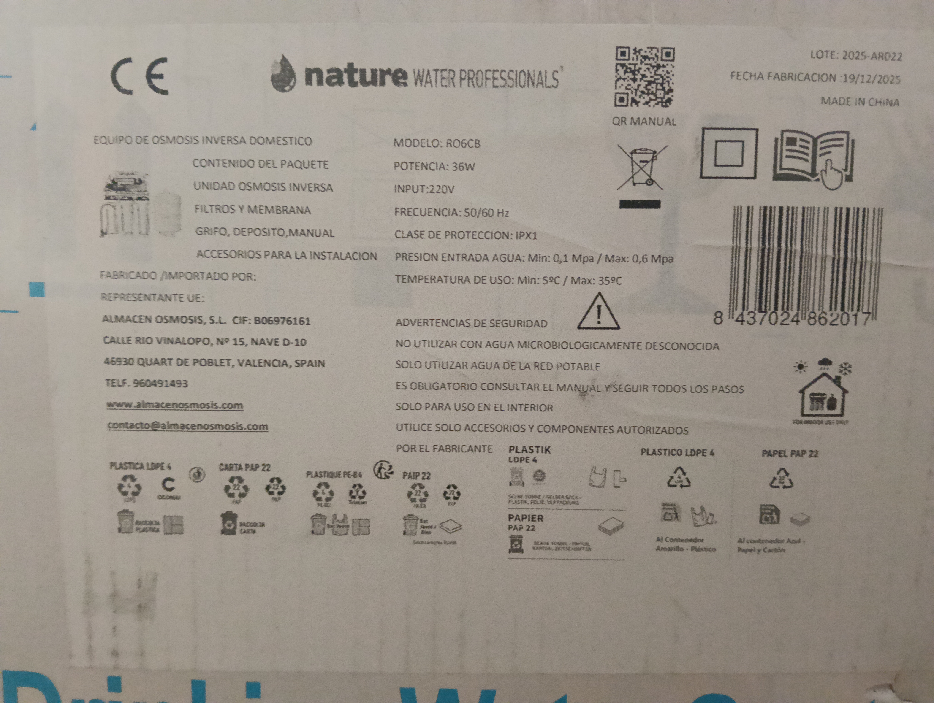
04_operaciones/2026/09/2026-09-24-recepcion-equipo-ro6cb/evidencias/IMG20260924143053.jpg
