RicardoJBarrios/acuario-veril/05_multimedia/2026-09-06-composicion-acuario.png

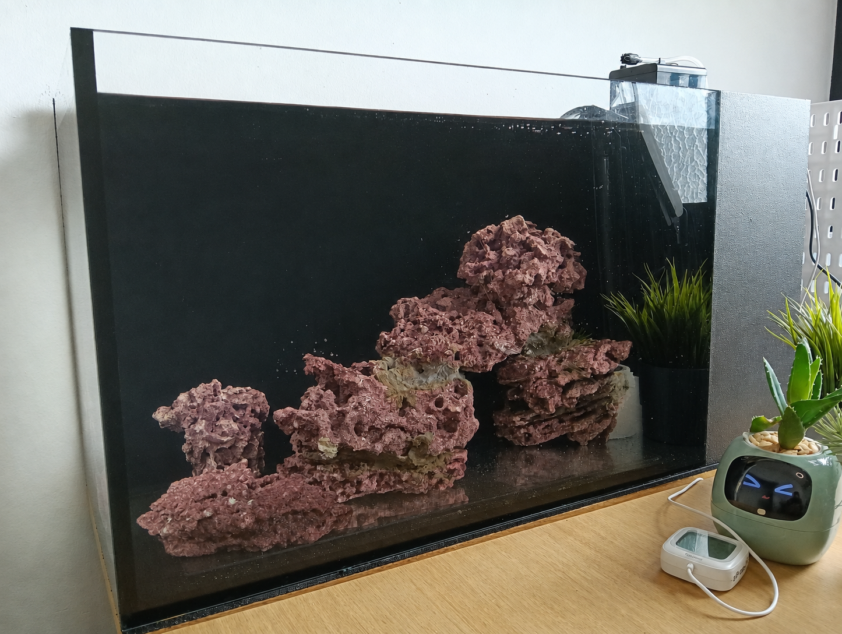
05_multimedia/2026-09-06-composicion-acuario.png
