RicardoJBarrios/acuario-veril/04_operaciones/2026/09/2026-09-05-montaje-y-primer-llenado/README.md

# 2026-09-05 — Montaje, fijación del hardscape y primer llenado

## Estado

Operación ejecutada con incidencia resuelta el 6 de septiembre

## Objetivo

Instalar y fijar la composición elegida, realizar el primer llenado con agua de mar filtrada con UV y comprobar inicialmente el retorno y el agua recibida.

## Entradas

- Roca D-D Marco Coralline Rock inventariada previamente
- Agua de mar suministrada en dos recipientes de capacidad nominal de 30 L y uno de 20 L; el volumen efectivamente trasvasado no se midió
- Dos bidones auxiliares de 15 L: uno lleno y otro con una cantidad pequeña; permanecen fuera del sistema
- Sicce Micra Plus 600 como bomba de retorno
- Tetra Test 7in1 y refractómetro D-D The Aquarium Solution AQPR001

## Ejecución

- Se instaló la composición rocosa sin arena
- Se fijaron las uniones estructurales de las rocas con **AF Stone Fix** durante la misma operación
- Se llenaron el display y las cámaras con agua de mar de esos recipientes; no se registró el volumen efectivamente introducido
- Se activó el retorno para una primera comprobación
- Se realizó una caracterización preliminar del agua recibida

### Corrección posterior sobre el volumen de llenado

Anotación del **23 de septiembre de 2026**: el registro original trató la
capacidad nominal conjunta de los recipientes (80 L) como si fuera el volumen
trasvasado. El propietario indica que seguramente se introdujo menos. Como no
se midió el volumen vertido, los 80 L no deben interpretarse como cantidad
incorporada al sistema.

## Resultado del hardscape

- La masa principal quedó formada por las rocas 10 y 07 en la base izquierda, 09 en el arco, 03 en la base derecha, 04 en la terraza y 08 en la masa alta derecha
- Se conservaron dos islas separadas de la masa principal
- La estructura quedó fijada con AF Stone Fix además de sus apoyos y encajes
- La aceptación mecánica e hidráulica definitiva quedó pendiente

La aplicación del adhesivo no sustituye la comprobación posterior de los apoyos, la estabilidad, los márgenes, el acceso ni la circulación.

La descripción visual completa está en el [registro del hardscape](hardscape.md).

## Incidencia del retorno

El nivel de la cámara Retorno descendió hasta dejar la bomba parcialmente descubierta y aparecieron muchas microburbujas. Se apagó el retorno de forma preventiva. No se produjo una validación hidráulica completa.

## Caracterización preliminar del agua

| Parámetro | Lectura | Límite de interpretación |
| --- | ---: | --- |
| NO₃ | 0 mg/L | Tira, lectura aproximada |
| NO₂ | 0 mg/L | Tira, lectura aproximada |
| GH | Aproximadamente 8 °dH | No interpretable como dureza marina precisa |
| KH | Aproximadamente 6–19 °dH | Intervalo visual demasiado amplio |
| pH | Aproximadamente 7,6–8,0 | Resolución insuficiente para aceptar el agua |
| Cl₂ | 0 mg/L | Sin cloro detectable mediante la tira |
| Salinidad | Aproximadamente 35,5–36 ppt | Lectura provisional con muestra a 28,1 °C |

Estas lecturas no aceptan todavía el agua para el ciclado. La salinidad debe repetirse después de limpiar y verificar el cero del refractómetro; pH y alcalinidad requieren métodos adecuados para agua marina. Los bidones auxiliares no se incluyen en el volumen introducido ni en el volumen operativo.

## Evidencias

- [Fotografías del hardscape instalado](evidencias/)
- [Fotografía de la tira Tetra 7in1](evidencias/Tetra-7in1_2026-09-06.jpg)

El nombre del archivo de la tira contiene la fecha de archivo `2026-09-06`; la operación se documentó como realizada el 5 de septiembre. No se infiere una hora de ejecución.

## Pendientes derivados

- [x] Elevar el nivel y repetir la prueba del retorno
- [ ] Medir el volumen operativo real con niveles definitivos, sustrato y equipos instalados
- [ ] Repetir la salinidad y completar pH, alcalinidad, amonio y nitrito antes del ciclado
- [ ] Validar márgenes, apoyos, circulación y acceso después de la fijación
- [ ] Confirmar el curado del AF Stone Fix según las instrucciones del producto
- [ ] Incorporar la arena solo después de cerrar la fase previa de limpieza y observación
