RicardoJBarrios/acuario-veril/01_verilpedia/04_hardware/xgb-830/manual-original/IMG20260916184034.jpg

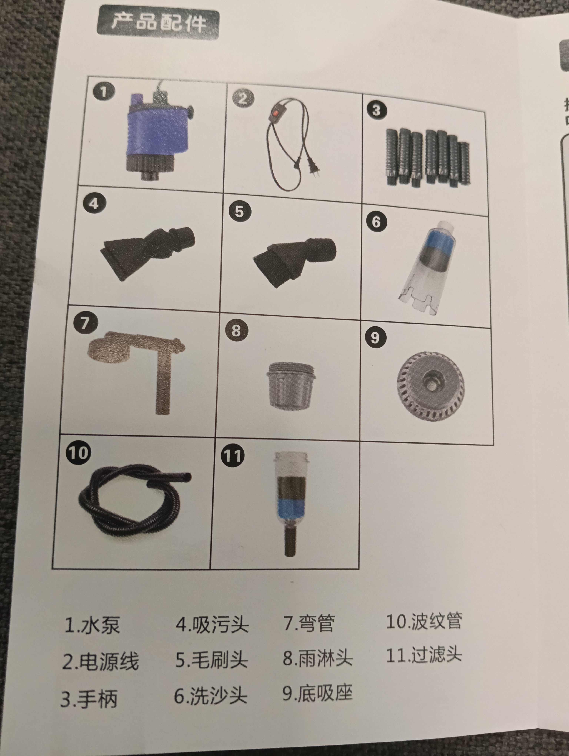
01_verilpedia/04_hardware/xgb-830/manual-original/IMG20260916184034.jpg
