RicardoJBarrios/acuario-veril/01_verilpedia/04_hardware/xgb-830/manual-original/IMG20260916184049.jpg

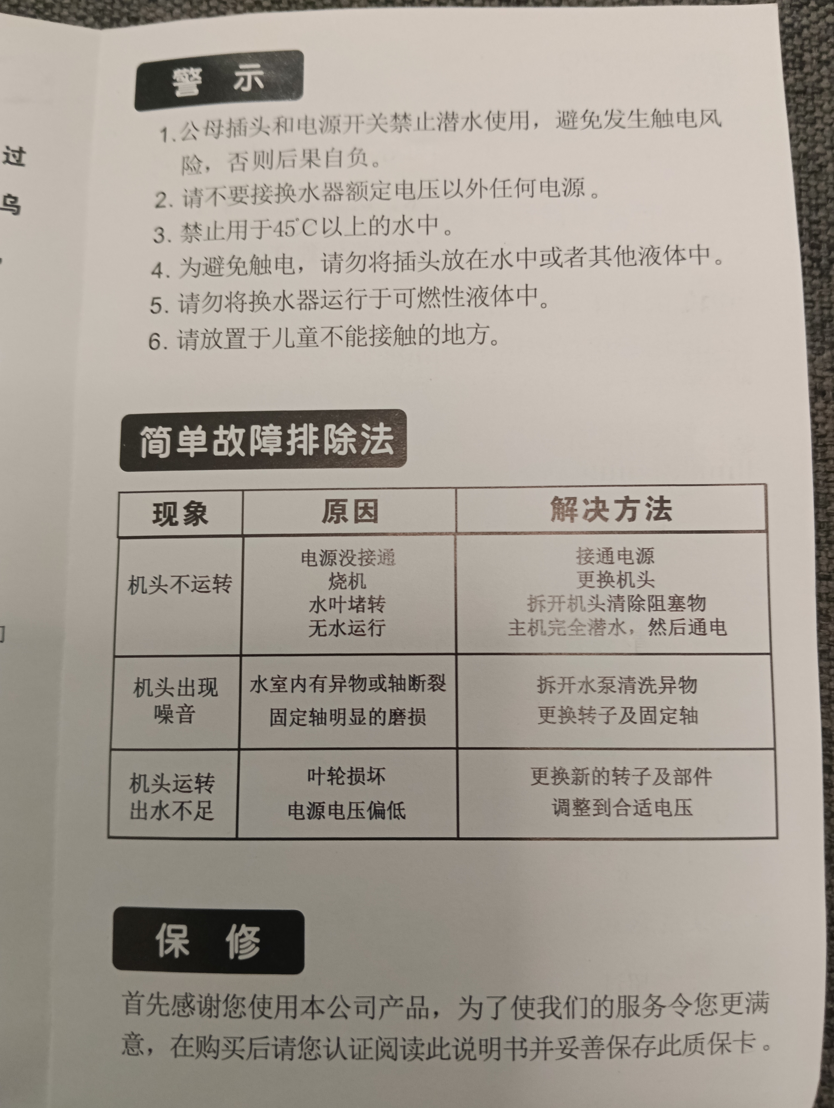
01_verilpedia/04_hardware/xgb-830/manual-original/IMG20260916184049.jpg
