RicardoJBarrios/acuario-veril/04_operaciones/2026/09/2026-09-05-montaje-y-primer-llenado/evidencias/Tetra-7in1_2026-09-06.jpg

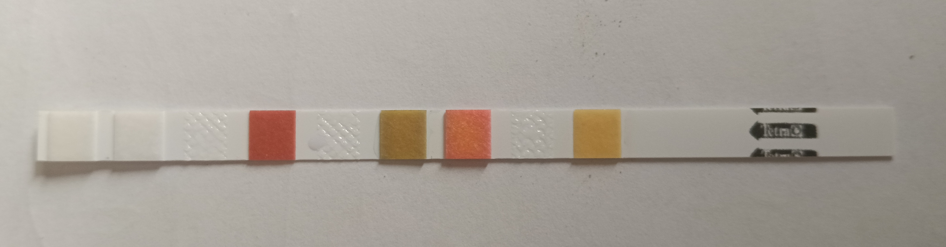
04_operaciones/2026/09/2026-09-05-montaje-y-primer-llenado/evidencias/Tetra-7in1_2026-09-06.jpg
