RicardoJBarrios/acuario-veril/01_verilpedia/05_productos/14_tetra-test-7-en-1/tetra-test-7-en-1.md

# Tetra Test 7 en 1

## Identificación

| Campo | Dato |
| --- | --- |
| Marca | Tetra |
| Producto | Tetra Test 7 en 1 |
| Presentación disponible | 50 tiras |
| Variables indicadas | pH, KH, GH, NO2, NO3, Cl2 y CO2 |
| Estado en Veril | Adquirido |

## Especificaciones declaradas

| Campo | Dato |
| --- | --- |
| Presentación comercial localizada | 50 tiras |
| Lectura | Comparación visual con la escala del envase |
| Tiempo publicado | Aproximadamente 1 minuto para leer los valores |
| Uso declarado | Seguimiento rápido de valores del agua y alerta temprana |

## Función documentada

Tiras multiparámetro para una caracterización rápida y orientativa del agua. Tetra indica siete valores: pH, dureza de carbonatos (KH), dureza general (GH), nitrito (NO₂⁻), nitrato (NO₃⁻), cloro (Cl₂) y dióxido de carbono (CO₂). La lectura se realiza comparando los colores con la escala del envase dentro del tiempo indicado.

El procedimiento publicado por Tetra consiste en sumergir la tira, agitarla aproximadamente dos segundos, retirar el exceso de agua y leerla alrededor de un minuto después. No deben tocarse los campos reactivos ni mantenerse bajo agua corriente.

## Uso en Veril

Se utilizará para la caracterización inicial del agua y como referencia auxiliar. Los tests Salifert de amonio y nitrito serán los métodos principales para el seguimiento del ciclado.

## Límites

- La resolución visual de una tira no permite aceptar por sí sola la química del agua marina
- Las variables de la tira no sustituyen métodos específicos para salinidad, alcalinidad, amonio u otras comprobaciones
- No se debe interpretar una lectura aproximada como una medición de precisión
- La información y los rangos de la escala están diseñados como orientación rápida y no sustituyen métodos de mayor resolución
- La dureza general, el CO₂ y el cloro no son los controles principales del ciclado marino de Veril

## Fuentes

- Instrucciones y escala del envase adquirido
- [Tetra: Test 7in1](https://www.tetra.net/es-es/productos/tetra-test-7in1)
- [Operación de primer llenado](../../../04_operaciones/2026/09/2026-09-05-montaje-y-primer-llenado/README.md)
