RicardoJBarrios/acuario-veril/01_verilpedia/04_hardware/sonoff-snzb-05p/wldc200-manual-v2-0.pdf

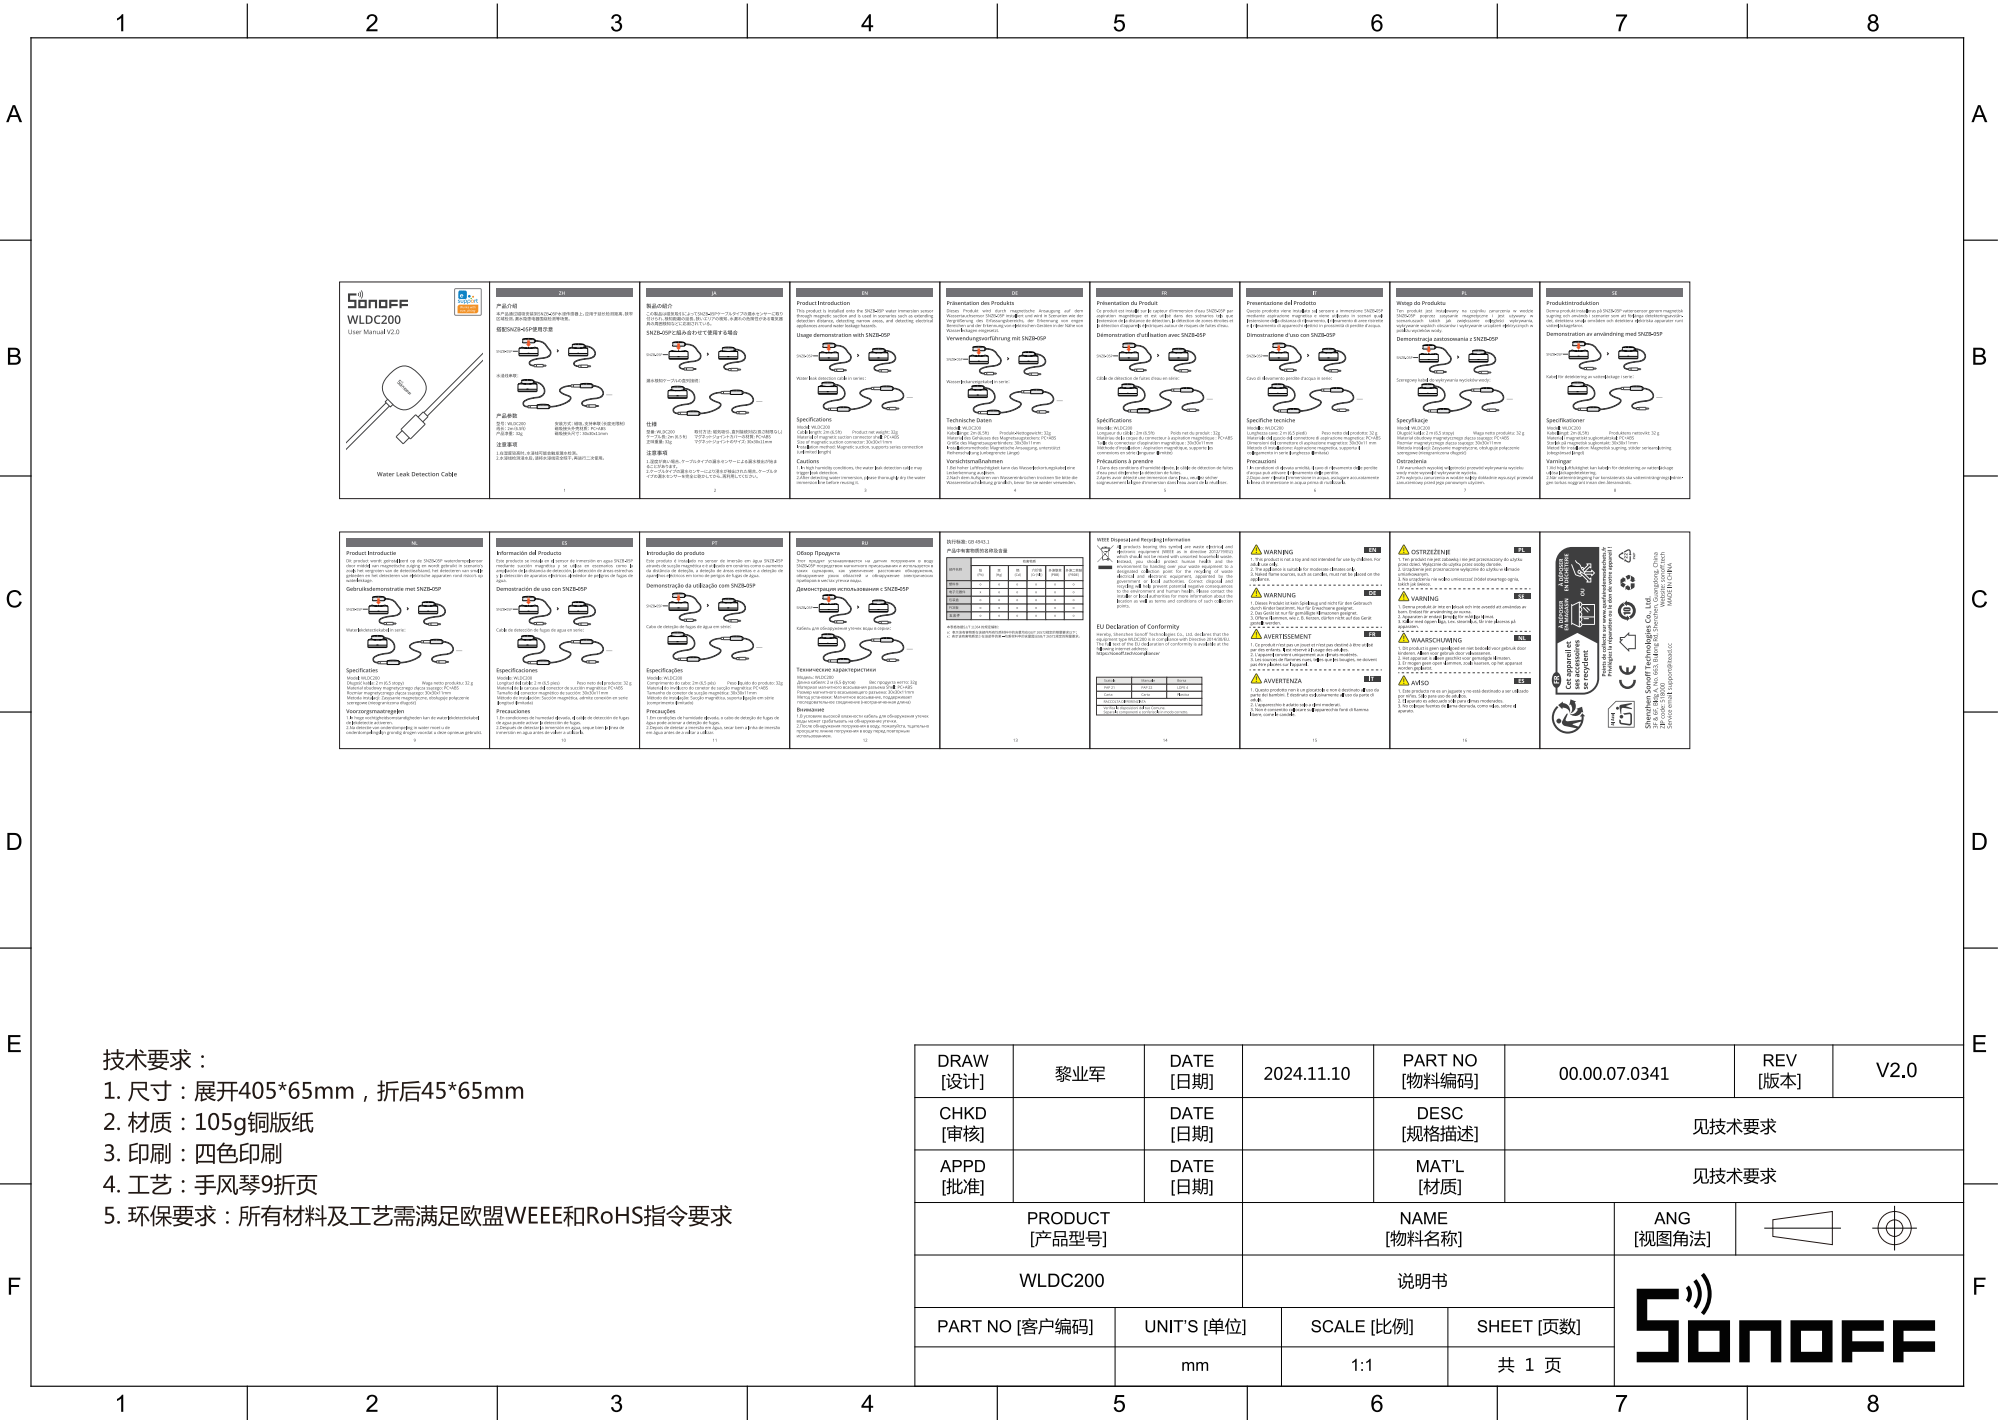
[picture p82: page 1]
