RicardoJBarrios/acuario-veril/01_verilpedia/04_hardware/zigbee-7-en-1-monitor-calidad-agua/manual-adjunto.pdf

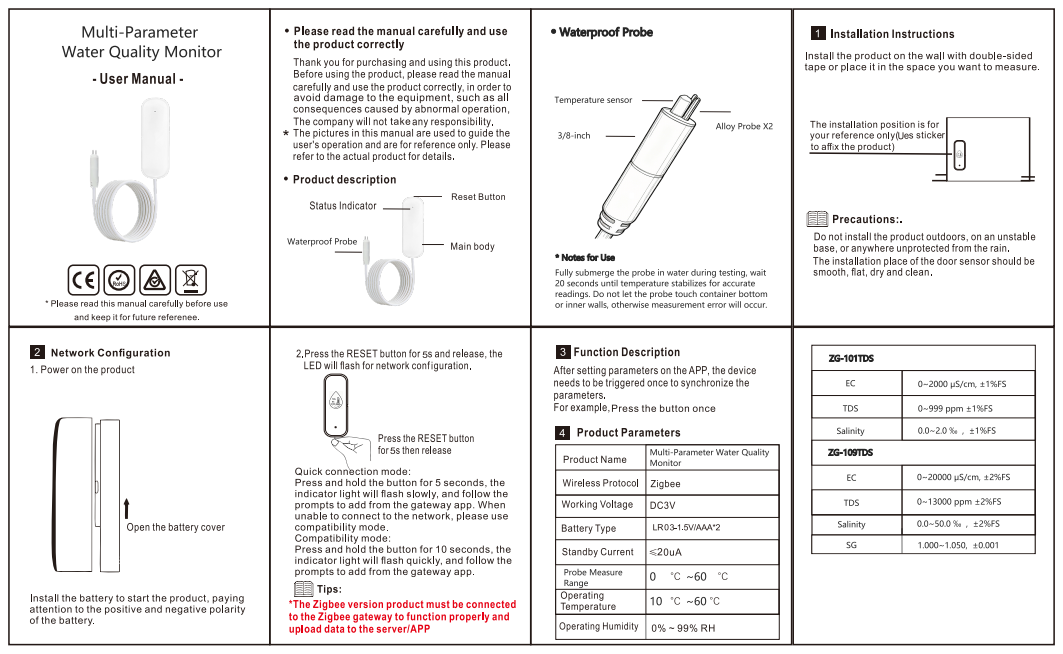
[picture p83: page 1]
